FOSSEE/eSim/code/projectManagement/openProject.rst

Open Project Button
===========================

.. automodule:: projManagement.openProject
	:members:
