FOSSEE/eSim/images/chatbot.png

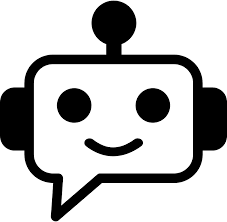
images/chatbot.png
