FOSSEE/eSim/images/esim_text.png

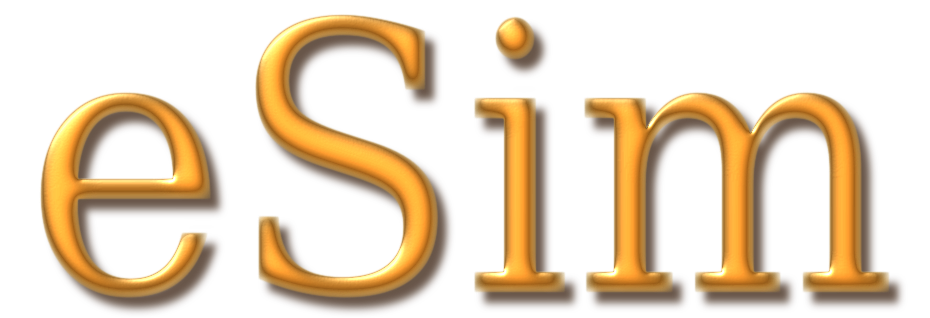
images/esim_text.png
