FOSSEE/eSim/images/footprint.png

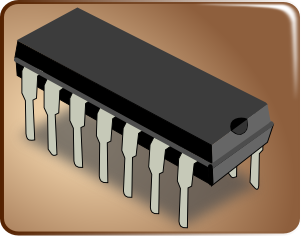
images/footprint.png
