FOSSEE/eSim/images/offline.png

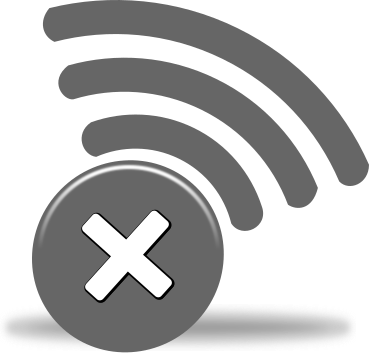
images/offline.png
