FOSSEE/eSim/images/openProject.png

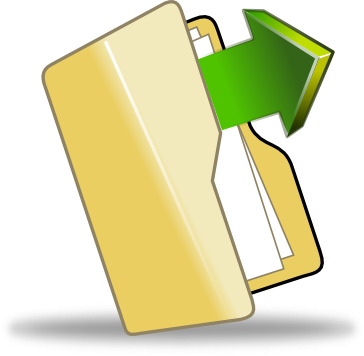
images/openProject.png
