FOSSEE/eSim/images/pcb.png

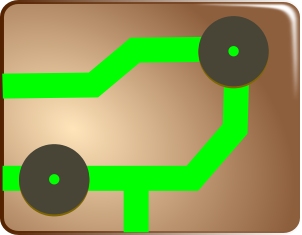
images/pcb.png
