FOSSEE/eSim/images/tracker.png

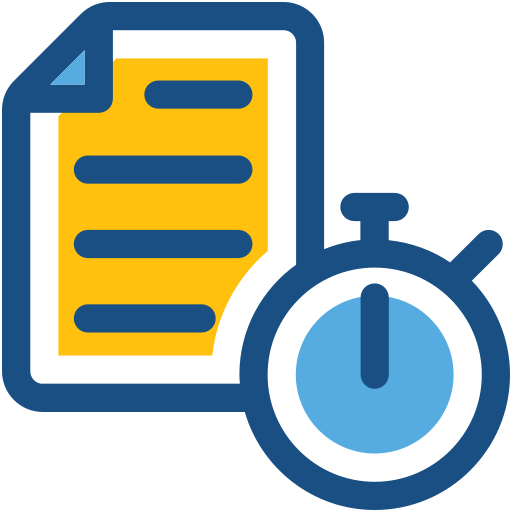
images/tracker.png
