FOSSEE/eSim/images/warning.png

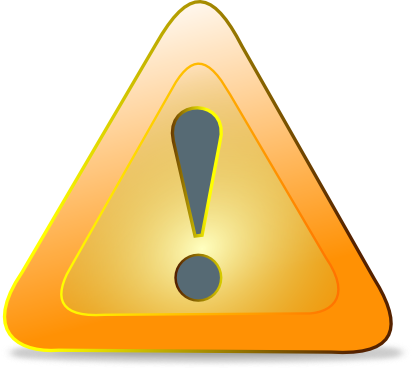
images/warning.png
