FOSSEE/eSim/SUBCKT/IC_GD74HCT58/IC_GD74HCT58.cir

.title KiCad schematic
U8 Net-_U2-Pad3_ Net-_U3-Pad3_ Net-_U11-Pad1_ d_nand
U11 Net-_U11-Pad1_ Net-_U11-Pad2_ d_inverter
U12 Net-_U11-Pad2_ Net-_U1-Pad12_ d_inverter
U1 Net-_U1-Pad1_ Net-_U1-Pad2_ Net-_U1-Pad3_ Net-_U1-Pad4_ Net-_U1-Pad5_ Net-_U1-Pad6_ Net-_U1-Pad7_ Net-_U1-Pad8_ Net-_U1-Pad9_ Net-_U1-Pad10_ Net-_U1-Pad11_ Net-_U1-Pad12_ PORT
U10 Net-_U10-Pad1_ Net-_U1-Pad10_ Net-_U10-Pad3_ d_nand
U9 Net-_U6-Pad3_ Net-_U1-Pad7_ Net-_U13-Pad1_ d_nand
U13 Net-_U13-Pad1_ Net-_U10-Pad3_ Net-_U13-Pad3_ d_nand
U15 Net-_U14-Pad2_ Net-_U1-Pad11_ d_inverter
U14 Net-_U13-Pad3_ Net-_U14-Pad2_ d_inverter
U4 Net-_U1-Pad5_ Net-_U1-Pad6_ Net-_U4-Pad3_ d_nand
U2 Net-_U1-Pad1_ Net-_U1-Pad2_ Net-_U2-Pad3_ d_nand
U3 Net-_U1-Pad3_ Net-_U1-Pad4_ Net-_U3-Pad3_ d_nand
U5 Net-_U1-Pad8_ Net-_U1-Pad9_ Net-_U5-Pad3_ d_nand
U7 Net-_U5-Pad3_ Net-_U5-Pad3_ Net-_U10-Pad1_ d_nand
U6 Net-_U4-Pad3_ Net-_U4-Pad3_ Net-_U6-Pad3_ d_nand
.end
