FOSSEE/eSim/Examples/4_bit_JK_ff/4_bit_JK_ff.sch

## KiCad design Examples/4_bit_JK_ff/4_bit_JK_ff.sch (2020-03-04)

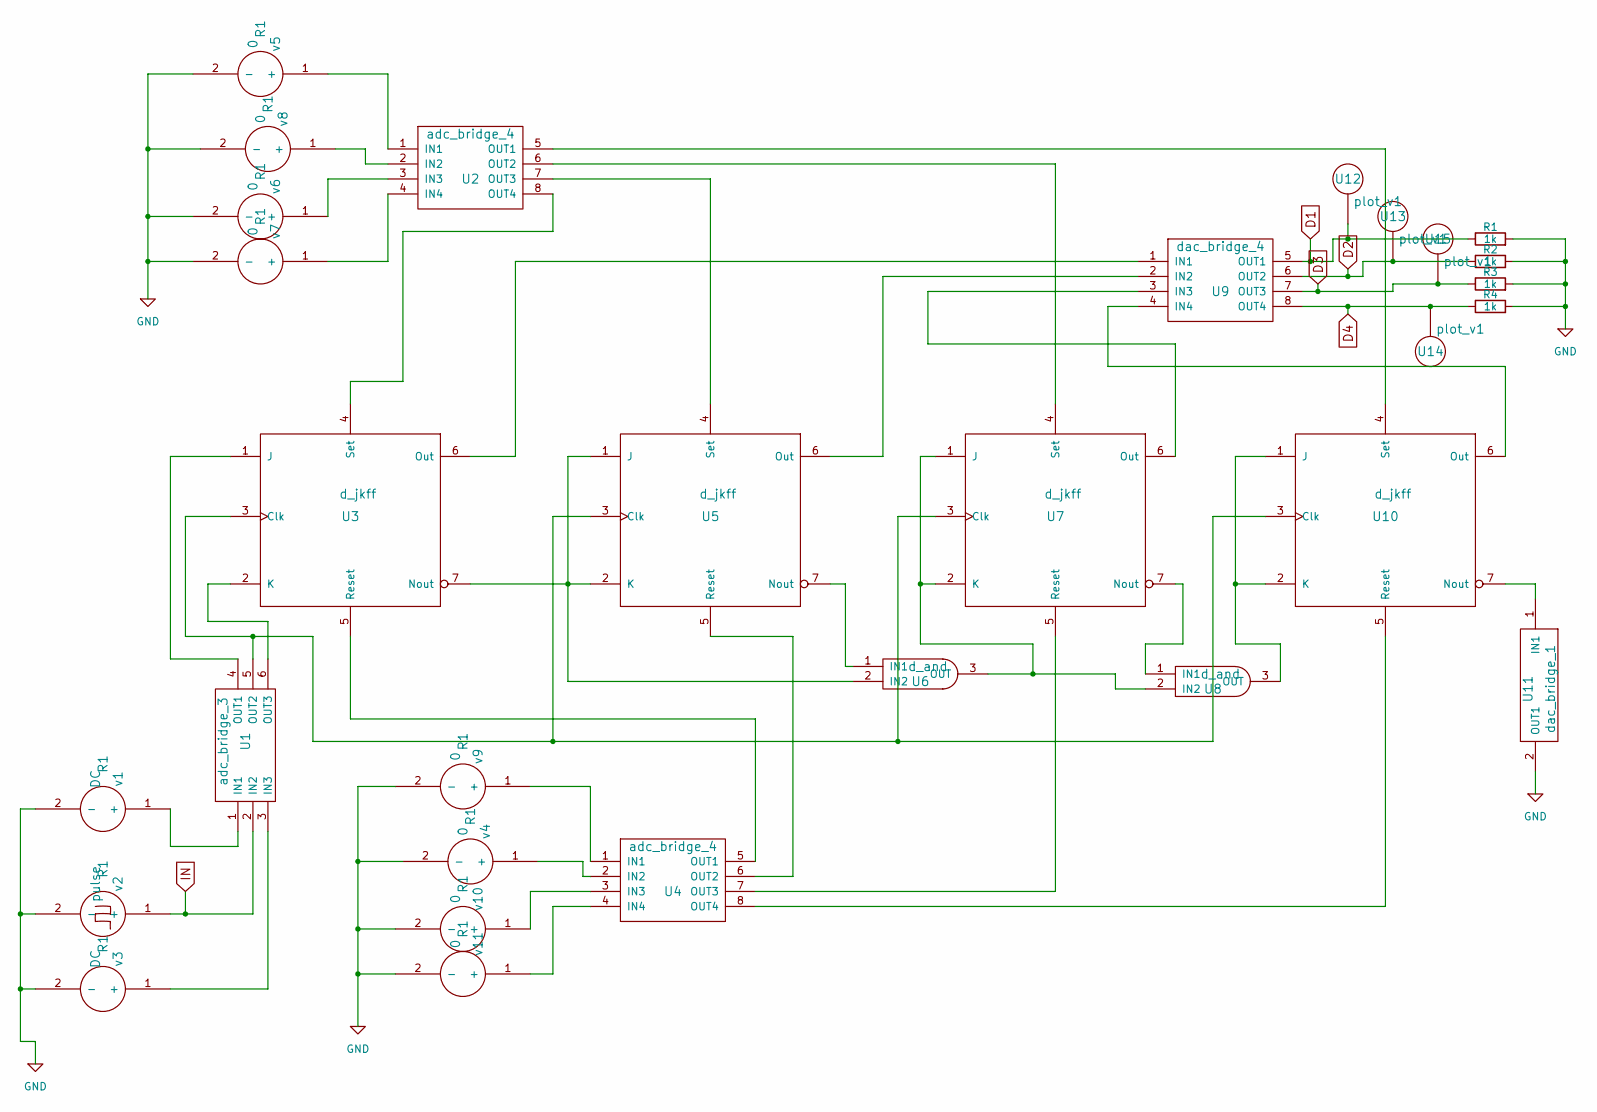
[picture p23: schematic 4_bit_JK_ff.sch]

Parts:
R1, R2, R3, R4: 1k
U1: adc_bridge_3
U2, U4: adc_bridge_4
U3, U5, U7, U10: d_jkff
U6, U8: d_and
U9: dac_bridge_4
U11: dac_bridge_1
U12, U13, U14, U15: plot_v1
v1, v3: DC; R1
v2: pulse; R1
v4, v5, v6, v7, v8, v9, v10, v11: 0; R1

Connections:
D1: R1.1, U9.5 (OUT1), U12.~
D2: R2.1, U9.6 (OUT2), U13.~
D3: R3.1, U9.7 (OUT3), U15.~
D4: R4.1, U9.8 (OUT4), U14.~
GND: R1.2, R2.2, R3.2, R4.2, U11.2 (OUT1), v1.2 (-), v2.2 (-), v3.2 (-), v4.2 (-), v5.2 (-), v6.2 (-), v7.2 (-), v8.2 (-), v9.2 (-), v10.2 (-), v11.2 (-)
IN: U1.2 (IN2), v2.1 (+)
unnamed: U1.1 (IN1), v1.1 (+)
unnamed: U1.3 (IN3), v3.1 (+)
unnamed: U1.4 (OUT1), U3.1 (J)
unnamed: U1.5 (OUT2), U3.3 (Clk), U5.3 (Clk), U7.3 (Clk), U10.3 (Clk)
unnamed: U1.6 (OUT3), U3.2 (K)
unnamed: U2.1 (IN1), v5.1 (+)
unnamed: U2.2 (IN2), v8.1 (+)
unnamed: U2.3 (IN3), v6.1 (+)
unnamed: U2.4 (IN4), v7.1 (+)
unnamed: U2.6 (OUT2), U7.4 (Set)
unnamed: U2.7 (OUT3), U5.4 (Set)
unnamed: U2.8 (OUT4), U3.4 (Set)
unnamed: U3.5 (Reset), U4.5 (OUT1)
unnamed: U3.6 (Out), U9.1 (IN1)
unnamed: U3.7 (Nout), U5.1 (J), U5.2 (K), U6.2 (IN2)
unnamed: U4.1 (IN1), v9.1 (+)
unnamed: U4.2 (IN2), v4.1 (+)
unnamed: U4.3 (IN3), v10.1 (+)
unnamed: U4.4 (IN4), v11.1 (+)
unnamed: U4.6 (OUT2), U5.5 (Reset)
unnamed: U4.7 (OUT3), U7.5 (Reset)
unnamed: U5.6 (Out), U9.2 (IN2)
unnamed: U5.7 (Nout), U6.1 (IN1)
unnamed: U6.3 (OUT), U7.1 (J), U7.2 (K), U8.2 (IN2)
unnamed: U7.6 (Out), U9.3 (IN3)
unnamed: U7.7 (Nout), U8.1 (IN1)
unnamed: U8.3 (OUT), U10.1 (J), U10.2 (K)
unnamed: U2.5 (OUT1), U10.4 (Set)
unnamed: U4.8 (OUT4), U10.5 (Reset)
unnamed: U9.4 (IN4), U10.6 (Out)
unnamed: U10.7 (Nout), U11.1 (IN1)
