FOSSEE/eSim/Examples/7805VoltageRegulator/7805VoltageRegulator.sch

## KiCad design Examples/7805VoltageRegulator/7805VoltageRegulator.sch (2020-03-04)

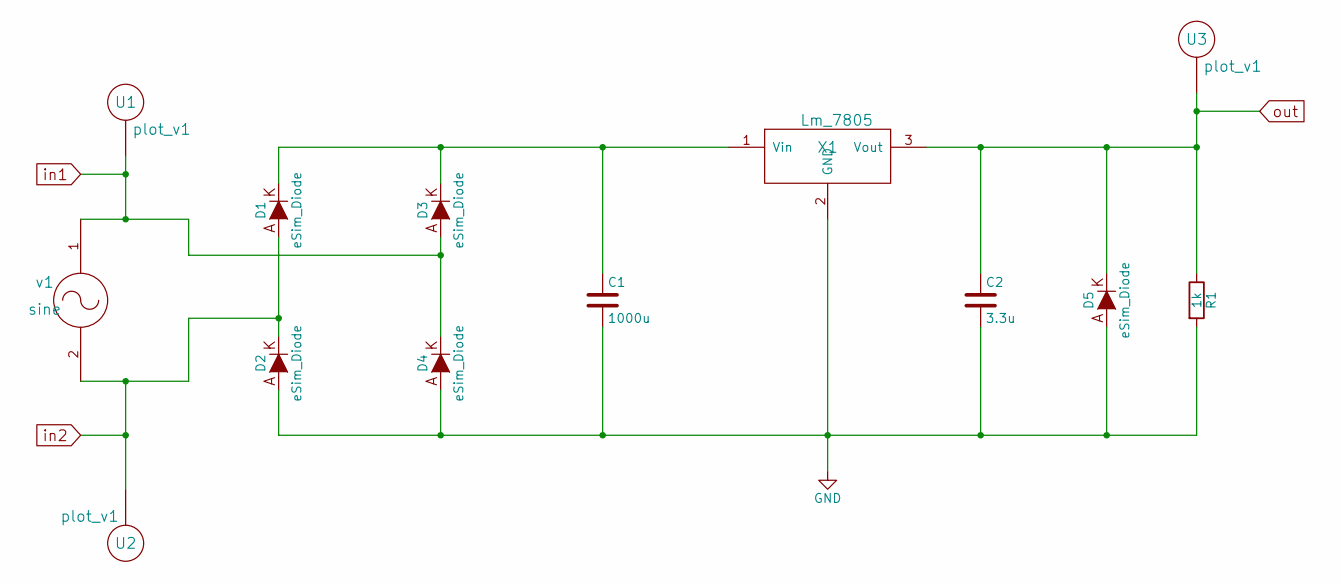
[picture p24: schematic 7805VoltageRegulator.sch]

Parts:
C1: 1000u
C2: 3.3u
D1, D2, D3, D4, D5: eSim_Diode
R1: 1k
U1, U2, U3: plot_v1
X1: Lm_7805
v1: sine

Connections:
GND: C1.2, C2.2, D2.1 (A), D4.1 (A), D5.1 (A), R1.2, X1.2 (GND)
unnamed: C1.1, D1.2 (K), D3.2 (K), X1.1 (Vin)
in1: D3.1 (A), D4.2 (K), U1.~, v1.1 (+)
in2: D1.1 (A), D2.2 (K), U2.~, v1.2 (-)
out: C2.1, D5.2 (K), R1.1, U3.~, X1.3 (Vout)
