FOSSEE/eSim/Examples/7805VoltageRegulator/lm7805.sch

## KiCad design Examples/7805VoltageRegulator/lm7805.sch (2020-03-04)

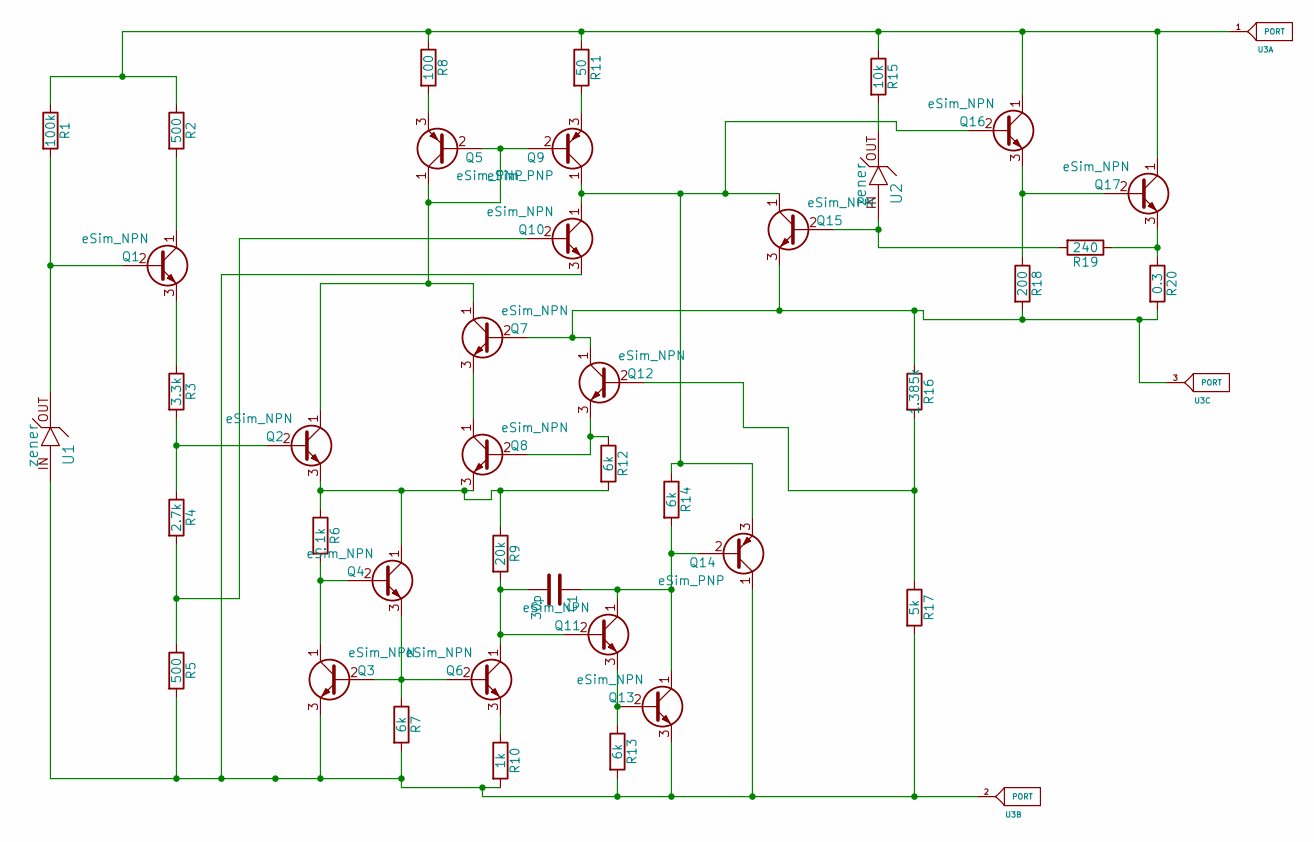
[picture p25: schematic lm7805.sch]

Parts:
C1: 30p
Q1, Q2, Q3, Q4, Q6, Q7, Q8, Q10, Q11, Q12, Q13, Q15, Q16, Q17: eSim_NPN
Q5, Q9, Q14: eSim_PNP
R1: 100k
R2, R5: 500
R3: 3.3k
R4: 2.7k
R6, R10: 1k
R7, R12, R13, R14: 6k
R8: 100
R9: 20k
R11: 50
R15: 10k
R16: 1.385k
R17: 5k
R18: 200
R19: 240
R20: 0.3
U1, U2: zener
U3: PORT

Connections:
unnamed: C1.1, Q11.1 (C), Q13.1 (C), Q14.2 (B), R14.2
unnamed: C1.2, Q6.1 (C), Q11.2 (B), R9.2
unnamed: Q1.1 (C), R2.2
unnamed: Q1.2 (B), R1.2, U1.OUT
unnamed: Q1.3 (E), R3.1
unnamed: Q2.1 (C), Q5.1 (C), Q5.2 (B), Q7.1 (C), Q9.2 (B)
unnamed: Q2.2 (B), R3.2, R4.1
unnamed: Q2.3 (E), Q4.1 (C), Q8.3 (E), R6.1, R9.1, R12.2
unnamed: Q3.1 (C), Q4.2 (B), R6.2
unnamed: Q3.2 (B), Q4.3 (E), Q6.2 (B), R7.1
unnamed: Q5.3 (E), R8.2
unnamed: Q6.3 (E), R10.1
unnamed: Q7.3 (E), Q8.1 (C)
unnamed: Q9.3 (E), R11.2
unnamed: Q9.1 (C), Q10.1 (C), Q14.3 (E), Q15.1 (C), Q16.2 (B), R14.1
unnamed: Q10.2 (B), R4.2, R5.1
unnamed: Q3.3 (E), Q10.3 (E), Q13.3 (E), Q14.1 (C), R5.2, R7.2, R10.2, R13.2, R17.2, U1.IN, U3.2
unnamed: Q11.3 (E), Q13.2 (B), R13.1
unnamed: Q7.2 (B), Q12.1 (C), Q15.3 (E), R16.1, R18.2, R20.2, U3.3
unnamed: Q12.2 (B), R16.2, R17.1
unnamed: Q8.2 (B), Q12.3 (E), R12.1
unnamed: Q15.2 (B), R19.2, U2.IN
unnamed: Q16.1 (C), Q17.1 (C), R1.1, R2.1, R8.1, R11.1, R15.1, U3.1
unnamed: Q16.3 (E), Q17.2 (B), R18.1
unnamed: Q17.3 (E), R19.1, R20.1
unnamed: R15.2, U2.OUT
