FOSSEE/eSim/Examples/Astable555/Astable555.sch

## KiCad design Examples/Astable555/Astable555.sch (2020-03-04)

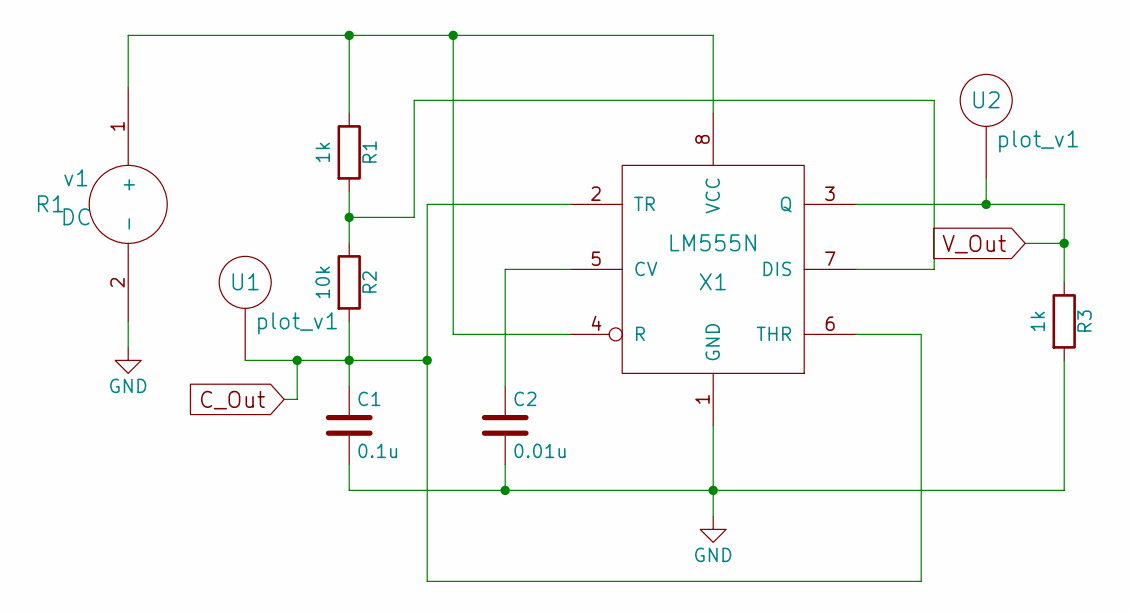
[picture p26: schematic Astable555.sch]

Parts:
C1: 0.1u
C2: 0.01u
R1, R3: 1k
R2: 10k
U1, U2: plot_v1
X1: LM555N
v1: DC; R1

Connections:
C_Out: C1.1, R2.2, U1.~, X1.2 (TR), X1.6 (THR)
GND: C1.2, C2.2, R3.2, X1.1 (GND), v1.2 (-)
unnamed: C2.1, X1.5 (CV)
unnamed: R1.1, X1.4 (R), X1.8 (VCC), v1.1 (+)
unnamed: R1.2, R2.1, X1.7 (DIS)
V_Out: R3.1, U2.~, X1.3 (Q)
