FOSSEE/eSim/Examples/BJT_Biascircuit/BJT_Biascircuit.sch

## KiCad design Examples/BJT_Biascircuit/BJT_Biascircuit.sch (2020-03-04)

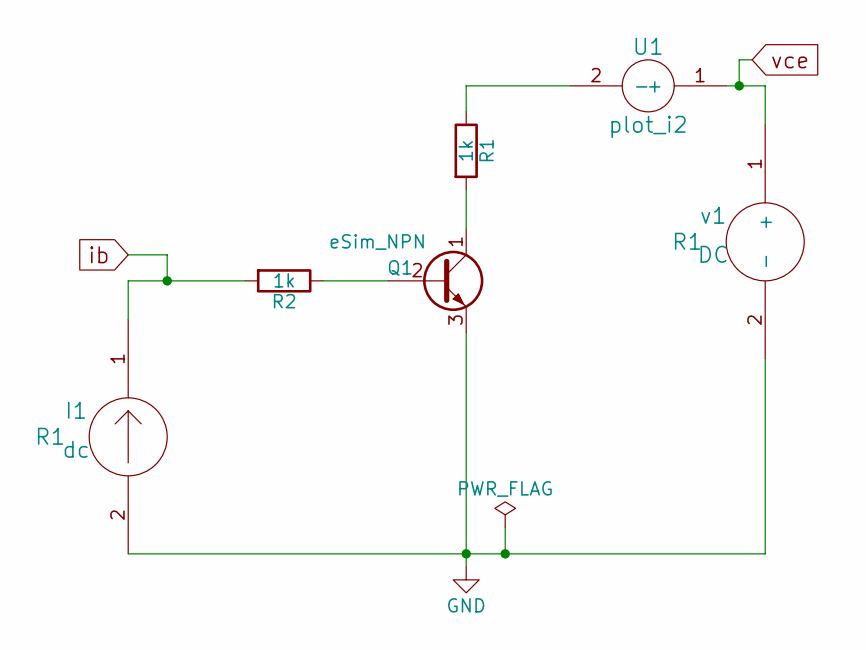
[picture p27: schematic BJT_Biascircuit.sch]

Parts:
I1: dc; R1
Q1: eSim_NPN
R1, R2: 1k
U1: plot_i2
v1: DC; R1

Connections:
GND: I1.2, Q1.3 (E), v1.2 (-)
unnamed: Q1.1 (C), R1.2
unnamed: Q1.2 (B), R2.1
unnamed: R1.1, U1.2 (-)
ib: I1.1, R2.2
vce: U1.1 (+), v1.1 (+)
