FOSSEE/eSim/Examples/BJT_CB_config/BJT_CB_config.sch

## KiCad design Examples/BJT_CB_config/BJT_CB_config.sch (2020-03-04)

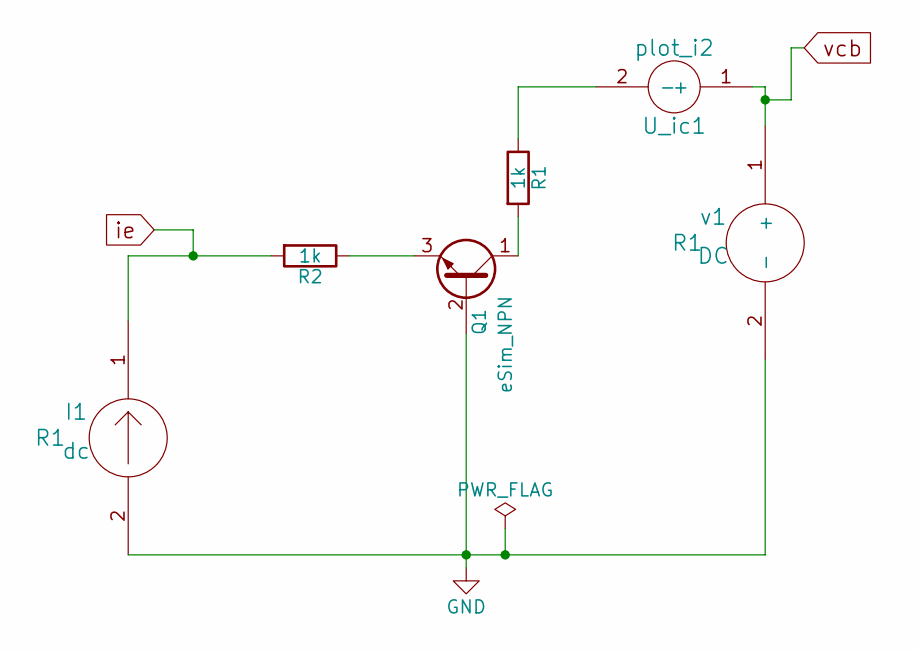
[picture p28: schematic BJT_CB_config.sch]

Parts:
I1: dc; R1
Q1: eSim_NPN
R1, R2: 1k
U_ic1: plot_i2
v1: DC; R1

Connections:
GND: I1.2, Q1.2 (B), v1.2 (-)
unnamed: Q1.1 (C), R1.2
unnamed: Q1.3 (E), R2.1
unnamed: R1.1, U_ic1.2 (-)
ie: I1.1, R2.2
vcb: U_ic1.1 (+), v1.1 (+)
