FOSSEE/eSim/Examples/BJT_Frequency_Response/BJT_Frequency_Response.sch

## KiCad design Examples/BJT_Frequency_Response/BJT_Frequency_Response.sch (2020-03-04)

Schematic: BJT_Frequency_Response.sch

Parts:
C1, C3: 40u
C2: 100u
Q1: eSim_NPN
R1: 50
R2: 200k
R3: 50k
R4: 1.5k
R5: 2k
R6: 1k
U1: plot_v1
U2: plot_phase
U3: plot_log
v1: DC; R1
v2: AC; R1
