FOSSEE/eSim/Examples/BJT_amplifier/BJT_amplifier.sch

## KiCad design Examples/BJT_amplifier/BJT_amplifier.sch (2020-03-04)

Schematic: BJT_amplifier.sch

Parts:
C1, C3: 40u
C2: 100u
Q1: eSim_NPN
R1: 50
R2: 200k
R3: 50k
R4: 1.5k
R5: 2k
R6: 1k
U1, U2: plot_v1
v1: DC; R1
v2: sine; R1
