FOSSEE/eSim/Examples/BasicGates/BasicGates.sch

## KiCad design Examples/BasicGates/BasicGates.sch (2016-03-03)

Schematic: BasicGates.sch

Parts:
R1, R2, R3: 1000
U1: adc_bridge_2
U2: d_and
U3: d_or
U4: d_nor
U5: d_nand
U6: d_inverter
U7: d_xor
U8: dac_bridge_1
U9, U10, U11: plot_v1
v1, v2: pulse; R1

Notes on the sheet:
~A.B
A.B
=~A
=A+B
A.B+A+B
~((A.B)+(A+B))
~((A.B).(A+B))
A+B
