FOSSEE/eSim/Examples/CMOS_NAND_Gate/CMOS_NAND.sch

## KiCad design Examples/CMOS_NAND_Gate/CMOS_NAND.sch (2020-04-24)

Schematic: CMOS_NAND.sch

Parts:
M1, M4: eSim_MOS_P
M2, M3: eSim_MOS_N
U1: PORT
v1: DC; R1

Notes on the sheet:
vcc
gnd
in1
in2
out
