FOSSEE/eSim/Examples/CMOS_NAND_Gate/CMOS_NAND_Gate.sch

## KiCad design Examples/CMOS_NAND_Gate/CMOS_NAND_Gate.sch (2020-04-24)

Schematic: CMOS_NAND_Gate.sch

Parts:
U1, U2, U3: plot_v1
X1: CMOS_NAND
v1, v2: pulse; R1
