FOSSEE/eSim/Examples/Clampercircuit/Clampercircuit.sch

## KiCad design Examples/Clampercircuit/Clampercircuit.sch (2020-03-04)

Schematic: Clampercircuit.sch

Parts:
C1, C2: 1n
D1, D2: D
U1, U2, U3, U4: plot_v1
v1, v2: sine; R1

Notes on the sheet:
Negative Clamper
Positive Clamper
