FOSSEE/eSim/Examples/Clippercircuit/Clippercircuit.sch

## KiCad design Examples/Clippercircuit/Clippercircuit.sch (2020-03-04)

Schematic: Clippercircuit.sch

Parts:
D1, D2: D
R1: 1k
U1, U2: plot_v1
v1: sine; R1
