FOSSEE/eSim/Examples/Differentiator/Differentiator.sch

## KiCad design Examples/Differentiator/Differentiator.sch (2020-03-30)

Schematic: Differentiator.sch

Parts:
C1: 10n
R1: 100k
R2, R3, R4: 1k
U1, U2: plot_v1
X1: lm_741
v1: pwl; R1
v2, v3: DC; R1
