FOSSEE/eSim/Examples/Differentiator/lm_741.sch

## KiCad design Examples/Differentiator/lm_741.sch (2020-03-30)

Schematic: lm_741.sch

Parts:
C1: 30p
Q1, Q2, Q3, Q7, Q8, Q12, Q13, Q14, Q15, Q16, Q17, Q18, Q20: eSim_NPN
Q4, Q5, Q6, Q9, Q10, Q11, Q19: eSim_PNP
R1, R3: 1k
R2, R5: 50k
R4: 5k
R6, R10: 50
R7: 7.5k
R8: 4.5k
R9: 25
R11: 39k
U1: PORT
