FOSSEE/eSim/Examples/Diode_characteristics/Diode_characteristics.sch

## KiCad design Examples/Diode_characteristics/Diode_characteristics.sch (2020-03-04)

Schematic: Diode_characteristics.sch

Parts:
D1: D
R1: 1k
U1: plot_i2
v1: DC; R1
