FOSSEE/eSim/Examples/FET_Amplifier/FET_Amplifier.sch

## KiCad design Examples/FET_Amplifier/FET_Amplifier.sch (2020-03-04)

Schematic: FET_Amplifier.sch

Parts:
C1: 1u
C6: 0.1u
J1: eSim_NJF
R2: 1Meg
R3: 3k
R4: 470
U1, U2: plot_v1
v1: sine; R1
v2: DC; R1
