FOSSEE/eSim/Examples/FET_Characteristic/FET_Characteristic.sch

## KiCad design Examples/FET_Characteristic/FET_Characteristic.sch (2020-03-04)

Schematic: FET_Characteristic.sch

Parts:
J1: eSim_NJF
U_id1: plot_i2
vds1: DC; R1
vgs1: DC; R1
