FOSSEE/eSim/Examples/FrequencyResponse_JFET/FrequencyResponse_JFET.sch

## KiCad design Examples/FrequencyResponse_JFET/FrequencyResponse_JFET.sch (2020-03-04)

Schematic: FrequencyResponse_JFET.sch

Parts:
C1: 1u
C6: 0.1u
J1: eSim_NJF
R2: 1Meg
R3: 3k
R4: 470
U1: plot_v1
U2: plot_phase
U3: plot_log
U4: plot_db
v1: AC; R1
v2: DC; R1
