FOSSEE/eSim/Examples/FullAdder/FullAdder.sch

## KiCad design Examples/FullAdder/FullAdder.sch (2020-03-11)

Schematic: FullAdder.sch

Parts:
R1, R2: 1k
U1, U2, U3, U4, U5: plot_v1
U6: adc_bridge_3
U7: dac_bridge_2
X1: full_adder
v1, v2, v3: DC; R1
