FOSSEE/eSim/Examples/FullwaveRectifier_SCR/FullwaveRectifier_SCR.sch

## KiCad design Examples/FullwaveRectifier_SCR/FullwaveRectifier_SCR.sch (2016-03-03)

Schematic: FullwaveRectifier_SCR.sch

Parts:
D1, D2, D3, D4: D
R1: 100
U1, U2: plot_v2
U3: plot_v1
v1: sine; R1
v2: pulse; R1
x1: SCR
