FOSSEE/eSim/Examples/FullwaveRectifier_SCR/scr.sch

## KiCad design Examples/FullwaveRectifier_SCR/scr.sch (2020-03-18)

Schematic: scr.sch

Parts:
C1: 10u
D1: D
F1: 10
F2: 100
R1: 50
R2: 1
U1: aswitch
U2: PORT
v1, v2: dc; R1
