FOSSEE/eSim/Examples/Fullwavebridgerectifier/Fullwavebridgerectifier.sch

## KiCad design Examples/Fullwavebridgerectifier/Fullwavebridgerectifier.sch (2020-03-04)

Schematic: Fullwavebridgerectifier.sch

Parts:
D1, D2, D3, D4: D
R1: 1k
U1: plot_v2
U2: plot_v1
v1: sine; R1
