FOSSEE/eSim/Examples/Half_Adder/Half_Adder.sch

## KiCad design Examples/Half_Adder/Half_Adder.sch (2020-03-11)

Schematic: Half_Adder.sch

Parts:
R1, R2: 1k
U1: adc_bridge_2
U2: dac_bridge_2
U3, U4, U5, U6: plot_v1
X1: half_adder
v1, v2: DC; R1
