FOSSEE/eSim/Examples/HalfwaveRectifier_SCR/HalfwaveRectifier_SCR.sch

## KiCad design Examples/HalfwaveRectifier_SCR/HalfwaveRectifier_SCR.sch (2016-03-03)

Schematic: HalfwaveRectifier_SCR.sch

Parts:
R1: 100
U1, U3: plot_v1
U2: plot_v2
X1: SCR
v1: sine; R1
v2: pulse; R1
