FOSSEE/eSim/Examples/Halfwave_Rectifier/Halfwave_Rectifier.sch

## KiCad design Examples/Halfwave_Rectifier/Halfwave_Rectifier.sch (2020-03-04)

Schematic: Halfwave_Rectifier.sch

Parts:
D1: D
R1: 1k
U2, U3: plot_v1
v1: sine; R1
