FOSSEE/eSim/Examples/High_Pass_Filter/High_Pass_Filter.sch

## KiCad design Examples/High_Pass_Filter/High_Pass_Filter.sch (2016-03-03)

Schematic: High_Pass_Filter.sch

Parts:
C1: 10u
R1: 1k
U1, U3: plot_v1
U2: plot_log
v1: AC; R1
