FOSSEE/eSim/Examples/Integrator_LM_741/Integrator_LM_741.sch

## KiCad design Examples/Integrator_LM_741/Integrator_LM_741.sch (2020-03-11)

Schematic: Integrator_LM_741.sch

Parts:
C1: 0.47u
R1: 10k
R2: 100
R3: 1k
R4: 1.8533k
U1, U2: plot_v1
X1: lm_741
v1: sine; R1
v2: +15; R1
v3: -15; R1
