FOSSEE/eSim/Examples/InvertingAmplifier/InvertingAmplifier.sch

## KiCad design Examples/InvertingAmplifier/InvertingAmplifier.sch (2020-03-30)

Schematic: InvertingAmplifier.sch

Parts:
R1, R2, R4: 1k
R3: 5k
U1, U2: plot_v1
X1: lm_741
v1: sine; R1
v2, v3: 12; R1
