FOSSEE/eSim/Examples/JK_Flipflop/JK_Flipflop.sch

## KiCad design Examples/JK_Flipflop/JK_Flipflop.sch (2020-03-11)

Schematic: JK_Flipflop.sch

Parts:
R1, R2: 1k
U1, U2, U3, U4, U5: plot_v1
U6: adc_bridge_3
U7: dac_bridge_2
U8, U10: adc_bridge_1
U9: d_jkff
v1, v3: DC; R1
v2: pulse; R1
v4, v5: 0; R1
