FOSSEE/eSim/Examples/Low_Pass_Filter/Low_Pass_Filter.sch

## KiCad design Examples/Low_Pass_Filter/Low_Pass_Filter.sch (2016-03-03)

Schematic: Low_Pass_Filter.sch

Parts:
C1: 10u
R1: 1k
U1, U2: plot_v1
U3: plot_log
v1: AC; R1
