FOSSEE/eSim/Examples/Monostable555/Monostable555.sch

## KiCad design Examples/Monostable555/Monostable555.sch (2020-03-04)

Schematic: Monostable555.sch

Parts:
C1: 1u
C2: 0.01u
R1, R2: 1k
U2, U4, U5: plot_v1
U3: IC
X1: LM555N
v1: DC; R1
v2: pulse; R1

Notes on the sheet:
monostable
multivibrator
using LM555N
