FOSSEE/eSim/Examples/Monostable555/lm555n.sch

## KiCad design Examples/Monostable555/lm555n.sch (2020-03-18)

Schematic: lm555n.sch

Parts:
E1, E2: 10000
Q1: eSim_NPN
R1, R2, R3: 5000
R4, R5: 2E6
R6, R7: 25
R8: 1500
U1: PORT
U2, U3: limit
U4, U5, U6: adc_bridge_1
U7: d_inverter
U8: d_srlatch
U9, U10: dac_bridge_1

Notes on the sheet:
IC 555
