FOSSEE/eSim/Examples/Parallel_Resonance/Parallel_Resonance.sch

## KiCad design Examples/Parallel_Resonance/Parallel_Resonance.sch (2020-03-04)

Schematic: Parallel_Resonance.sch

Parts:
C1: 10u
L1: 100m
R1: 100
R2: 1000
U1, U3: plot_v1
v1: AC; R1
