FOSSEE/eSim/Examples/Precision_Rectifiers_using_LM741/Precision_Rectifiers_using_LM741.sch

## KiCad design Examples/Precision_Rectifiers_using_LM741/Precision_Rectifiers_using_LM741.sch (2020-03-30)

Schematic: Precision_Rectifiers_using_LM741.sch

Parts:
D1, D2, D3, D4: eSim_Diode
R1, R2, R4, R5, R7, R8, R9: 1k
R3: 1.135k
R6: 0.5k
U1, U2, U3, U4: plot_v1
X1, X2, X3: lm_741
v1, v2, v3, v6, v7, v8: 12; R1
v4, v5: sine; R1

Notes on the sheet:
Precision HWR using lm_741
Precision FWR using lm_741
