FOSSEE/eSim/Examples/RC/RC.sch

## KiCad design Examples/RC/RC.sch (2020-03-04)

Schematic: RC.sch

Parts:
C1: 10u
R1: 1k
U1, U2: plot_v1
v1: pwl; R1
