FOSSEE/eSim/Examples/RL/RL.sch

## KiCad design Examples/RL/RL.sch (2016-03-03)

Schematic: RL.sch

Parts:
L1: 100m
R1: 10
U1, U2: plot_v1
v1: pwl; R1
