FOSSEE/eSim/Examples/RLC/RLC.sch

## KiCad design Examples/RLC/RLC.sch (2016-03-03)

Schematic: RLC.sch

Parts:
C1: 0.5u
L1: 2
R1: 1k
U1, U2: plot_v1
v1: pwl; R1
