FOSSEE/eSim/Examples/Series_Resonance/Series_Resonance.sch

## KiCad design Examples/Series_Resonance/Series_Resonance.sch (2016-03-03)

Schematic: Series_Resonance.sch

Parts:
C1: 10u
L1: 100m
R1: 1
U1, U2: plot_v1
v1: AC; R1
