FOSSEE/eSim/Examples/Transformer/Transformer.sch

## KiCad design Examples/Transformer/Transformer.sch (2020-03-04)

Schematic: Transformer.sch

Parts:
R1, R2: 1k
U1: TRANSFO
U2, U3: plot_v1
v1: sine; R1
