FOSSEE/eSim/Examples/UJT_Relaxation_Oscillator/UJT_Relaxation_Oscillator.sch

## KiCad design Examples/UJT_Relaxation_Oscillator/UJT_Relaxation_Oscillator.sch (2020-03-04)

Schematic: UJT_Relaxation_Oscillator.sch

Parts:
C1: 100n
R1: 95.3k
R2: 4.7K
R3: 4.7k
U1, U2: plot_v1
X1: UJT
v1: DC; R1
