FOSSEE/eSim/Examples/Zener_Characteristic/Zener_Characteristic.sch

## KiCad design Examples/Zener_Characteristic/Zener_Characteristic.sch (2020-03-11)

Schematic: Zener_Characteristic.sch

Parts:
R1: 1k
U1: zener
U2: plot_i2
U3: plot_v1
v1: DC; R1
