FOSSEE/eSim/SUBCKT/IC_74LS31/IC_74LS31.kicad_sch

## KiCad design SUBCKT/IC_74LS31/IC_74LS31.kicad_sch (2026-06-08)

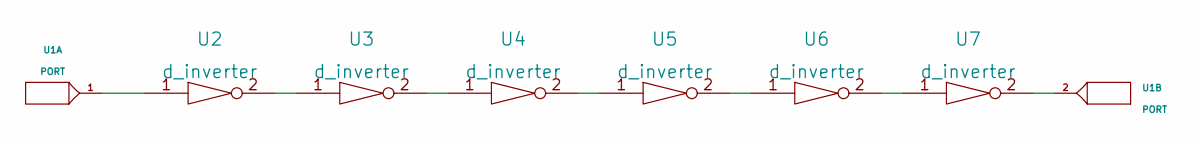
[picture p29: schematic IC_74LS31.kicad_sch]

Parts:
U1: PORT
U2, U3, U4, U5, U6, U7: d_inverter

Connections:
unnamed: U1.1, U2.1
unnamed: U1.2, U7.2
unnamed: U2.2, U3.1
unnamed: U3.2, U4.1
unnamed: U4.2, U5.1
unnamed: U5.2, U6.1
unnamed: U6.2, U7.1
