FOSSEE/eSim/SUBCKT/IC_CD74AC174/IC_CD74AC174.kicad_sch

## KiCad design SUBCKT/IC_CD74AC174/IC_CD74AC174.kicad_sch (2026-06-08)

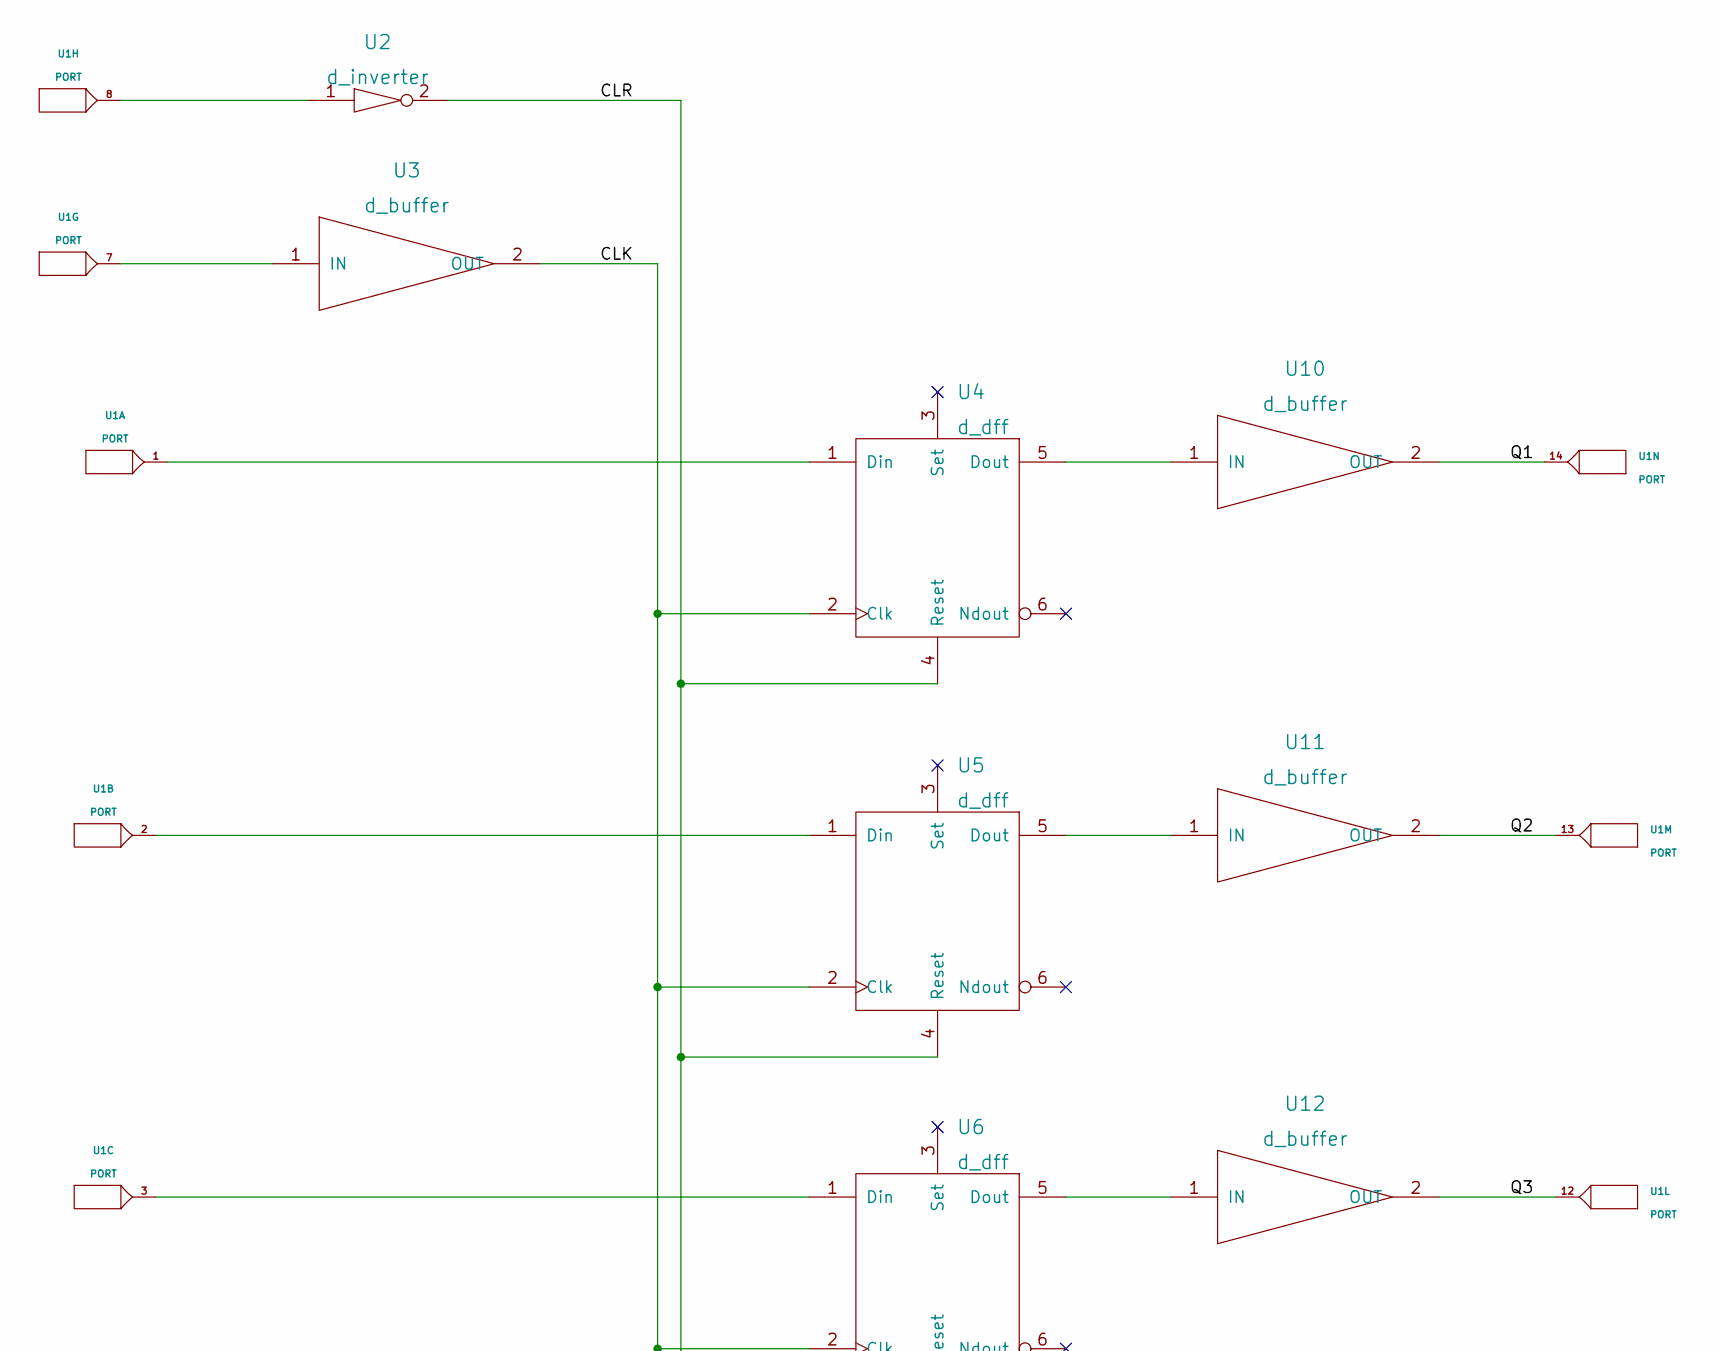
[picture p30: schematic IC_CD74AC174.kicad_sch, part in row 1, column 1]

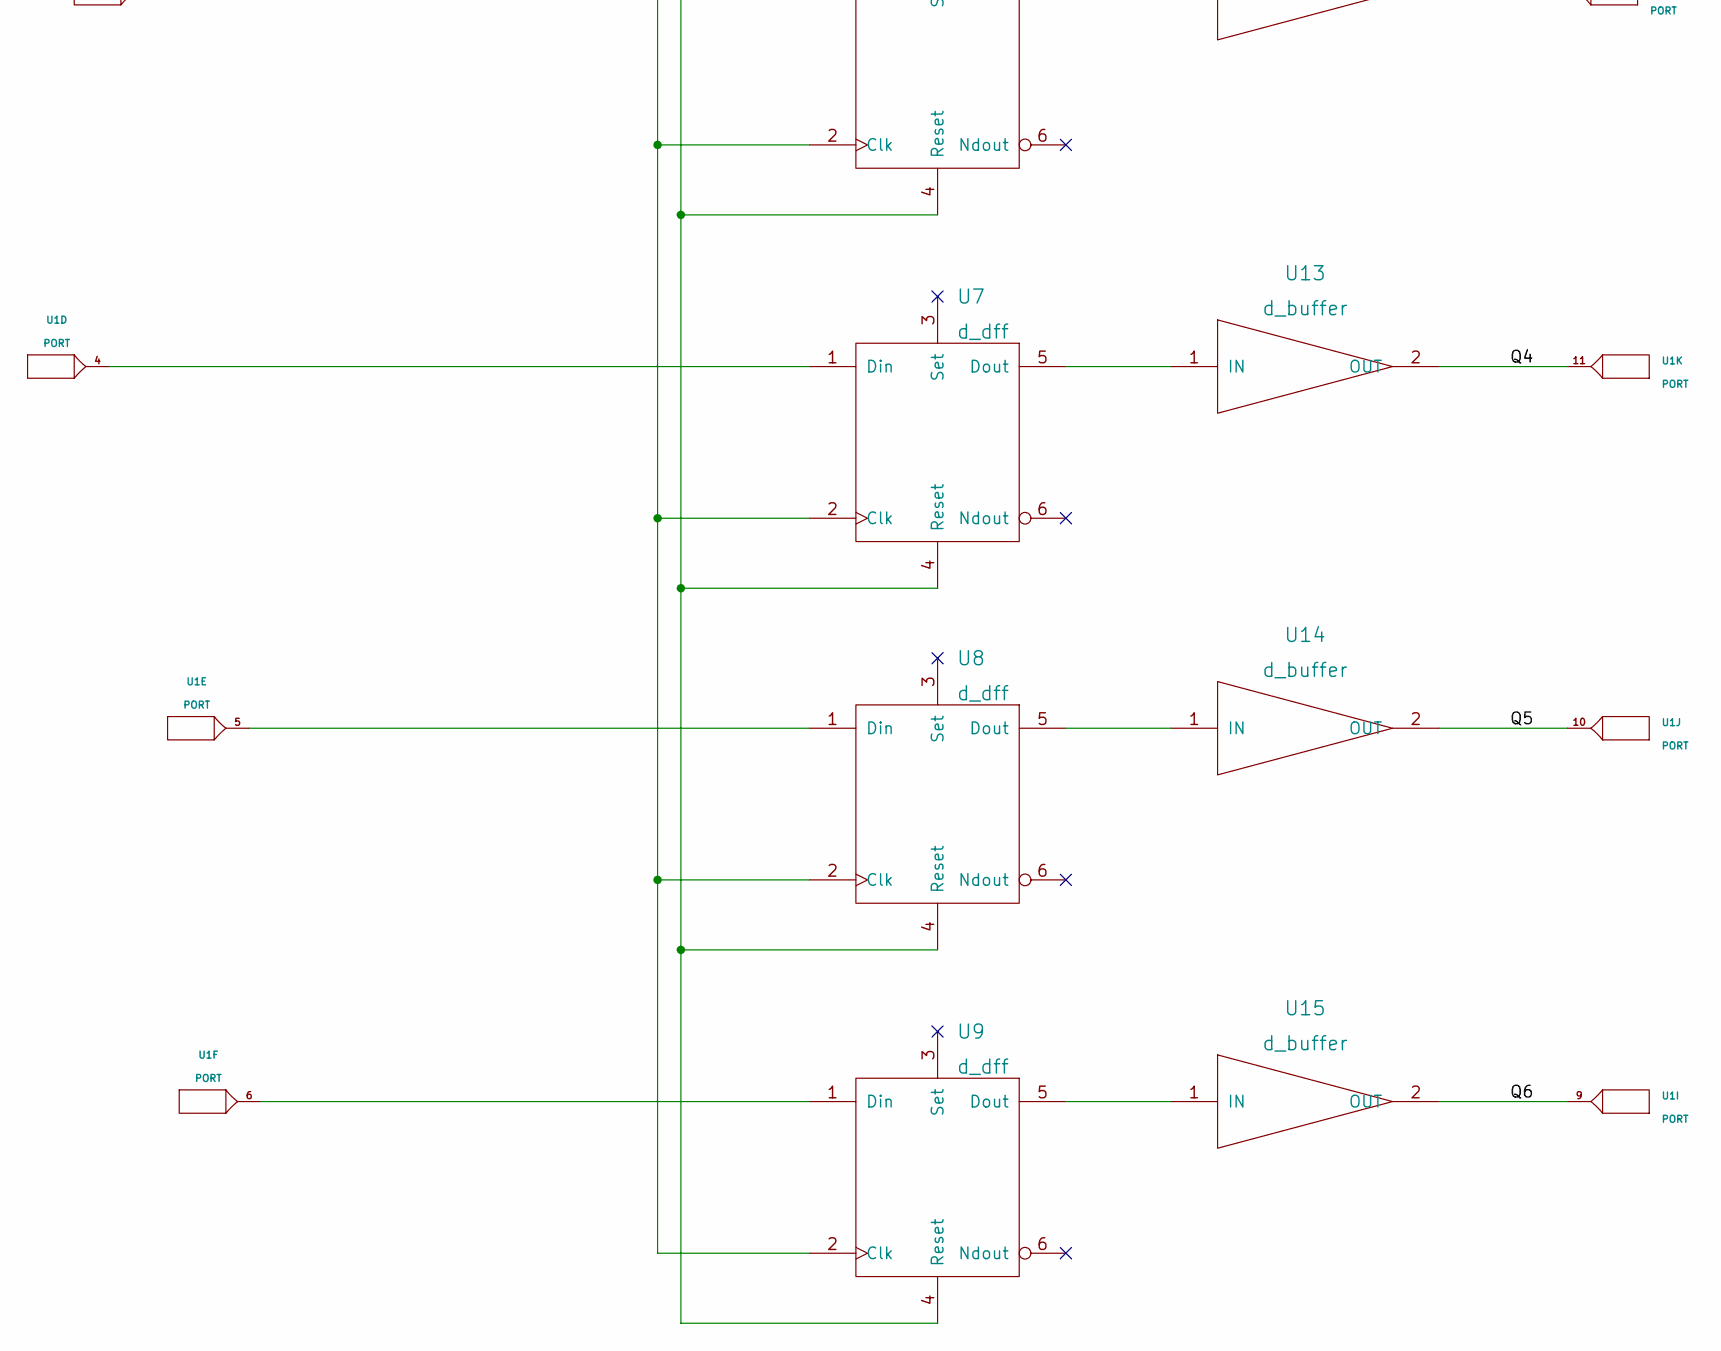
[picture p31: schematic IC_CD74AC174.kicad_sch, part in row 2, column 1]

Parts:
U1: PORT
U2: d_inverter
U3, U10, U11, U12, U13, U14, U15: d_buffer
U4, U5, U6, U7, U8, U9: d_dff

Connections:
CLK: U3.2 (OUT), U4.2 (Clk), U5.2 (Clk), U6.2 (Clk), U7.2 (Clk), U8.2 (Clk), U9.2 (Clk)
CLR: U2.2, U4.4 (Reset), U5.4 (Reset), U6.4 (Reset), U7.4 (Reset), U8.4 (Reset), U9.4 (Reset)
unnamed: U1.1, U4.1 (Din)
unnamed: U1.2, U5.1 (Din)
unnamed: U1.3, U6.1 (Din)
unnamed: U1.4, U7.1 (Din)
unnamed: U1.5, U8.1 (Din)
unnamed: U1.6, U9.1 (Din)
unnamed: U1.7, U3.1 (IN)
unnamed: U1.8, U2.1
unnamed: U4.5 (Dout), U10.1 (IN)
unnamed: U5.5 (Dout), U11.1 (IN)
unnamed: U6.5 (Dout), U12.1 (IN)
unnamed: U7.5 (Dout), U13.1 (IN)
unnamed: U8.5 (Dout), U14.1 (IN)
unnamed: U9.5 (Dout), U15.1 (IN)
Q1: U1.14, U10.2 (OUT)
Q2: U1.13, U11.2 (OUT)
Q3: U1.12, U12.2 (OUT)
Q4: U1.11, U13.2 (OUT)
Q5: U1.10, U14.2 (OUT)
Q6: U1.9, U15.2 (OUT)
