FOSSEE/eSim/SUBCKT/IC_CD74HC533/IC_CD74HC533.kicad_sch

## KiCad design SUBCKT/IC_CD74HC533/IC_CD74HC533.kicad_sch (2026-06-08)

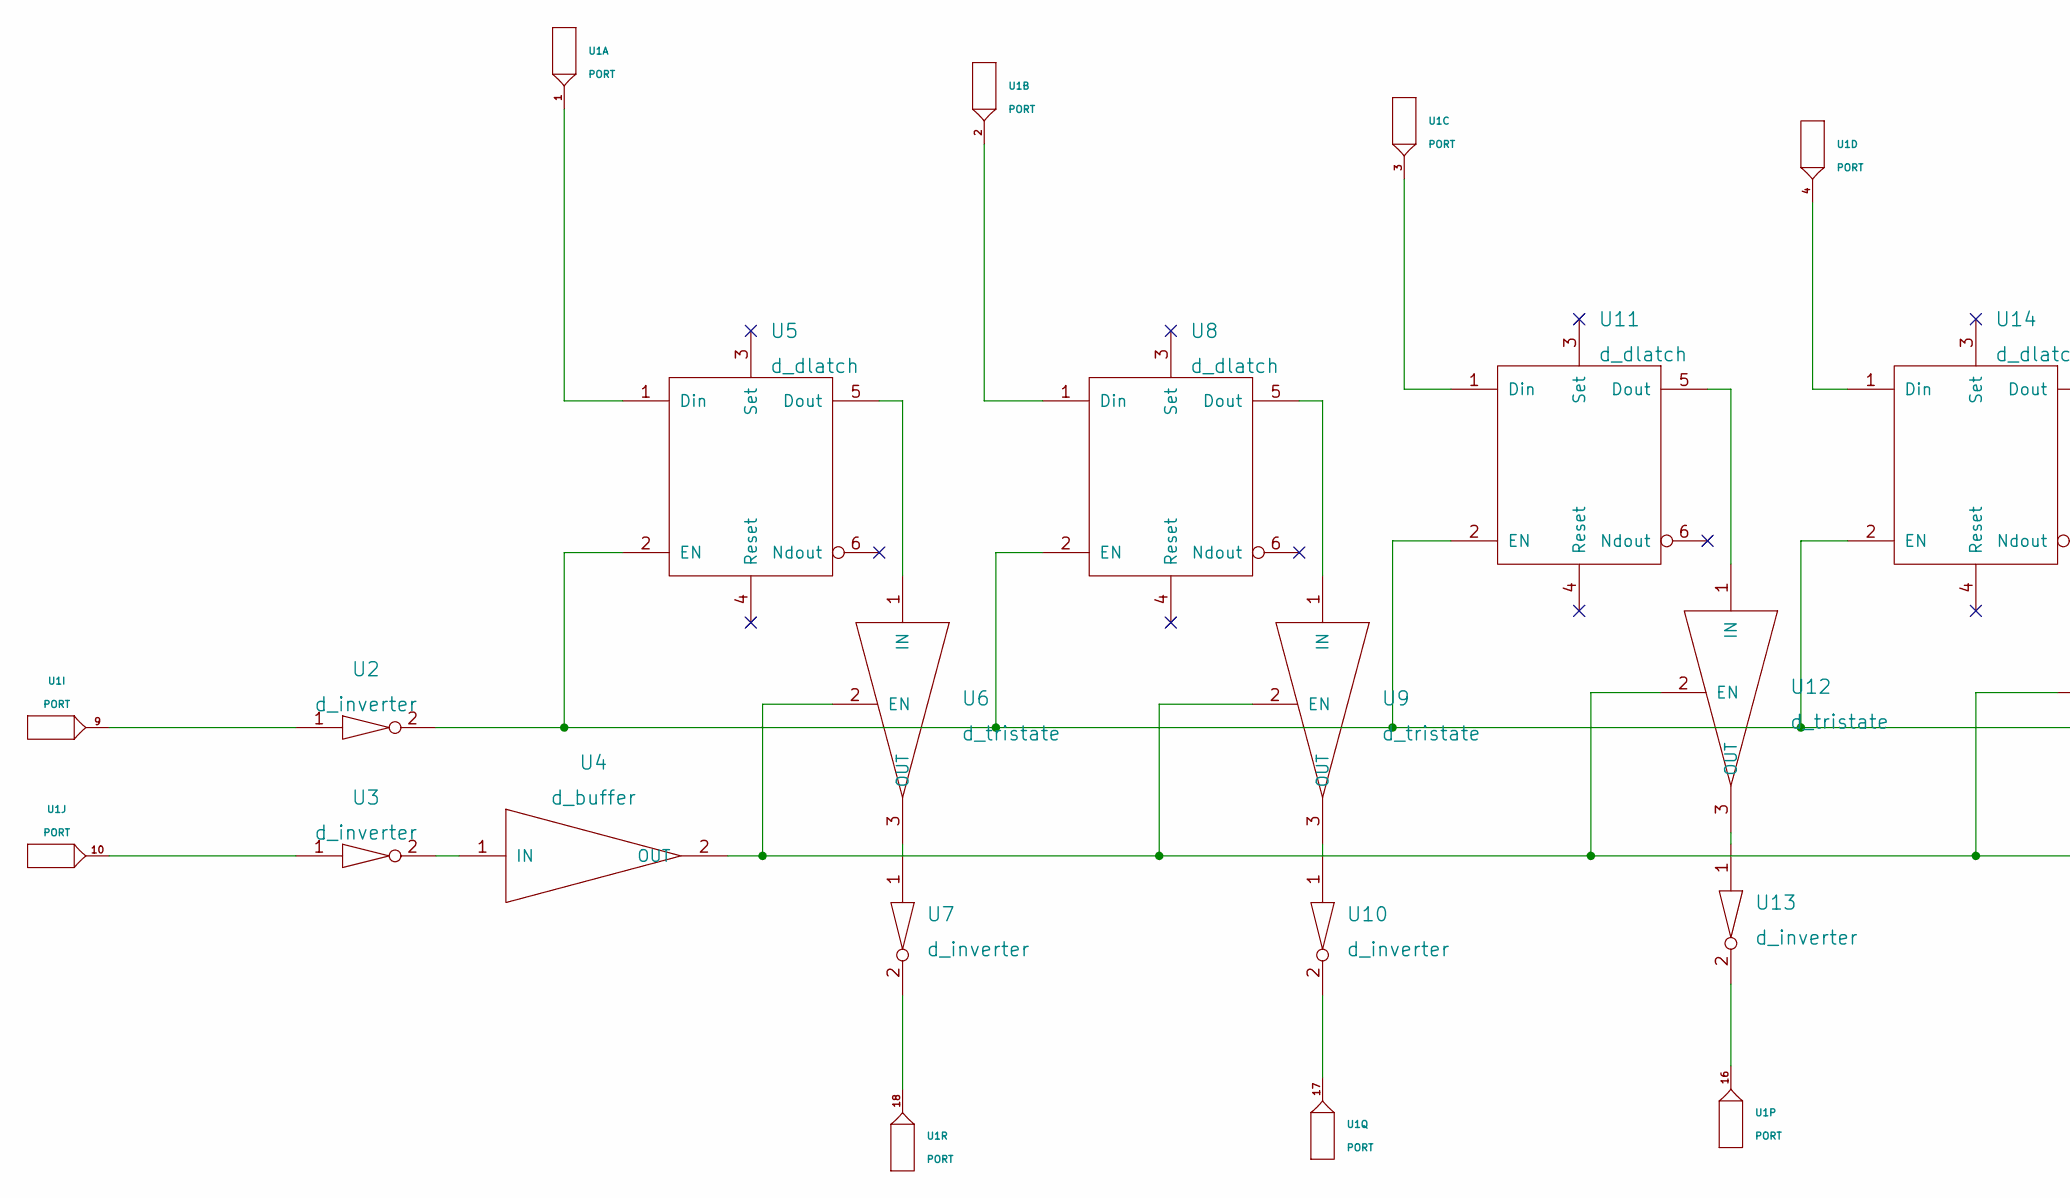
[picture p32: schematic IC_CD74HC533.kicad_sch, part in row 1, column 1]

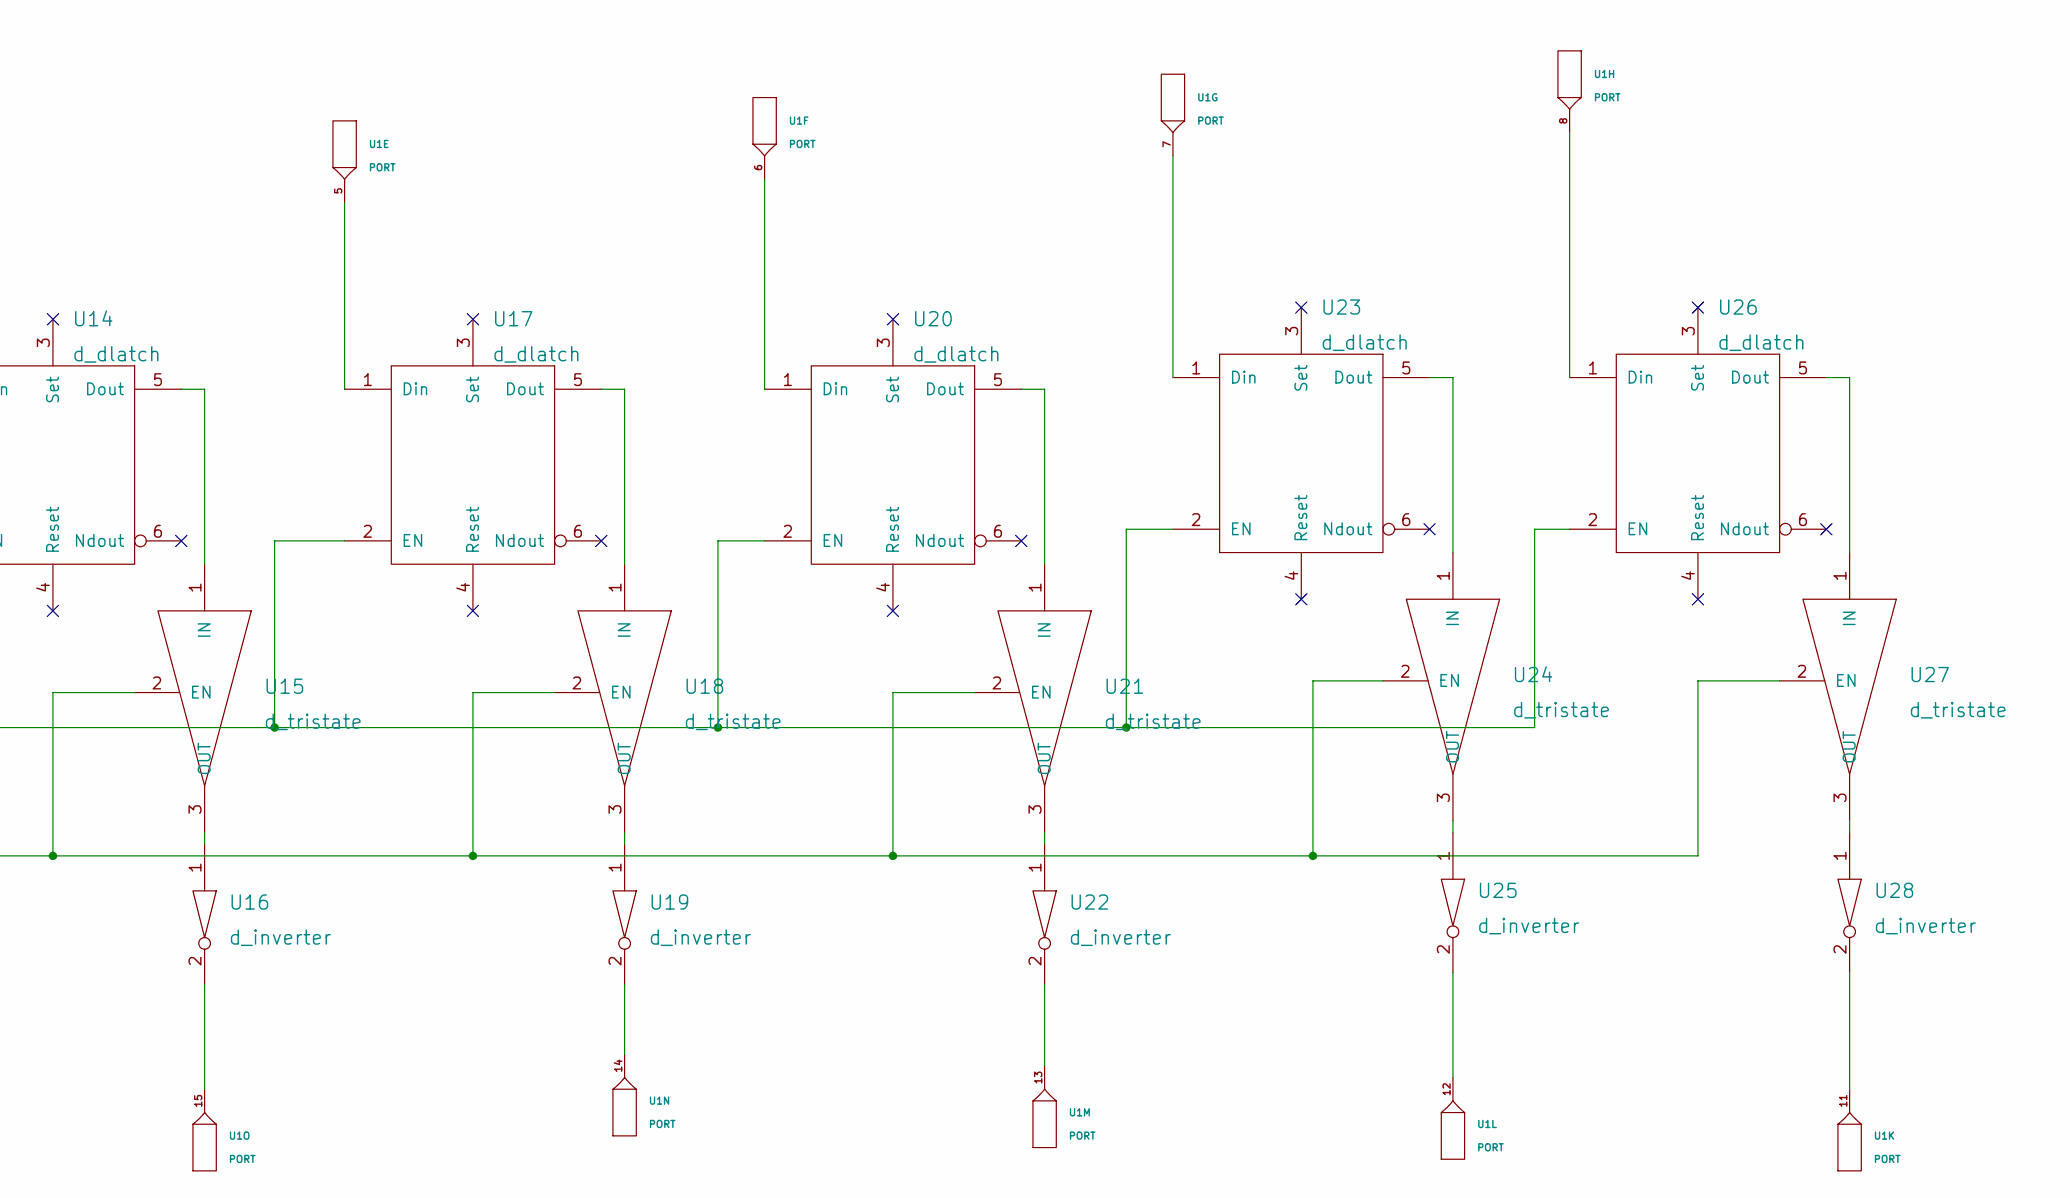
[picture p33: schematic IC_CD74HC533.kicad_sch, part in row 1, column 2]

Parts:
U1: PORT
U2, U3, U7, U10, U13, U16, U19, U22, U25, U28: d_inverter
U4: d_buffer
U5, U8, U11, U14, U17, U20, U23, U26: d_dlatch
U6, U9, U12, U15, U18, U21, U24, U27: d_tristate

Connections:
unnamed: U1.1, U5.1 (Din)
unnamed: U1.2, U8.1 (Din)
unnamed: U1.3, U11.1 (Din)
unnamed: U1.4, U14.1 (Din)
unnamed: U1.5, U17.1 (Din)
unnamed: U1.6, U20.1 (Din)
unnamed: U1.7, U23.1 (Din)
unnamed: U1.8, U26.1 (Din)
unnamed: U1.9, U2.1
unnamed: U1.10, U3.1
unnamed: U1.11, U28.2
unnamed: U1.12, U25.2
unnamed: U1.13, U22.2
unnamed: U1.14, U19.2
unnamed: U1.15, U16.2
unnamed: U1.16, U13.2
unnamed: U1.17, U10.2
unnamed: U1.18, U7.2
unnamed: U3.2, U4.1 (IN)
unnamed: U5.5 (Dout), U6.1 (IN)
unnamed: U6.3 (OUT), U7.1
unnamed: U8.5 (Dout), U9.1 (IN)
unnamed: U9.3 (OUT), U10.1
unnamed: U2.2, U5.2 (EN), U8.2 (EN), U11.2 (EN), U14.2 (EN), U17.2 (EN), U20.2 (EN), U23.2 (EN), U26.2 (EN)
unnamed: U11.5 (Dout), U12.1 (IN)
unnamed: U4.2 (OUT), U6.2 (EN), U9.2 (EN), U12.2 (EN), U15.2 (EN), U18.2 (EN), U21.2 (EN), U24.2 (EN), U27.2 (EN)
unnamed: U12.3 (OUT), U13.1
unnamed: U14.5 (Dout), U15.1 (IN)
unnamed: U15.3 (OUT), U16.1
unnamed: U17.5 (Dout), U18.1 (IN)
unnamed: U18.3 (OUT), U19.1
unnamed: U20.5 (Dout), U21.1 (IN)
unnamed: U21.3 (OUT), U22.1
unnamed: U23.5 (Dout), U24.1 (IN)
unnamed: U24.3 (OUT), U25.1
unnamed: U26.5 (Dout), U27.1 (IN)
unnamed: U27.3 (OUT), U28.1
