FOSSEE/eSim/SUBCKT/IC_DM8098/IC_DM8098.kicad_sch

## KiCad design SUBCKT/IC_DM8098/IC_DM8098.kicad_sch (2026-06-08)

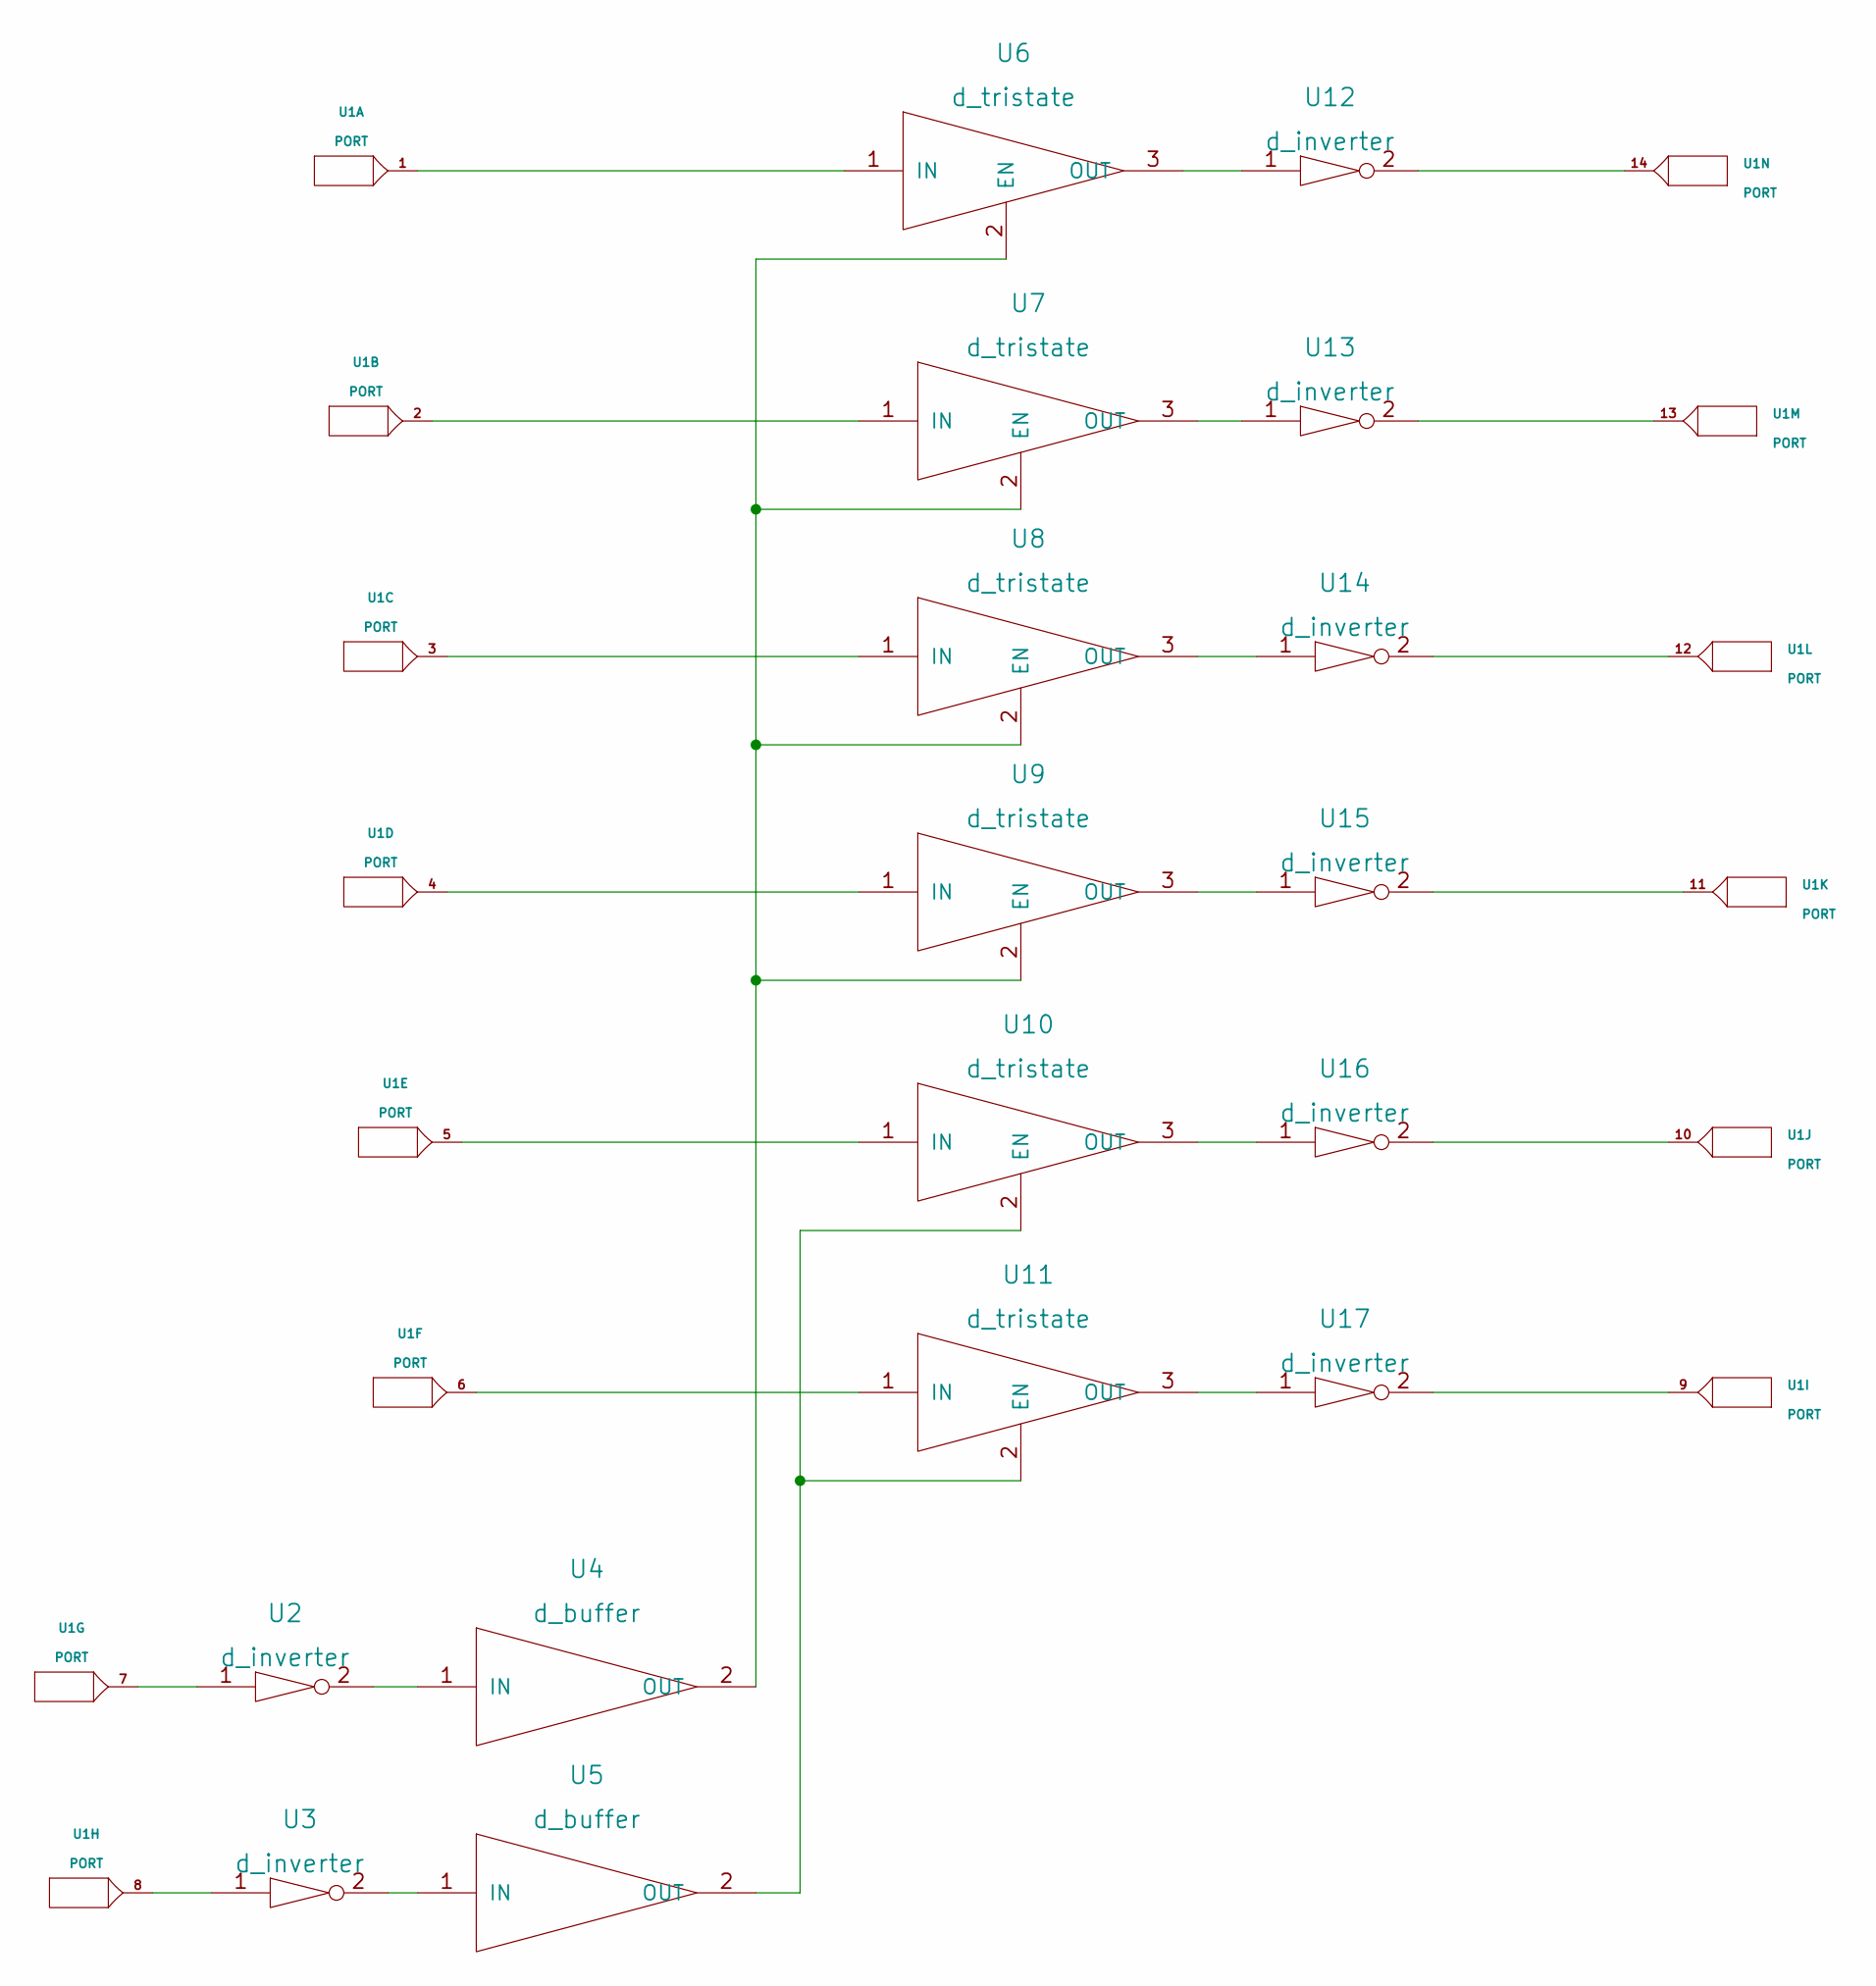
[picture p34: schematic IC_DM8098.kicad_sch]

Parts:
U1: PORT
U2, U3, U12, U13, U14, U15, U16, U17: d_inverter
U4, U5: d_buffer
U6, U7, U8, U9, U10, U11: d_tristate

Connections:
unnamed: U1.1, U6.1 (IN)
unnamed: U1.2, U7.1 (IN)
unnamed: U1.3, U8.1 (IN)
unnamed: U1.4, U9.1 (IN)
unnamed: U1.5, U10.1 (IN)
unnamed: U1.6, U11.1 (IN)
unnamed: U1.7, U2.1
unnamed: U1.8, U3.1
unnamed: U1.9, U17.2
unnamed: U1.10, U16.2
unnamed: U1.11, U15.2
unnamed: U1.12, U14.2
unnamed: U1.13, U13.2
unnamed: U1.14, U12.2
unnamed: U2.2, U4.1 (IN)
unnamed: U3.2, U5.1 (IN)
unnamed: U4.2 (OUT), U6.2 (EN), U7.2 (EN), U8.2 (EN), U9.2 (EN)
unnamed: U5.2 (OUT), U10.2 (EN), U11.2 (EN)
unnamed: U10.3 (OUT), U16.1
unnamed: U11.3 (OUT), U17.1
unnamed: U6.3 (OUT), U12.1
unnamed: U7.3 (OUT), U13.1
unnamed: U8.3 (OUT), U14.1
unnamed: U9.3 (OUT), U15.1
