FOSSEE/eSim/SUBCKT/IC_GD74HCT58/IC_GD74HCT58.kicad_sch

## KiCad design SUBCKT/IC_GD74HCT58/IC_GD74HCT58.kicad_sch (2026-06-08)

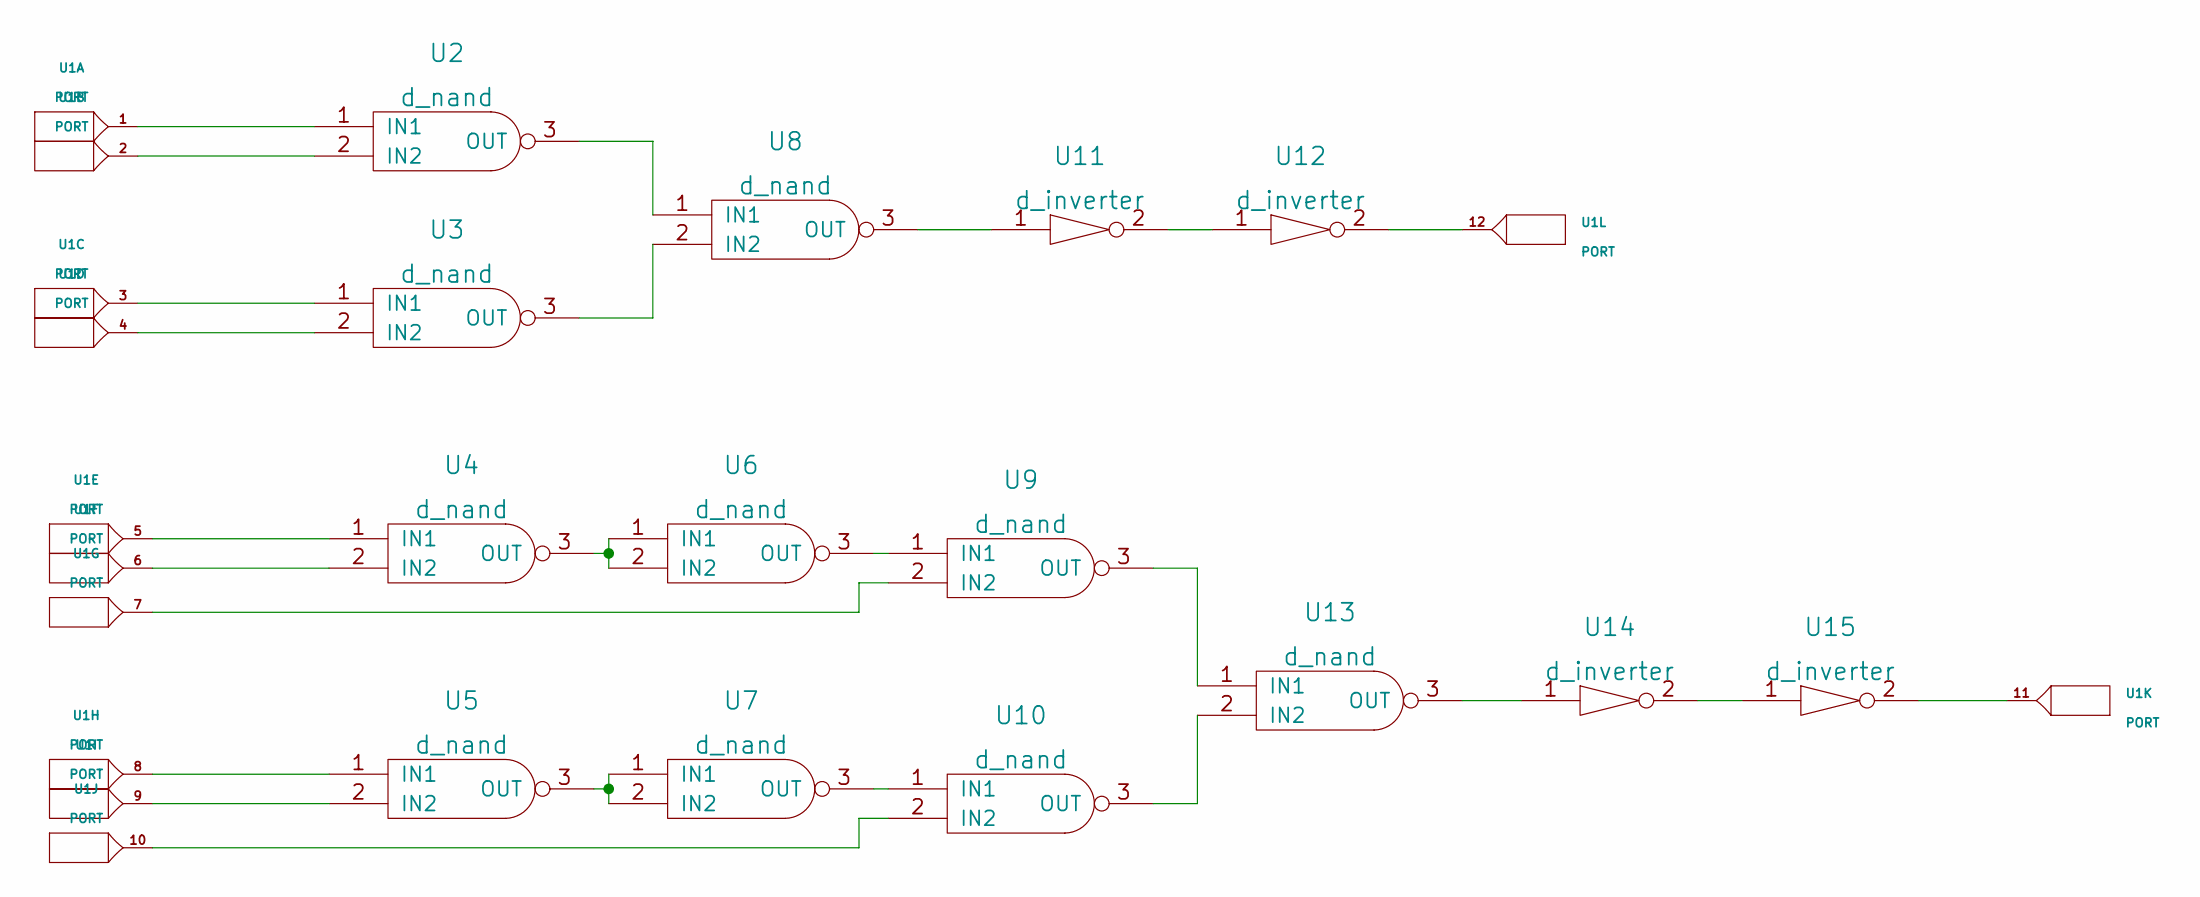
[picture p35: schematic IC_GD74HCT58.kicad_sch]

Parts:
U1: PORT
U2, U3, U4, U5, U6, U7, U8, U9, U10, U13: d_nand
U11, U12, U14, U15: d_inverter

Connections:
unnamed: U1.1, U2.1 (IN1)
unnamed: U1.2, U2.2 (IN2)
unnamed: U1.3, U3.1 (IN1)
unnamed: U1.4, U3.2 (IN2)
unnamed: U1.5, U4.1 (IN1)
unnamed: U1.6, U4.2 (IN2)
unnamed: U1.7, U9.2 (IN2)
unnamed: U1.8, U5.1 (IN1)
unnamed: U1.9, U5.2 (IN2)
unnamed: U1.10, U10.2 (IN2)
unnamed: U1.11, U15.2
unnamed: U1.12, U12.2
unnamed: U2.3 (OUT), U8.1 (IN1)
unnamed: U3.3 (OUT), U8.2 (IN2)
unnamed: U4.3 (OUT), U6.1 (IN1), U6.2 (IN2)
unnamed: U5.3 (OUT), U7.1 (IN1), U7.2 (IN2)
unnamed: U6.3 (OUT), U9.1 (IN1)
unnamed: U7.3 (OUT), U10.1 (IN1)
unnamed: U10.3 (OUT), U13.2 (IN2)
unnamed: U8.3 (OUT), U11.1
unnamed: U11.2, U12.1
unnamed: U9.3 (OUT), U13.1 (IN1)
unnamed: U13.3 (OUT), U14.1
unnamed: U14.2, U15.1
