FOSSEE/eSim/SUBCKT/IC_M74HC4024/IC_M74HC4024.kicad_sch

## KiCad design SUBCKT/IC_M74HC4024/IC_M74HC4024.kicad_sch (2026-06-08)

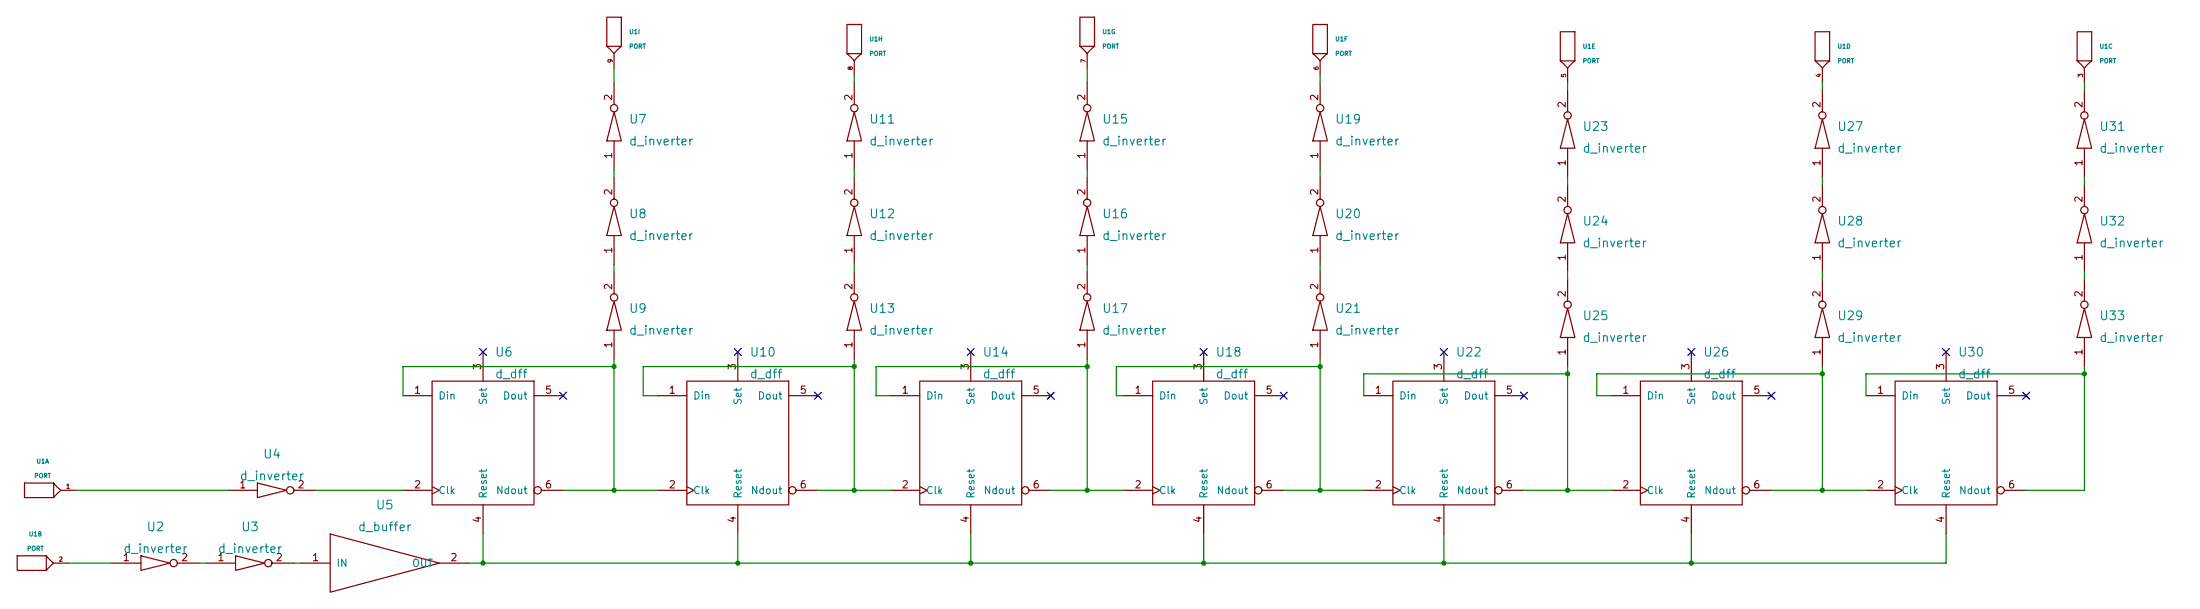
[picture p36: schematic IC_M74HC4024.kicad_sch]

Parts:
U1: PORT
U2, U3, U4, U7, U8, U9, U11, U12, U13, U15, U16, U17, U19, U20, U21, U23, U24, U25, U27, U28, U29, U31, U32, U33: d_inverter
U5: d_buffer
U6, U10, U14, U18, U22, U26, U30: d_dff

Connections:
unnamed: U1.1, U4.1
unnamed: U1.2, U2.1
unnamed: U1.3, U31.2
unnamed: U1.4, U27.2
unnamed: U1.5, U23.2
unnamed: U1.6, U19.2
unnamed: U1.7, U15.2
unnamed: U1.8, U11.2
unnamed: U1.9, U7.2
unnamed: U2.2, U3.1
unnamed: U3.2, U5.1 (IN)
unnamed: U4.2, U6.2 (Clk)
unnamed: U7.1, U8.2
unnamed: U8.1, U9.2
unnamed: U10.1 (Din), U10.6 (Ndout), U13.1, U14.2 (Clk)
unnamed: U6.1 (Din), U6.6 (Ndout), U9.1, U10.2 (Clk)
unnamed: U5.2 (OUT), U6.4 (Reset), U10.4 (Reset), U14.4 (Reset), U18.4 (Reset), U22.4 (Reset), U26.4 (Reset), U30.4 (Reset)
unnamed: U11.1, U12.2
unnamed: U12.1, U13.2
unnamed: U14.1 (Din), U14.6 (Ndout), U17.1, U18.2 (Clk)
unnamed: U15.1, U16.2
unnamed: U16.1, U17.2
unnamed: U18.1 (Din), U18.6 (Ndout), U21.1, U22.2 (Clk)
unnamed: U19.1, U20.2
unnamed: U20.1, U21.2
unnamed: U22.1 (Din), U22.6 (Ndout), U25.1, U26.2 (Clk)
unnamed: U23.1, U24.2
unnamed: U24.1, U25.2
unnamed: U26.1 (Din), U26.6 (Ndout), U29.1, U30.2 (Clk)
unnamed: U27.1, U28.2
unnamed: U28.1, U29.2
unnamed: U30.1 (Din), U30.6 (Ndout), U33.1
unnamed: U31.1, U32.2
unnamed: U32.1, U33.2
