FOSSEE/eSim/SUBCKT/IC_MC10E155/IC_MC10E155.kicad_sch

## KiCad design SUBCKT/IC_MC10E155/IC_MC10E155.kicad_sch (2026-06-08)

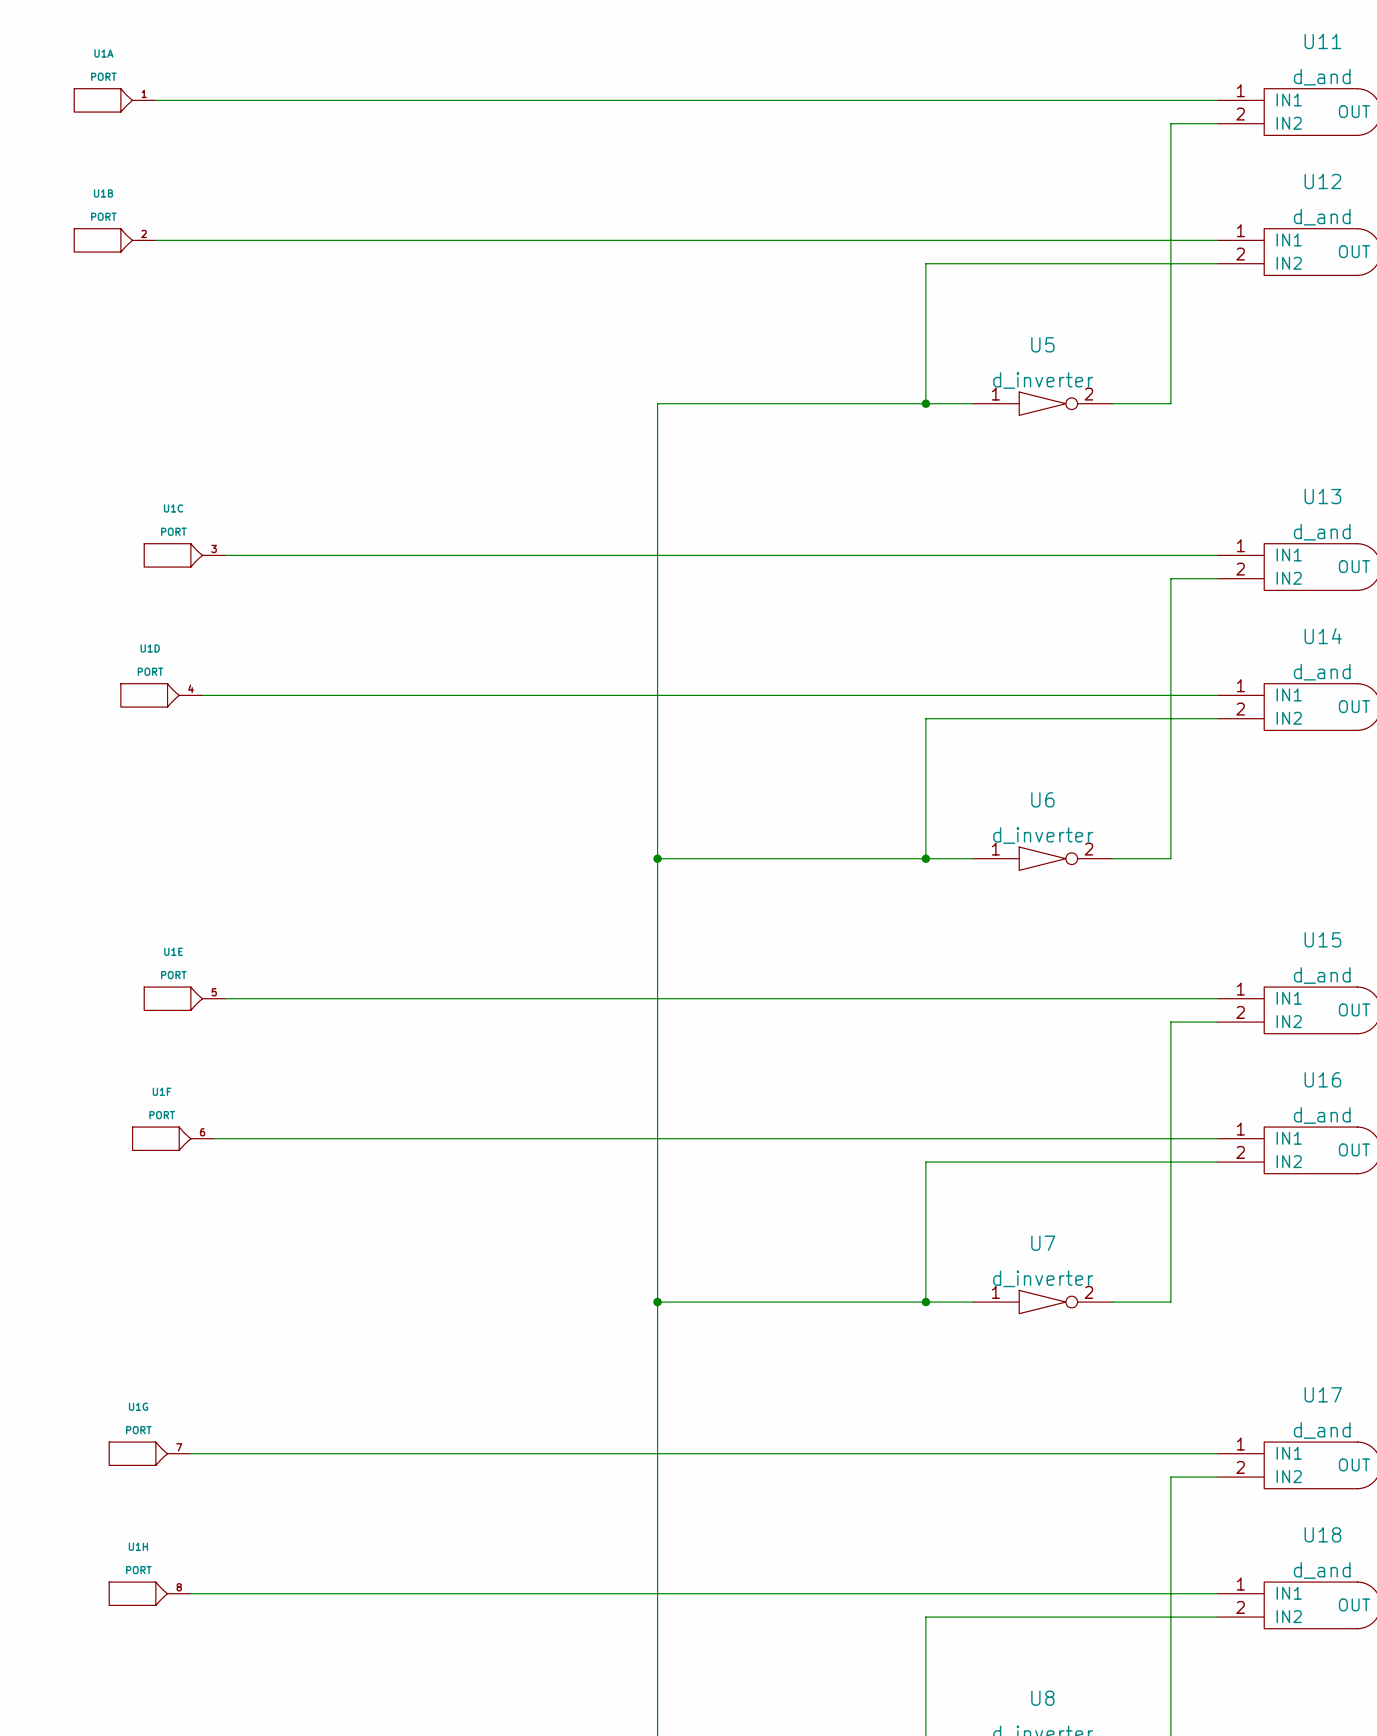
[picture p37: schematic IC_MC10E155.kicad_sch, part in row 1, column 1]

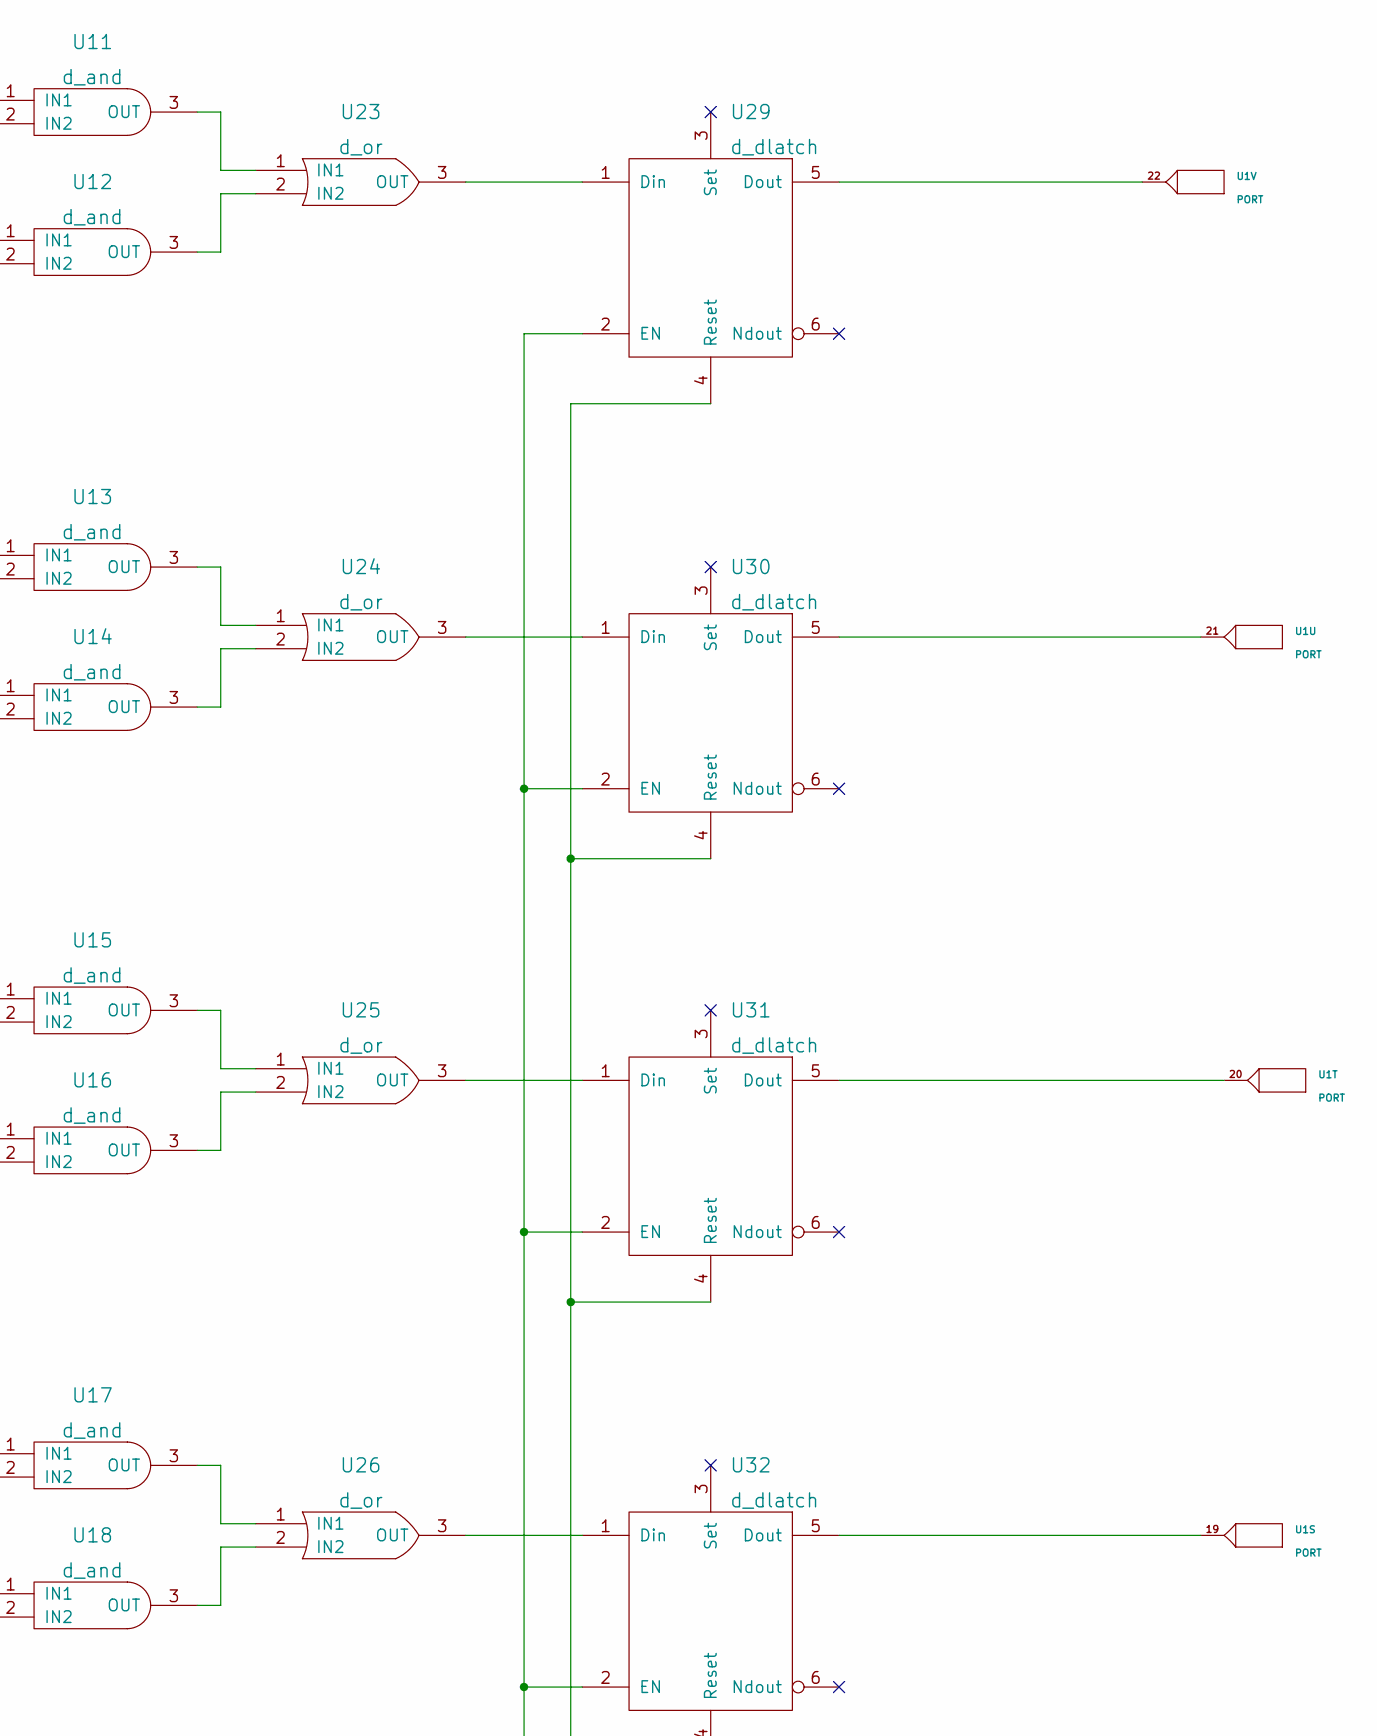
[picture p38: schematic IC_MC10E155.kicad_sch, part in row 1, column 2]

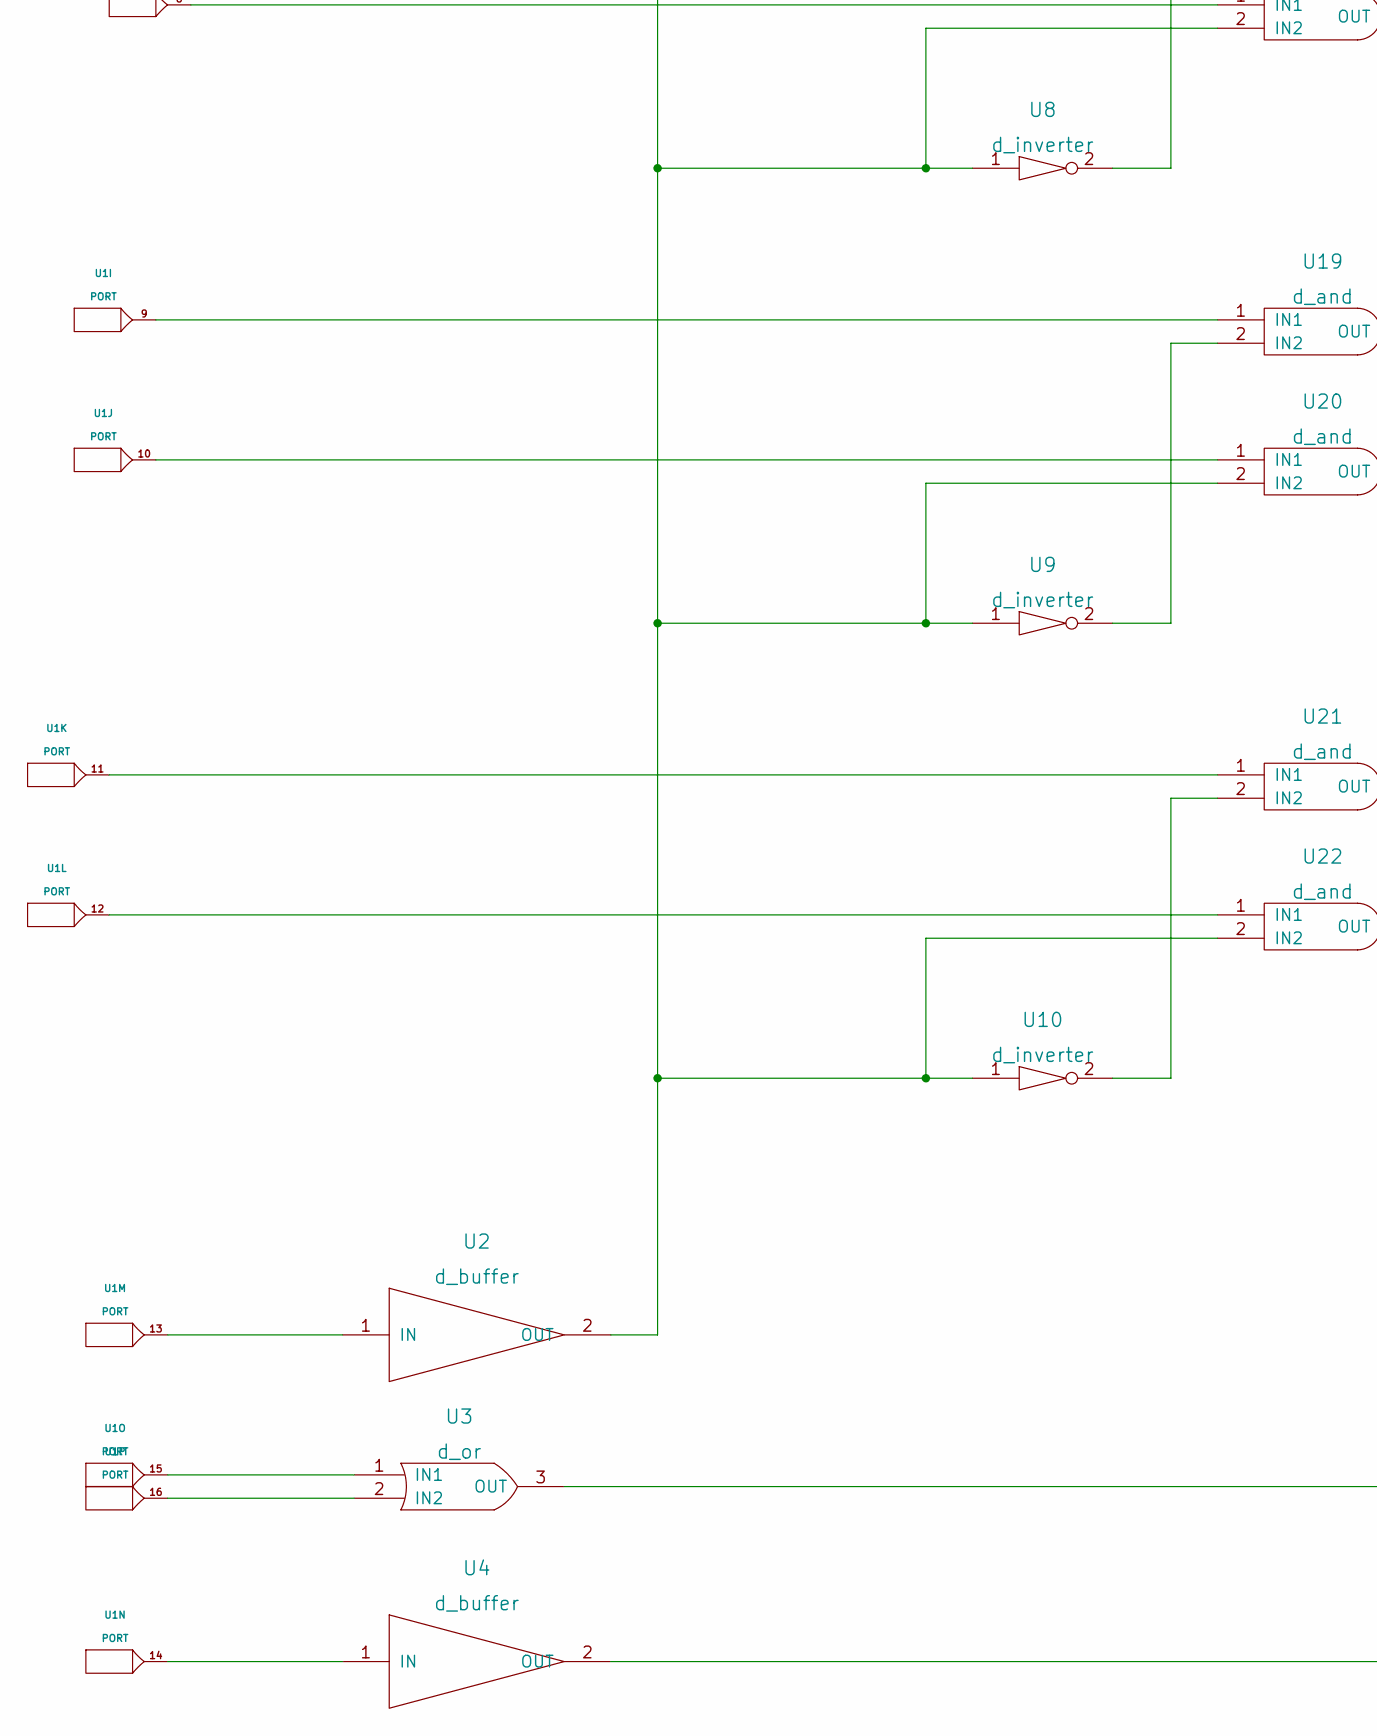
[picture p39: schematic IC_MC10E155.kicad_sch, part in row 2, column 1]

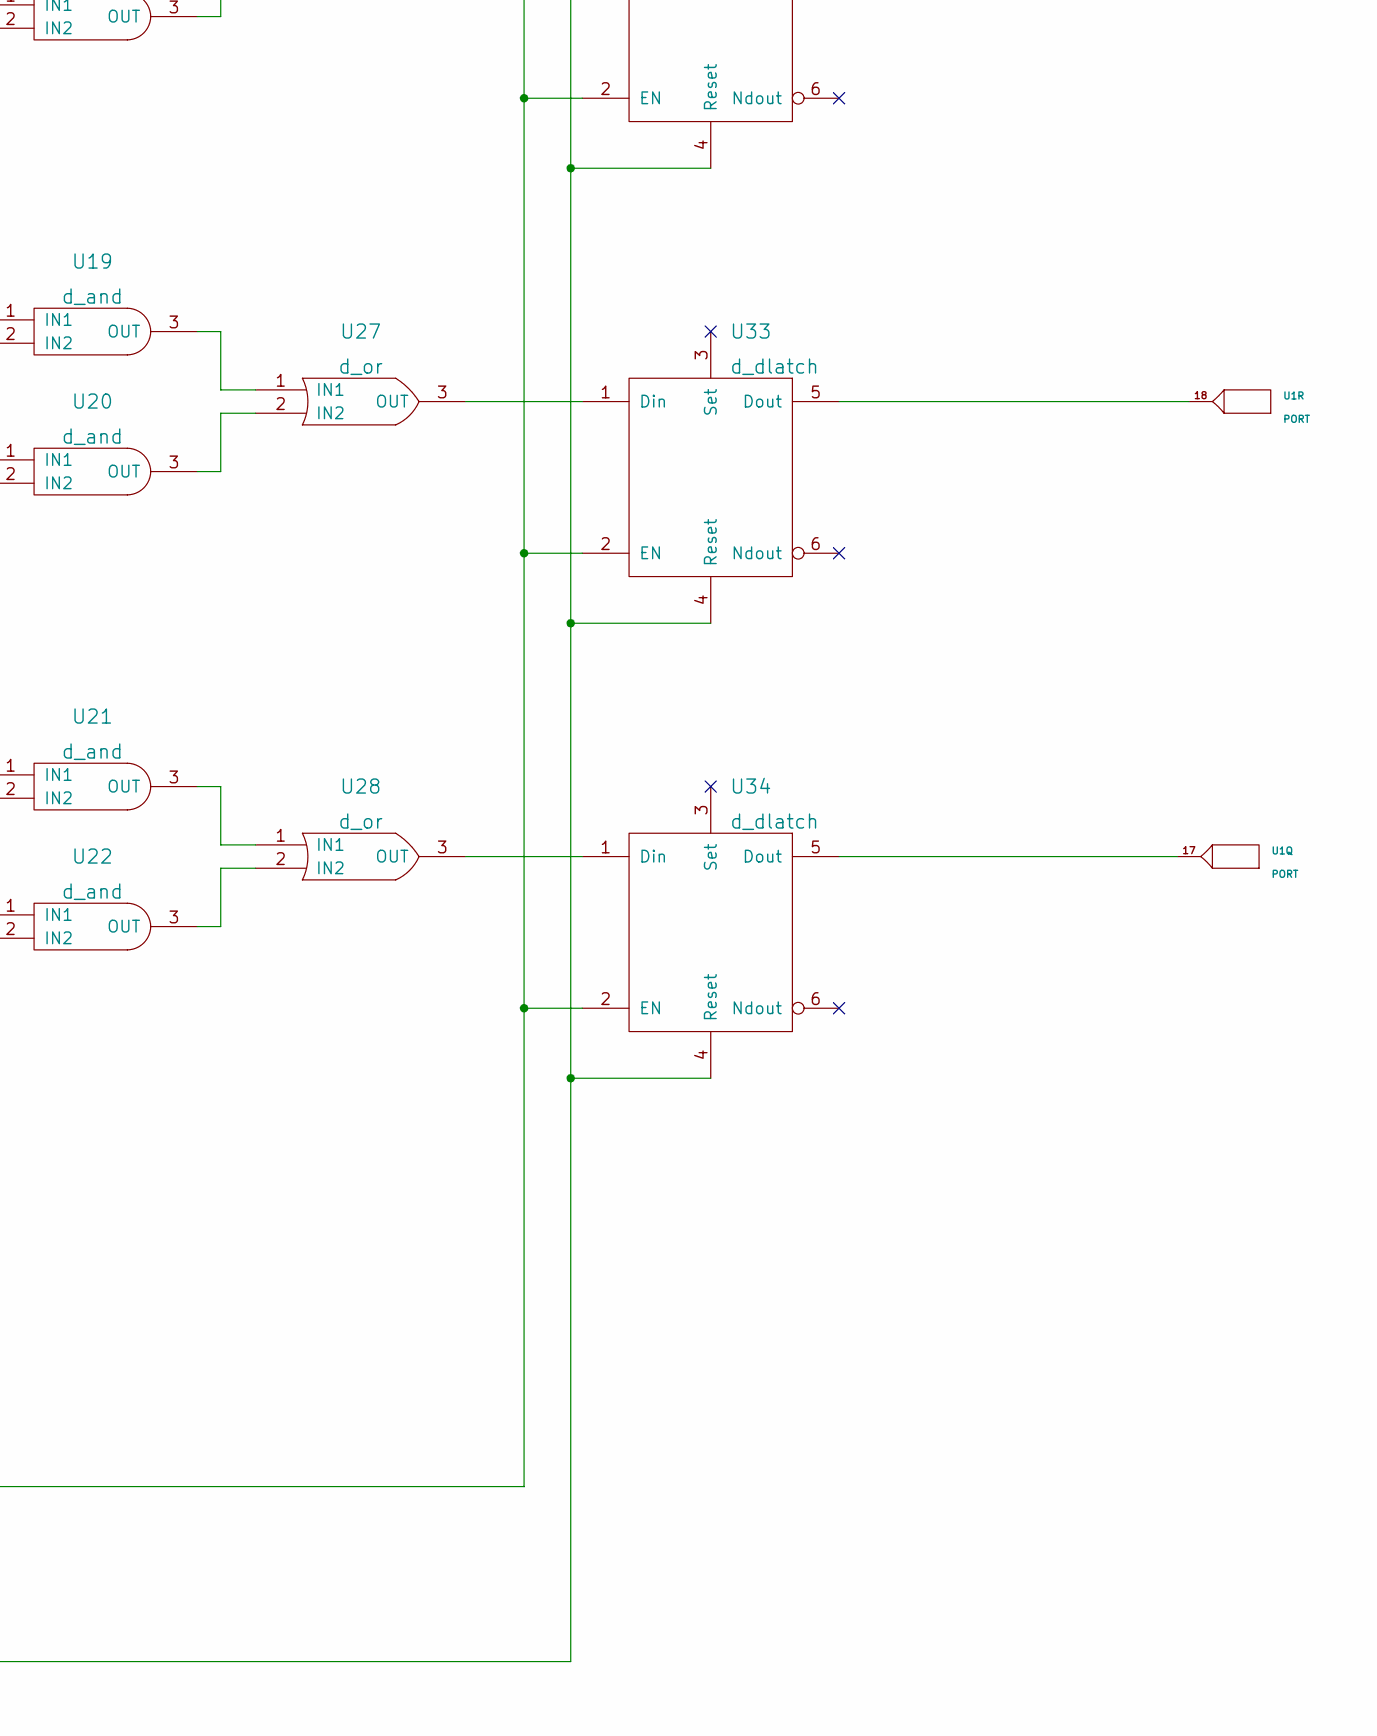
[picture p40: schematic IC_MC10E155.kicad_sch, part in row 2, column 2]

Parts:
U1: PORT
U2, U4: d_buffer
U3, U23, U24, U25, U26, U27, U28: d_or
U5, U6, U7, U8, U9, U10: d_inverter
U11, U12, U13, U14, U15, U16, U17, U18, U19, U20, U21, U22: d_and
U29, U30, U31, U32, U33, U34: d_dlatch

Connections:
unnamed: U1.1, U11.1 (IN1)
unnamed: U1.2, U12.1 (IN1)
unnamed: U1.3, U13.1 (IN1)
unnamed: U1.4, U14.1 (IN1)
unnamed: U1.5, U15.1 (IN1)
unnamed: U1.6, U16.1 (IN1)
unnamed: U1.7, U17.1 (IN1)
unnamed: U1.8, U18.1 (IN1)
unnamed: U1.9, U19.1 (IN1)
unnamed: U1.10, U20.1 (IN1)
unnamed: U1.11, U21.1 (IN1)
unnamed: U1.12, U22.1 (IN1)
unnamed: U1.13, U2.1 (IN)
unnamed: U1.14, U4.1 (IN)
unnamed: U1.15, U3.1 (IN1)
unnamed: U1.16, U3.2 (IN2)
unnamed: U1.17, U34.5 (Dout)
unnamed: U1.18, U33.5 (Dout)
unnamed: U1.19, U32.5 (Dout)
unnamed: U1.20, U31.5 (Dout)
unnamed: U1.21, U30.5 (Dout)
unnamed: U1.22, U29.5 (Dout)
unnamed: U2.2 (OUT), U5.1, U6.1, U7.1, U8.1, U9.1, U10.1, U12.2 (IN2), U14.2 (IN2), U16.2 (IN2), U18.2 (IN2), U20.2 (IN2), U22.2 (IN2)
unnamed: U10.2, U21.2 (IN2)
unnamed: U5.2, U11.2 (IN2)
unnamed: U11.3 (OUT), U23.1 (IN1)
unnamed: U12.3 (OUT), U23.2 (IN2)
unnamed: U6.2, U13.2 (IN2)
unnamed: U13.3 (OUT), U24.1 (IN1)
unnamed: U14.3 (OUT), U24.2 (IN2)
unnamed: U7.2, U15.2 (IN2)
unnamed: U15.3 (OUT), U25.1 (IN1)
unnamed: U16.3 (OUT), U25.2 (IN2)
unnamed: U8.2, U17.2 (IN2)
unnamed: U17.3 (OUT), U26.1 (IN1)
unnamed: U18.3 (OUT), U26.2 (IN2)
unnamed: U9.2, U19.2 (IN2)
unnamed: U19.3 (OUT), U27.1 (IN1)
unnamed: U20.3 (OUT), U27.2 (IN2)
unnamed: U21.3 (OUT), U28.1 (IN1)
unnamed: U22.3 (OUT), U28.2 (IN2)
unnamed: U23.3 (OUT), U29.1 (Din)
unnamed: U24.3 (OUT), U30.1 (Din)
unnamed: U25.3 (OUT), U31.1 (Din)
unnamed: U26.3 (OUT), U32.1 (Din)
unnamed: U27.3 (OUT), U33.1 (Din)
unnamed: U28.3 (OUT), U34.1 (Din)
unnamed: U3.3 (OUT), U29.2 (EN), U30.2 (EN), U31.2 (EN), U32.2 (EN), U33.2 (EN), U34.2 (EN)
unnamed: U4.2 (OUT), U29.4 (Reset), U30.4 (Reset), U31.4 (Reset), U32.4 (Reset), U33.4 (Reset), U34.4 (Reset)
