FOSSEE/eSim/SUBCKT/IC_MC10E156/3_and.sch

## KiCad design SUBCKT/IC_MC10E156/3_and.sch (2020-03-04)

Schematic: 3_and.sch

Parts:
U1: PORT
U2, U3: d_and

Notes on the sheet:
in1
in2
in3
out
