FOSSEE/eSim/SUBCKT/IC_MC10E156/4_OR.sch

## KiCad design SUBCKT/IC_MC10E156/4_OR.sch (2020-03-04)

Schematic: 4_OR.sch

Parts:
U1: PORT
U2, U3, U4: d_or

Notes on the sheet:
in1
in2
in3
in4
out
