FOSSEE/eSim/SUBCKT/IC_MC10E156/IC_MC10E156.kicad_sch

## KiCad design SUBCKT/IC_MC10E156/IC_MC10E156.kicad_sch (2026-06-08)

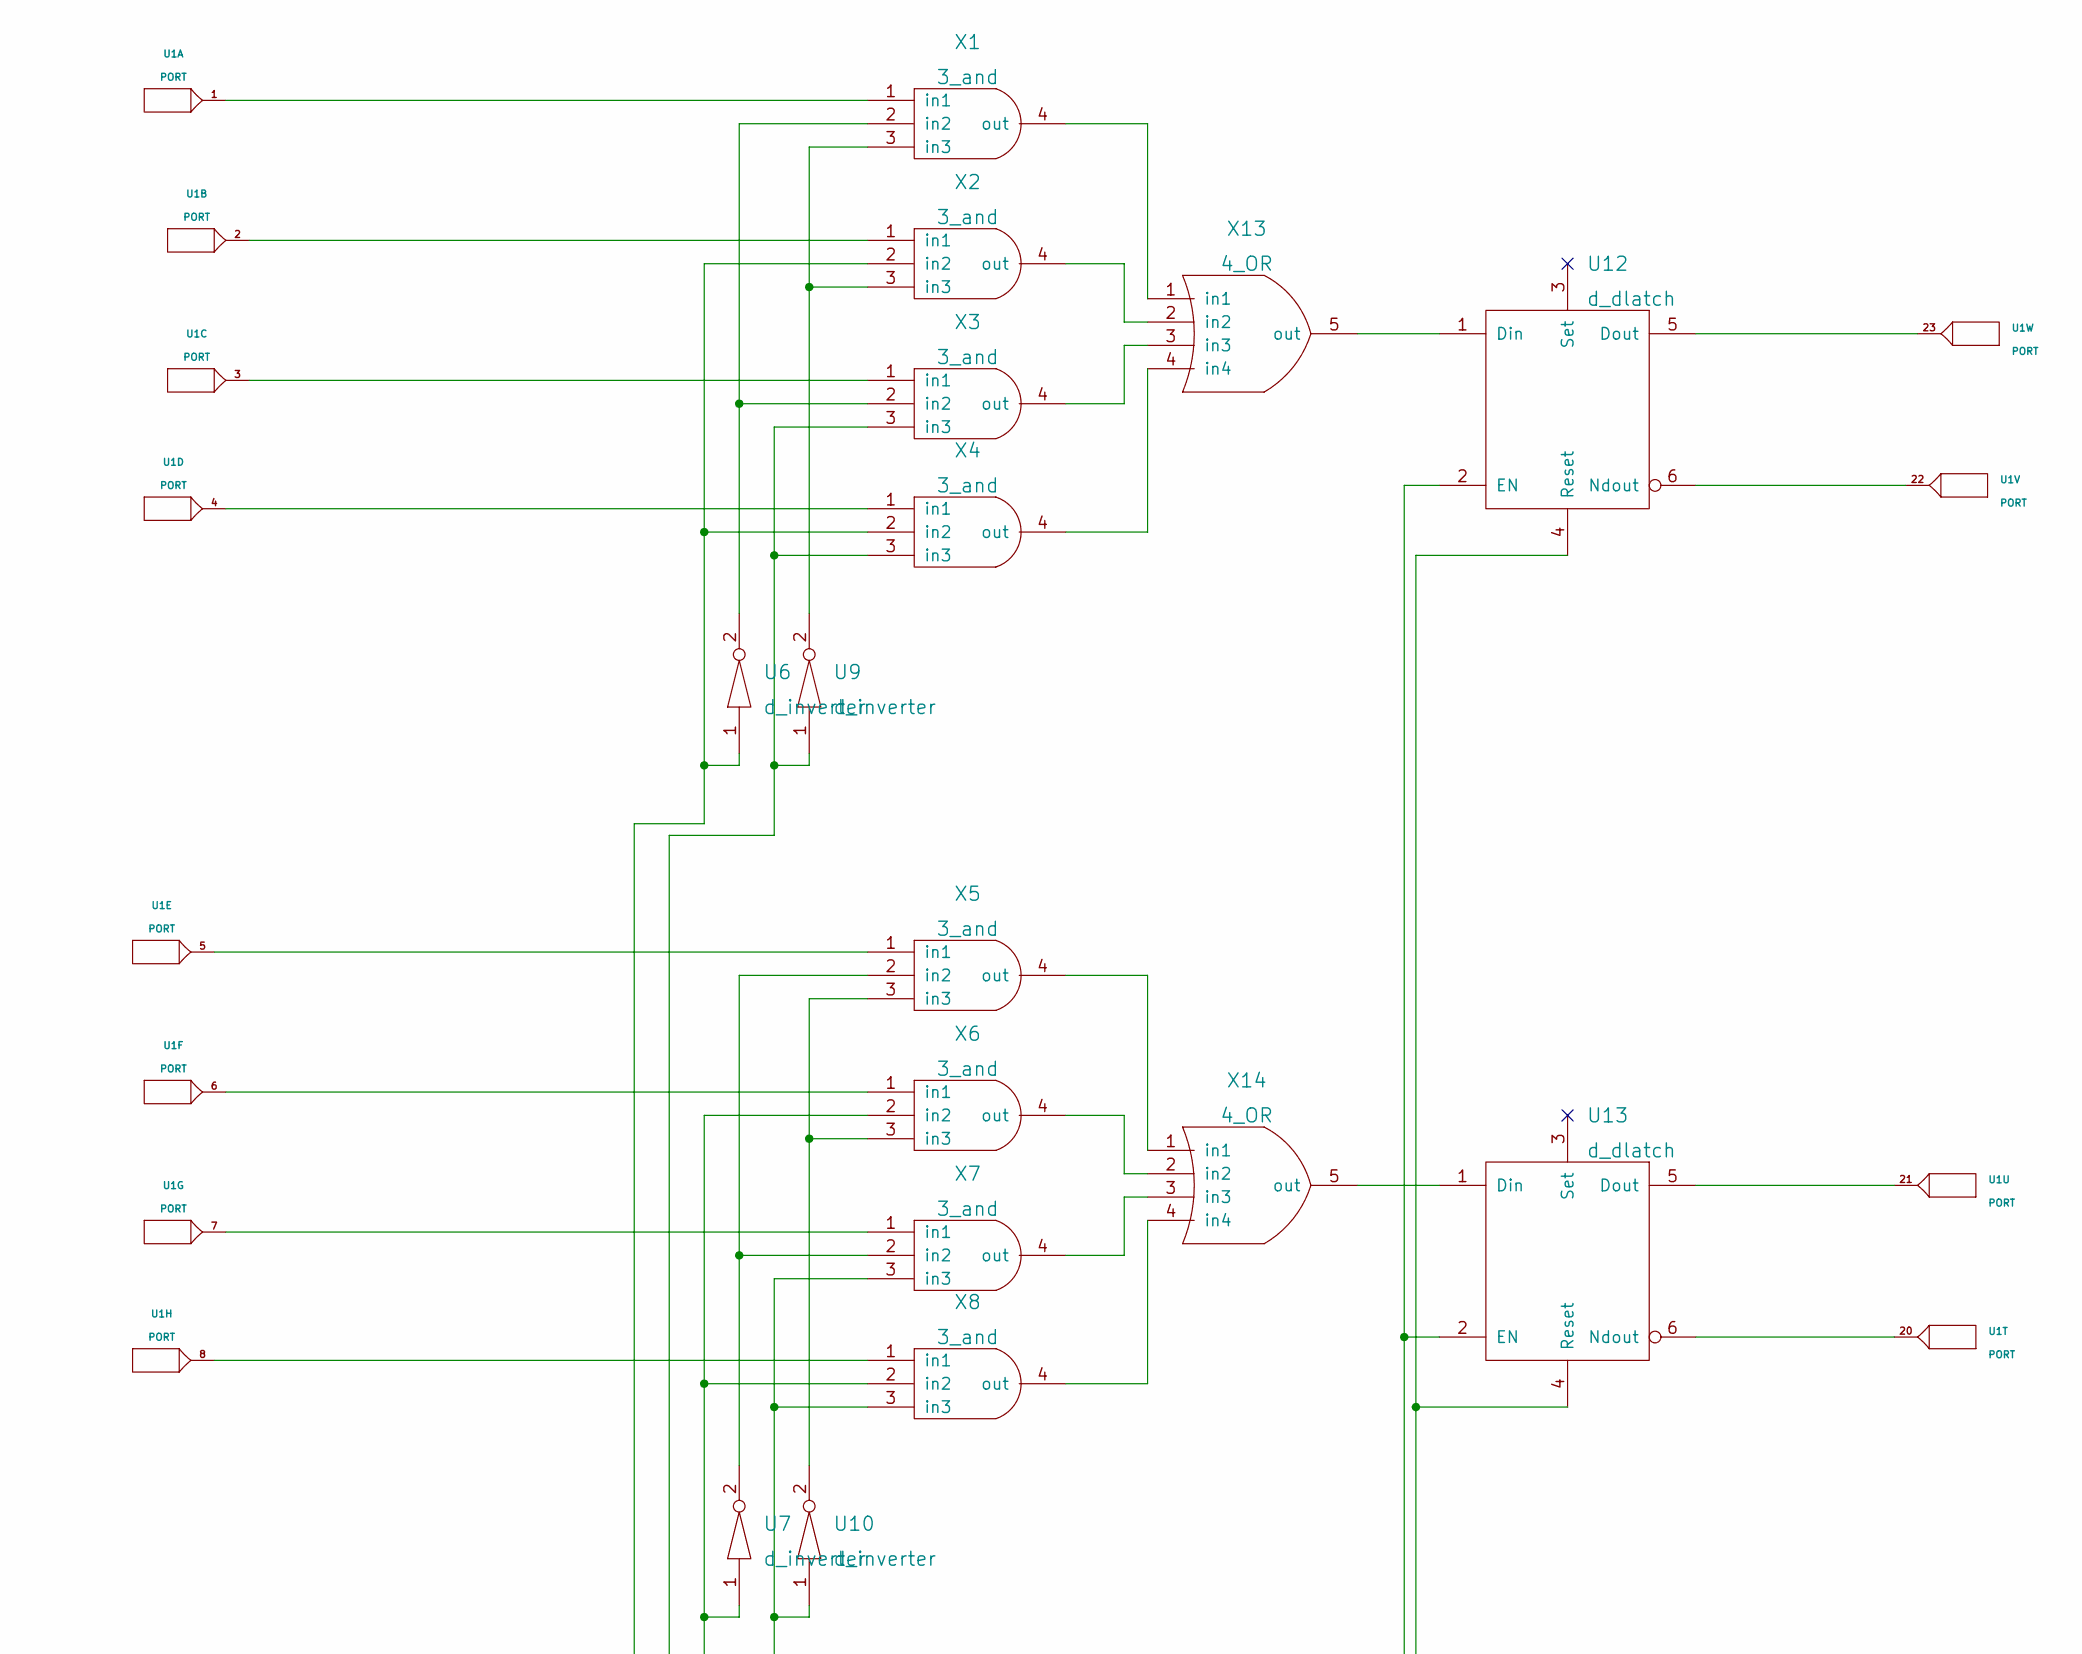
[picture p41: schematic IC_MC10E156.kicad_sch, part in row 1, column 1]

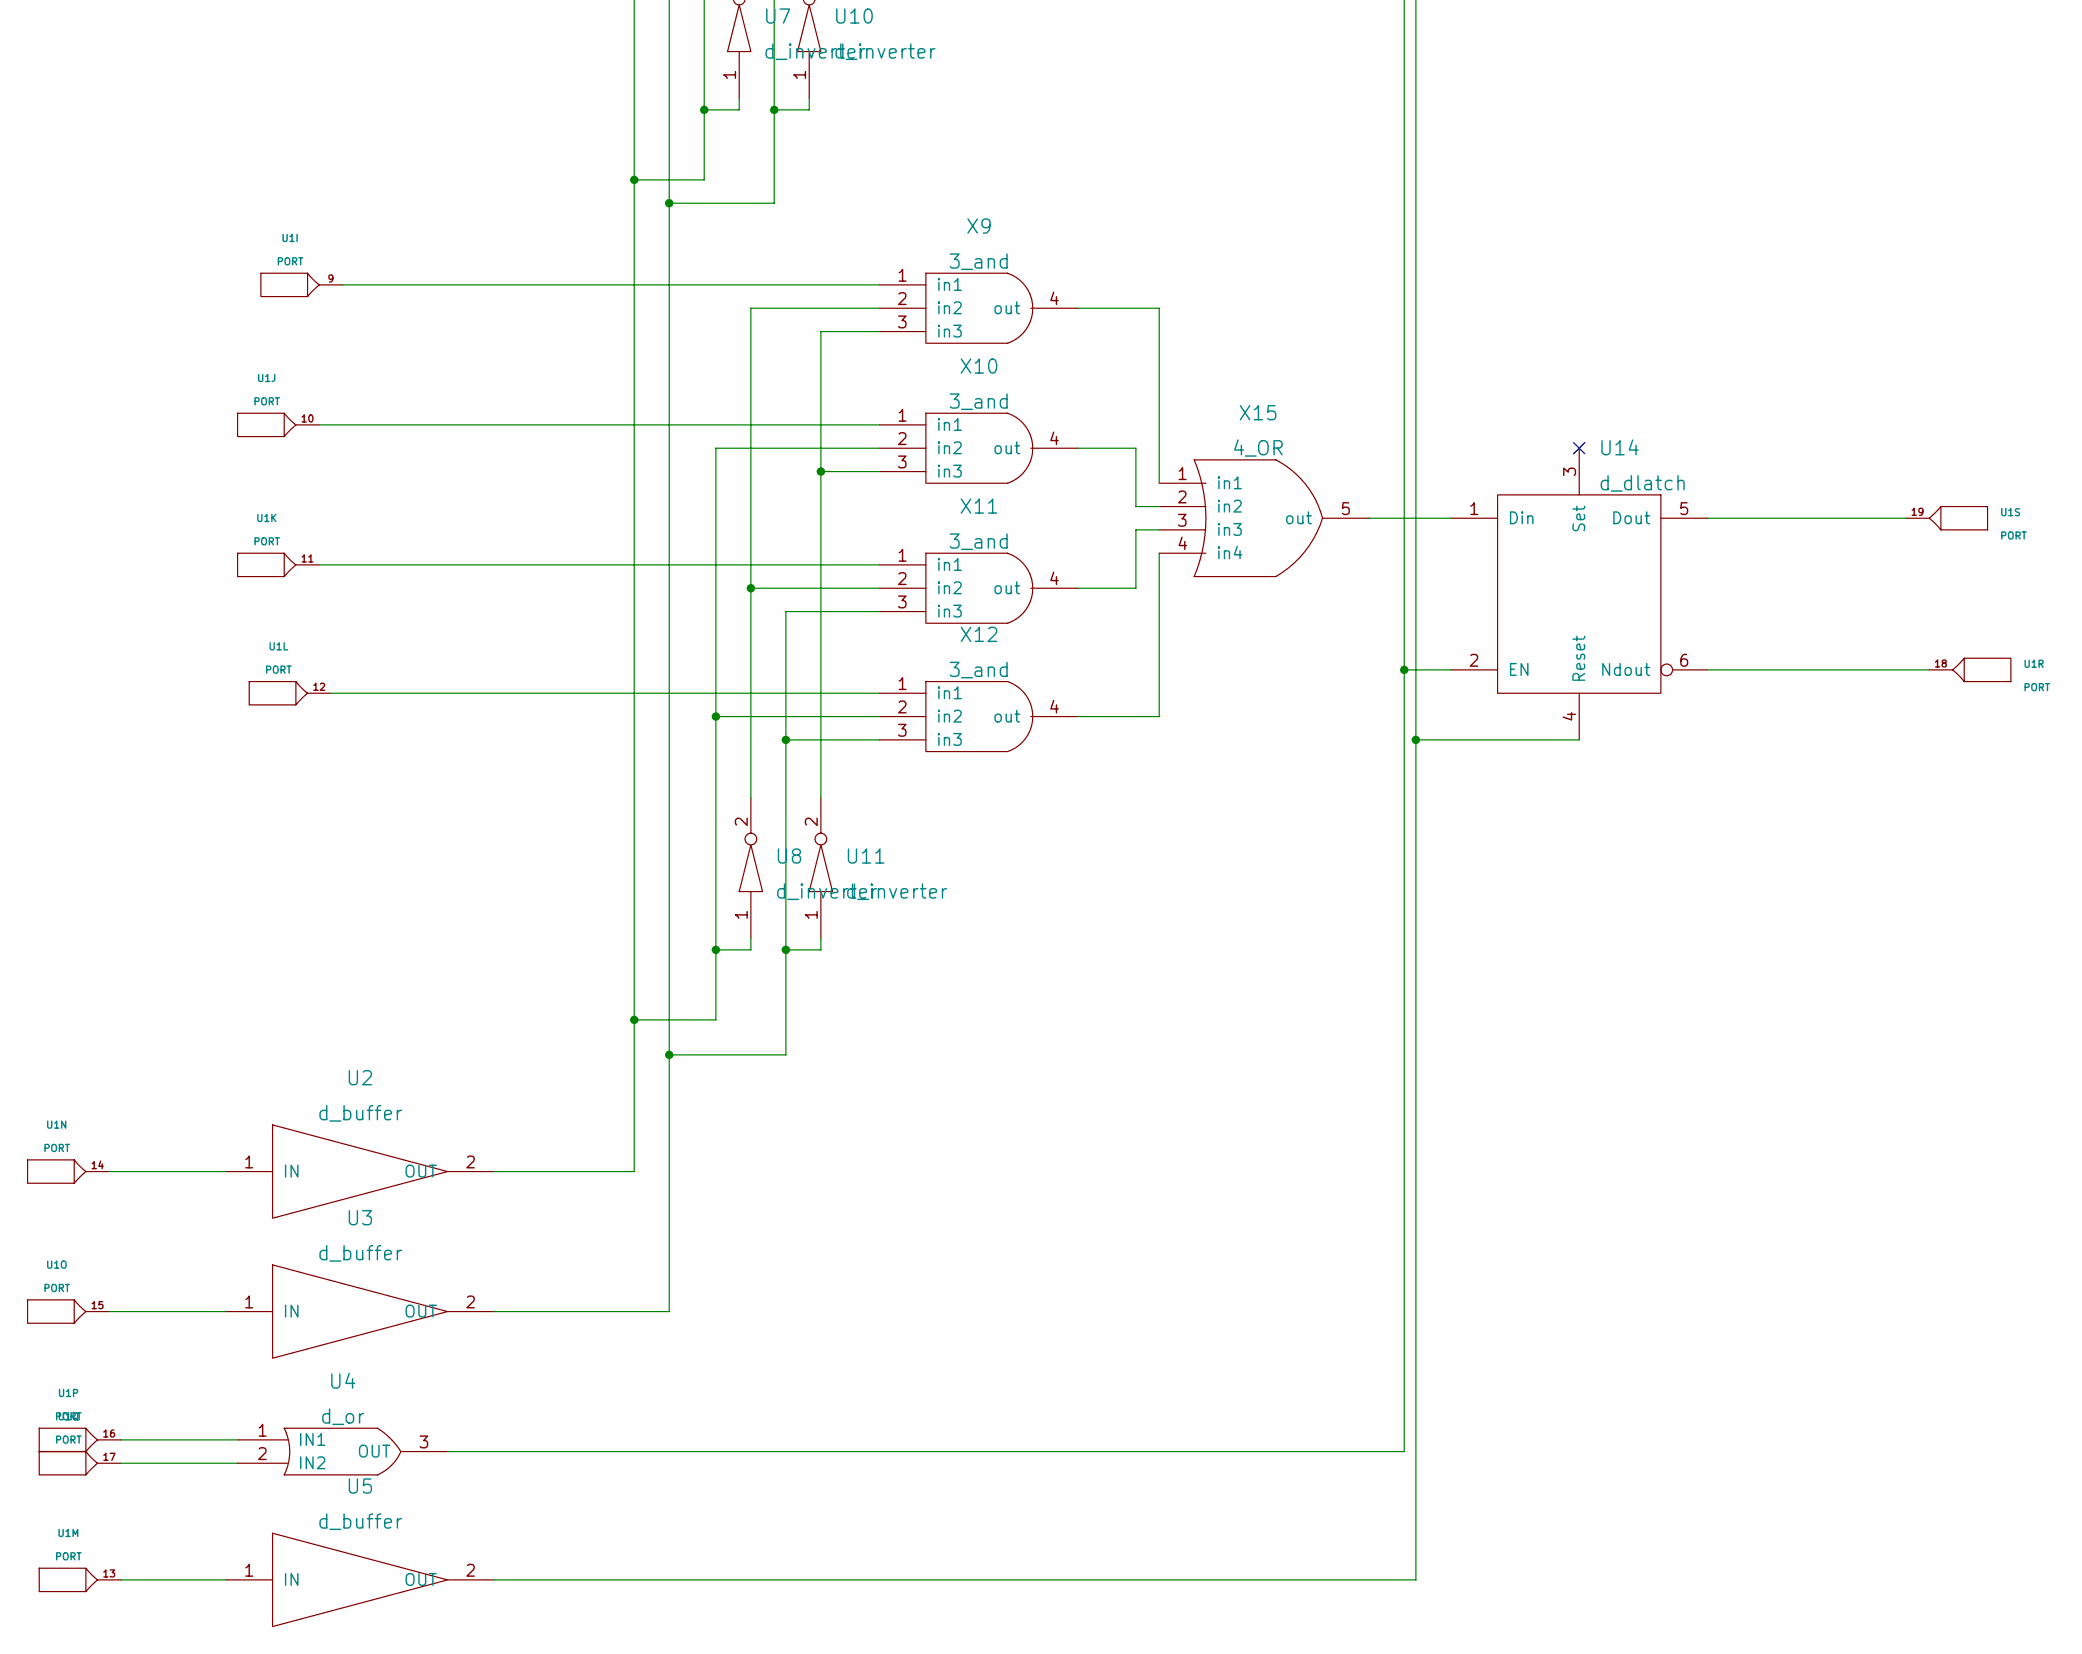
[picture p42: schematic IC_MC10E156.kicad_sch, part in row 2, column 1]

Parts:
U1: PORT
U2, U3, U5: d_buffer
U4: d_or
U6, U7, U8, U9, U10, U11: d_inverter
U12, U13, U14: d_dlatch
X1, X2, X3, X4, X5, X6, X7, X8, X9, X10, X11, X12: 3_and
X13, X14, X15: 4_OR

Connections:
unnamed: U1.1, X1.1 (in1)
unnamed: U1.2, X2.1 (in1)
unnamed: U1.3, X3.1 (in1)
unnamed: U1.4, X4.1 (in1)
unnamed: U1.5, X5.1 (in1)
unnamed: U1.6, X6.1 (in1)
unnamed: U1.7, X7.1 (in1)
unnamed: U1.8, X8.1 (in1)
unnamed: U1.9, X9.1 (in1)
unnamed: U1.10, X10.1 (in1)
unnamed: U1.11, X11.1 (in1)
unnamed: U1.12, X12.1 (in1)
unnamed: U1.13, U5.1 (IN)
unnamed: U1.14, U2.1 (IN)
unnamed: U1.15, U3.1 (IN)
unnamed: U1.16, U4.1 (IN1)
unnamed: U1.17, U4.2 (IN2)
unnamed: U1.18, U14.6 (Ndout)
unnamed: U1.19, U14.5 (Dout)
unnamed: U1.20, U13.6 (Ndout)
unnamed: U1.21, U13.5 (Dout)
unnamed: U1.22, U12.6 (Ndout)
unnamed: U1.23, U12.5 (Dout)
unnamed: U2.2 (OUT), U6.1, U7.1, U8.1, X2.2 (in2), X4.2 (in2), X6.2 (in2), X8.2 (in2), X10.2 (in2), X12.2 (in2)
unnamed: U6.2, X1.2 (in2), X3.2 (in2)
unnamed: U7.2, X5.2 (in2), X7.2 (in2)
unnamed: U8.2, X9.2 (in2), X11.2 (in2)
unnamed: U9.2, X1.3 (in3), X2.3 (in3)
unnamed: U3.2 (OUT), U9.1, U10.1, U11.1, X3.3 (in3), X4.3 (in3), X7.3 (in3), X8.3 (in3), X11.3 (in3), X12.3 (in3)
unnamed: U10.2, X5.3 (in3), X6.3 (in3)
unnamed: U11.2, X9.3 (in3), X10.3 (in3)
unnamed: U12.1 (Din), X13.5 (out)
unnamed: U4.3 (OUT), U12.2 (EN), U13.2 (EN), U14.2 (EN)
unnamed: U5.2 (OUT), U12.4 (Reset), U13.4 (Reset), U14.4 (Reset)
unnamed: U13.1 (Din), X14.5 (out)
unnamed: U14.1 (Din), X15.5 (out)
unnamed: X1.4 (out), X13.1 (in1)
unnamed: X10.4 (out), X15.2 (in2)
unnamed: X11.4 (out), X15.3 (in3)
unnamed: X12.4 (out), X15.4 (in4)
unnamed: X2.4 (out), X13.2 (in2)
unnamed: X3.4 (out), X13.3 (in3)
unnamed: X4.4 (out), X13.4 (in4)
unnamed: X5.4 (out), X14.1 (in1)
unnamed: X6.4 (out), X14.2 (in2)
unnamed: X7.4 (out), X14.3 (in3)
unnamed: X8.4 (out), X14.4 (in4)
unnamed: X9.4 (out), X15.1 (in1)
