FOSSEE/eSim/SUBCKT/IC_NA53/IC_NA53.kicad_sch

## KiCad design SUBCKT/IC_NA53/IC_NA53.kicad_sch (2026-06-08)

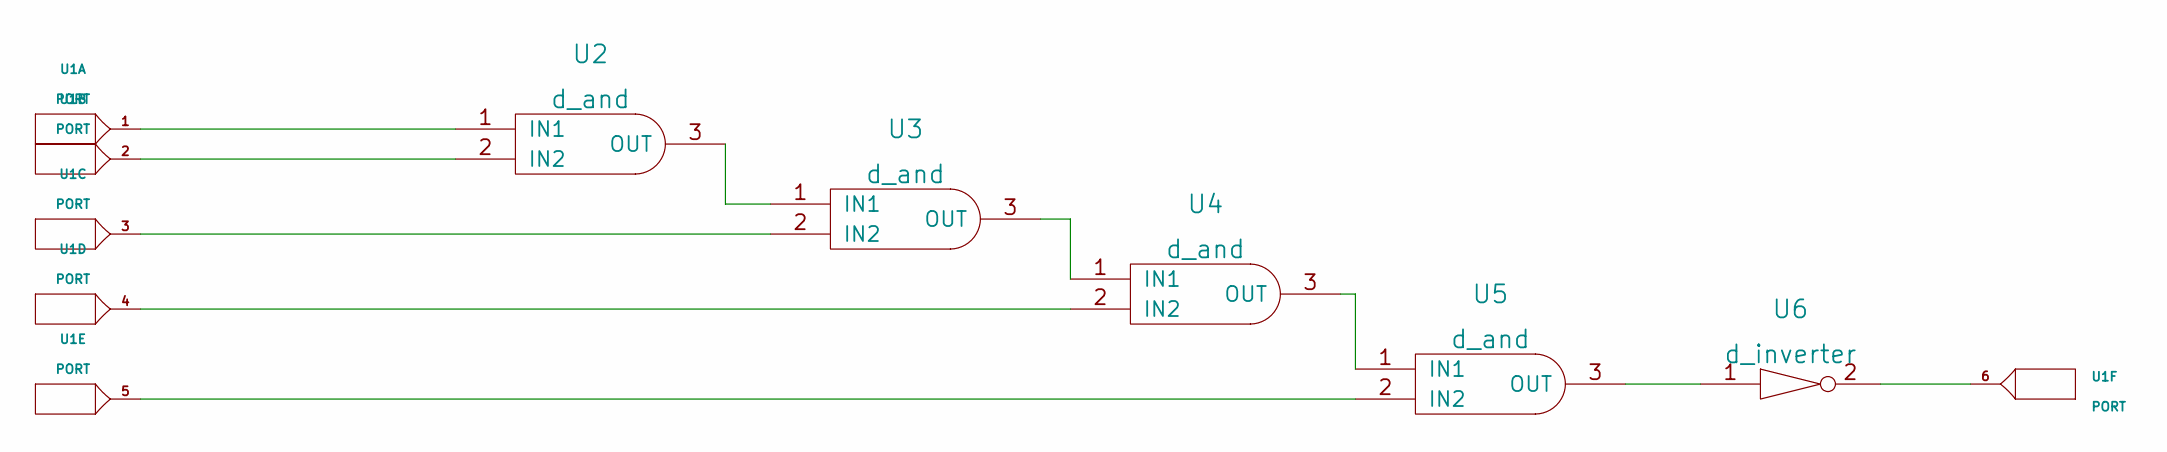
[picture p43: schematic IC_NA53.kicad_sch]

Parts:
U1: PORT
U2, U3, U4, U5: d_and
U6: d_inverter

Connections:
unnamed: U1.1, U2.1 (IN1)
unnamed: U1.2, U2.2 (IN2)
unnamed: U1.3, U3.2 (IN2)
unnamed: U1.4, U4.2 (IN2)
unnamed: U1.5, U5.2 (IN2)
unnamed: U1.6, U6.2
unnamed: U2.3 (OUT), U3.1 (IN1)
unnamed: U3.3 (OUT), U4.1 (IN1)
unnamed: U4.3 (OUT), U5.1 (IN1)
unnamed: U5.3 (OUT), U6.1
