FOSSEE/eSim/SUBCKT/IC_OR73/IC_OR73.kicad_sch

## KiCad design SUBCKT/IC_OR73/IC_OR73.kicad_sch (2026-06-08)

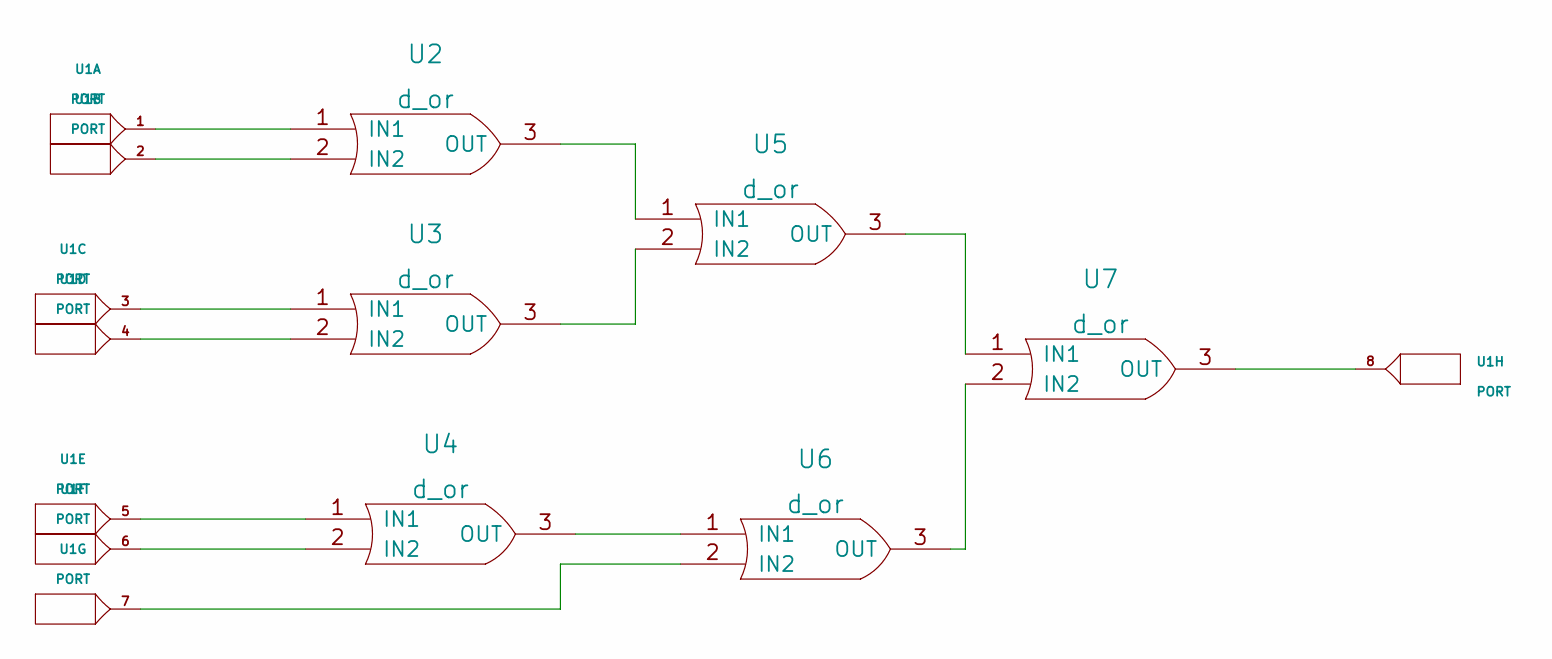
[picture p44: schematic IC_OR73.kicad_sch]

Parts:
U1: PORT
U2, U3, U4, U5, U6, U7: d_or

Connections:
unnamed: U1.1, U2.1 (IN1)
unnamed: U1.2, U2.2 (IN2)
unnamed: U1.3, U3.1 (IN1)
unnamed: U1.4, U3.2 (IN2)
unnamed: U1.5, U4.1 (IN1)
unnamed: U1.6, U4.2 (IN2)
unnamed: U1.7, U6.2 (IN2)
unnamed: U1.8, U7.3 (OUT)
unnamed: U2.3 (OUT), U5.1 (IN1)
unnamed: U3.3 (OUT), U5.2 (IN2)
unnamed: U4.3 (OUT), U6.1 (IN1)
unnamed: U5.3 (OUT), U7.1 (IN1)
unnamed: U6.3 (OUT), U7.2 (IN2)
