FOSSEE/eSim/Examples/Analysis_Of_Digital_IC/3_Input_NAND_Characteristics/3_Input_NAND_Characteristics.sch

## KiCad design Examples/Analysis_Of_Digital_IC/3_Input_NAND_Characteristics/3_Input_NAND_Characteristics.sch (2020-03-18)

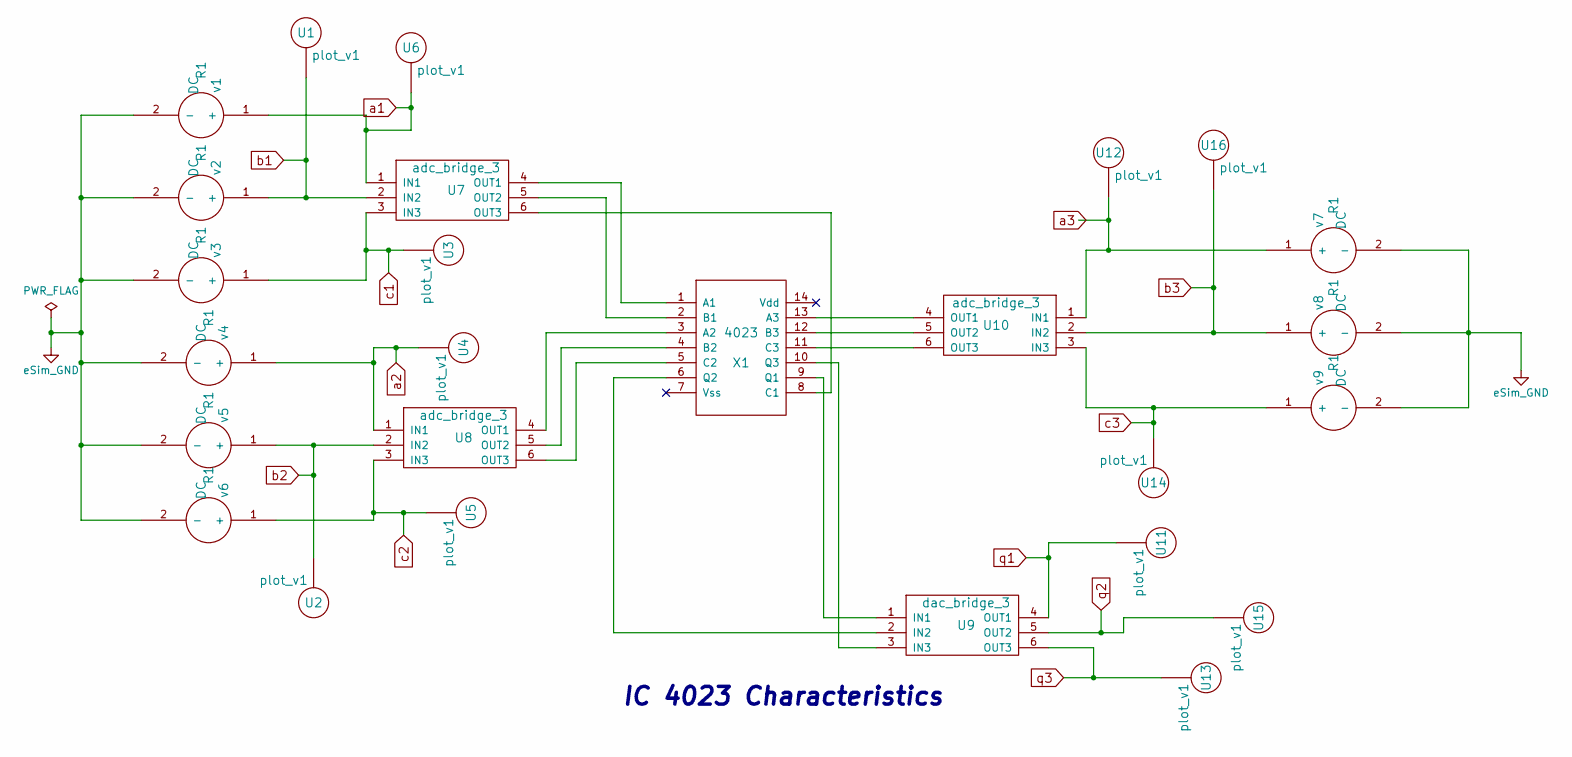
[picture p45: schematic 3_Input_NAND_Characteristics.sch]

Parts:
U1, U2, U3, U4, U5, U6, U11, U12, U13, U14, U15, U16: plot_v1
U7, U8, U10: adc_bridge_3
U9: dac_bridge_3
X1: 4023
v1, v2, v3, v4, v5, v6, v7, v8, v9: DC; R1

Connections:
unnamed: U7.4 (OUT1), X1.1 (A1)
unnamed: U7.5 (OUT2), X1.2 (B1)
unnamed: U7.6 (OUT3), X1.8 (C1)
unnamed: U8.4 (OUT1), X1.3 (A2)
unnamed: U8.5 (OUT2), X1.4 (B2)
unnamed: U8.6 (OUT3), X1.5 (C2)
unnamed: U9.1 (IN1), X1.9 (Q1)
unnamed: U9.2 (IN2), X1.6 (Q2)
unnamed: U9.3 (IN3), X1.10 (Q3)
unnamed: U10.4 (OUT1), X1.13 (A3)
unnamed: U10.5 (OUT2), X1.12 (B3)
unnamed: U10.6 (OUT3), X1.11 (C3)
a1: U6.~, U7.1 (IN1), v1.1 (+)
a2: U4.~, U8.1 (IN1), v4.1 (+)
a3: U10.1 (IN1), U12.~, v7.1 (+)
b1: U1.~, U7.2 (IN2), v2.1 (+)
b2: U2.~, U8.2 (IN2), v5.1 (+)
b3: U10.2 (IN2), U16.~, v8.1 (+)
c1: U3.~, U7.3 (IN3), v3.1 (+)
c2: U5.~, U8.3 (IN3), v6.1 (+)
c3: U10.3 (IN3), U14.~, v9.1 (+)
eSim_GND: v1.2 (-), v2.2 (-), v3.2 (-), v4.2 (-), v5.2 (-), v6.2 (-), v7.2 (-), v8.2 (-), v9.2 (-)
q1: U9.4 (OUT1), U11.~
q2: U9.5 (OUT2), U15.~
q3: U9.6 (OUT3), U13.~

Notes on the sheet:
IC 4023 Characteristics
