FOSSEE/eSim/Examples/Analysis_Of_Digital_IC/3_Input_NAND_Characteristics/4023.sch

## KiCad design Examples/Analysis_Of_Digital_IC/3_Input_NAND_Characteristics/4023.sch (2020-03-04)

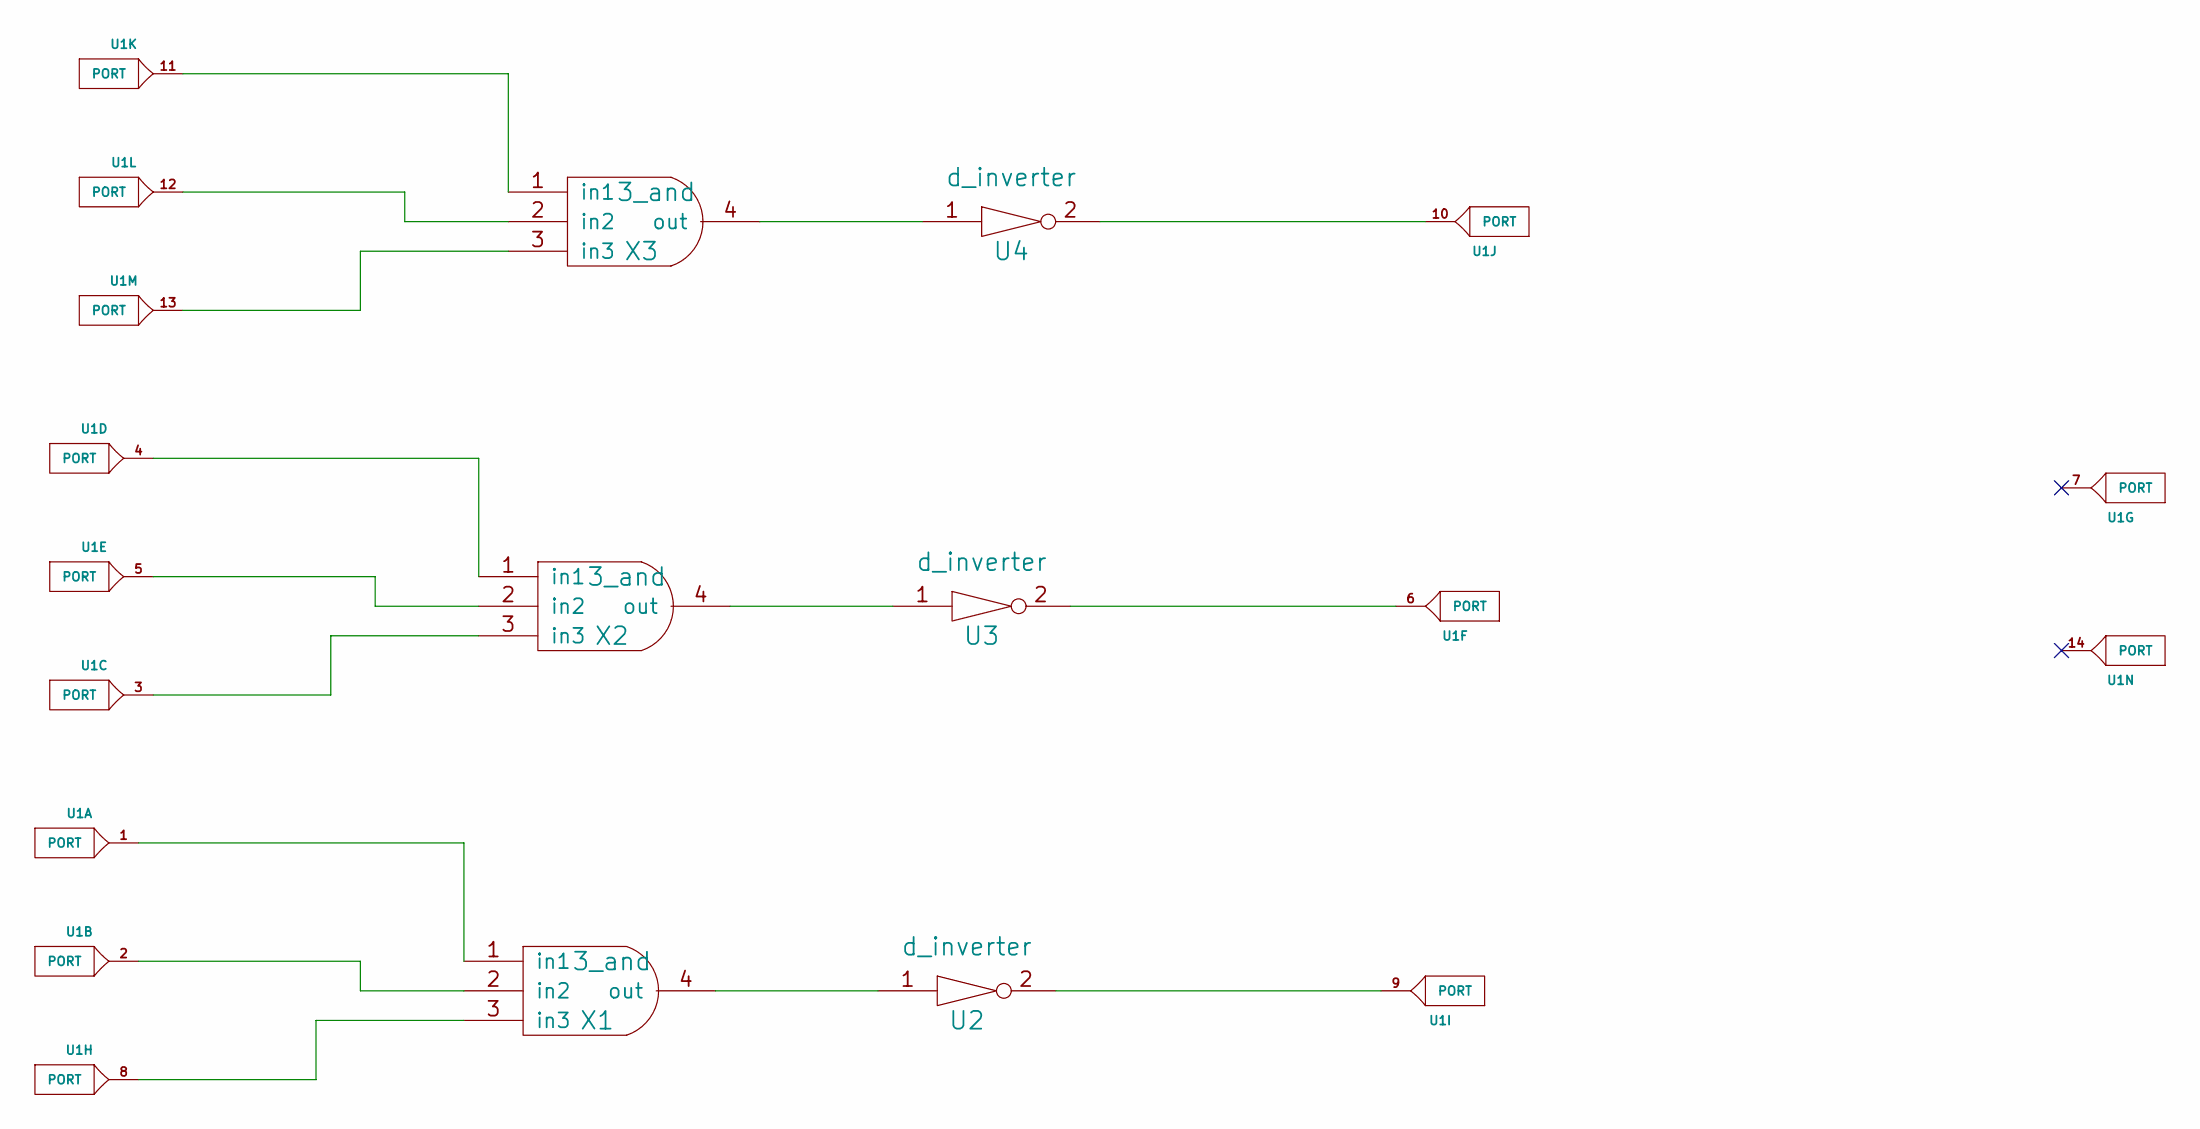
[picture p46: schematic 4023.sch]

Parts:
U1: PORT
U2, U3, U4: d_inverter
X1, X2, X3: 3_and

Connections:
unnamed: U1.1, X1.1 (in1)
unnamed: U1.2, X1.2 (in2)
unnamed: U1.3, X2.3 (in3)
unnamed: U1.4, X2.1 (in1)
unnamed: U1.5, X2.2 (in2)
unnamed: U1.6, U3.2
unnamed: U1.8, X1.3 (in3)
unnamed: U1.9, U2.2
unnamed: U1.10, U4.2
unnamed: U1.11, X3.1 (in1)
unnamed: U1.12, X3.2 (in2)
unnamed: U1.13, X3.3 (in3)
unnamed: U2.1, X1.4 (out)
unnamed: U3.1, X2.4 (out)
unnamed: U4.1, X3.4 (out)
