FOSSEE/eSim/Examples/Analysis_Of_Digital_IC/4_Input_NAND_Charcateristics/4_Input_NAND_Charcateristics.sch

## KiCad design Examples/Analysis_Of_Digital_IC/4_Input_NAND_Charcateristics/4_Input_NAND_Charcateristics.sch (2020-03-18)

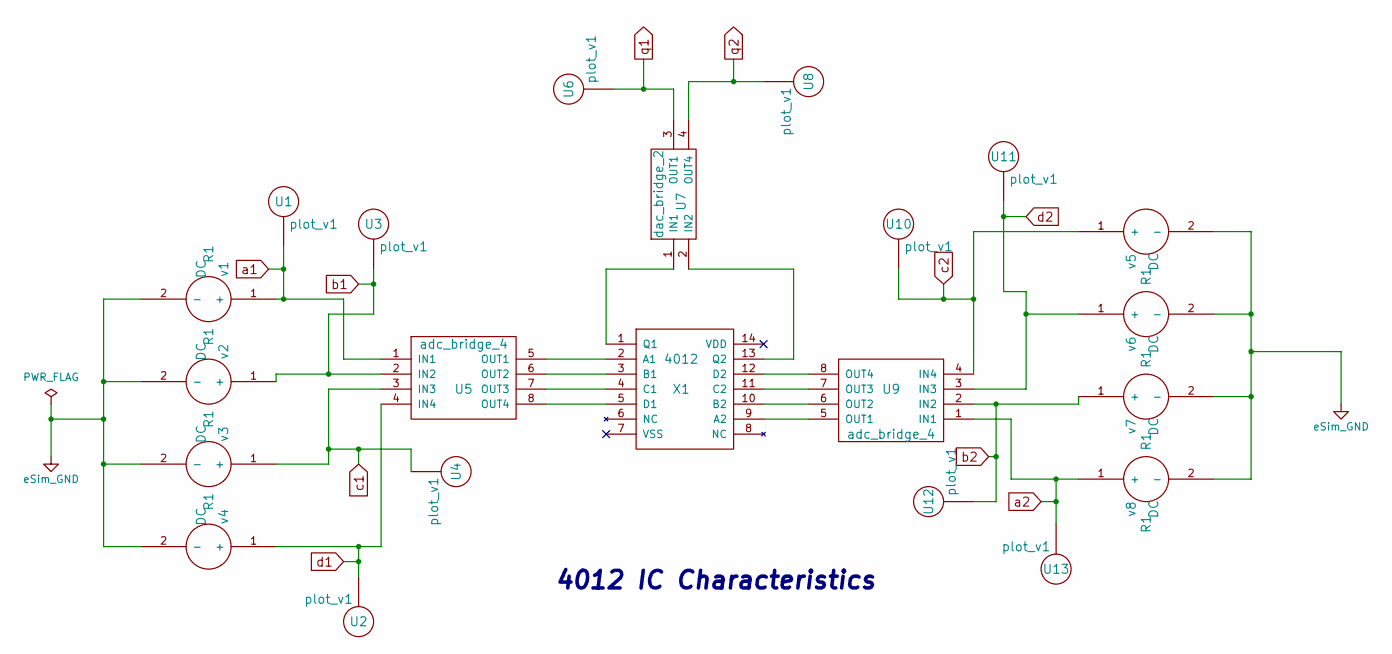
[picture p47: schematic 4_Input_NAND_Charcateristics.sch]

Parts:
U1, U2, U3, U4, U6, U8, U10, U11, U12, U13: plot_v1
U5, U9: adc_bridge_4
U7: dac_bridge_2
X1: 4012
v1, v2, v3, v4, v5, v6, v7, v8: DC; R1

Connections:
unnamed: U5.5 (OUT1), X1.2 (A1)
unnamed: U5.6 (OUT2), X1.3 (B1)
unnamed: U5.7 (OUT3), X1.4 (C1)
unnamed: U5.8 (OUT4), X1.5 (D1)
unnamed: U7.1 (IN1), X1.1 (Q1)
unnamed: U7.2 (IN2), X1.13 (Q2)
unnamed: U9.5 (OUT1), X1.9 (A2)
unnamed: U9.6 (OUT2), X1.10 (B2)
unnamed: U9.7 (OUT3), X1.11 (C2)
unnamed: U9.8 (OUT4), X1.12 (D2)
a1: U1.~, U5.1 (IN1), v1.1 (+)
a2: U9.1 (IN1), U13.~, v8.1 (+)
b1: U3.~, U5.2 (IN2), v2.1 (+)
b2: U9.2 (IN2), U12.~, v7.1 (+)
c1: U4.~, U5.3 (IN3), v3.1 (+)
c2: U9.4 (IN4), U10.~, v5.1 (+)
d1: U2.~, U5.4 (IN4), v4.1 (+)
d2: U9.3 (IN3), U11.~, v6.1 (+)
eSim_GND: v1.2 (-), v2.2 (-), v3.2 (-), v4.2 (-), v5.2 (-), v6.2 (-), v7.2 (-), v8.2 (-)
q1: U6.~, U7.3 (OUT1)
q2: U7.4 (OUT4), U8.~

Notes on the sheet:
4012 IC Characteristics
