FOSSEE/eSim/Examples/Analysis_Of_Digital_IC/4_Input_NAND_Charcateristics/4012.sch

## KiCad design Examples/Analysis_Of_Digital_IC/4_Input_NAND_Charcateristics/4012.sch (2020-03-04)

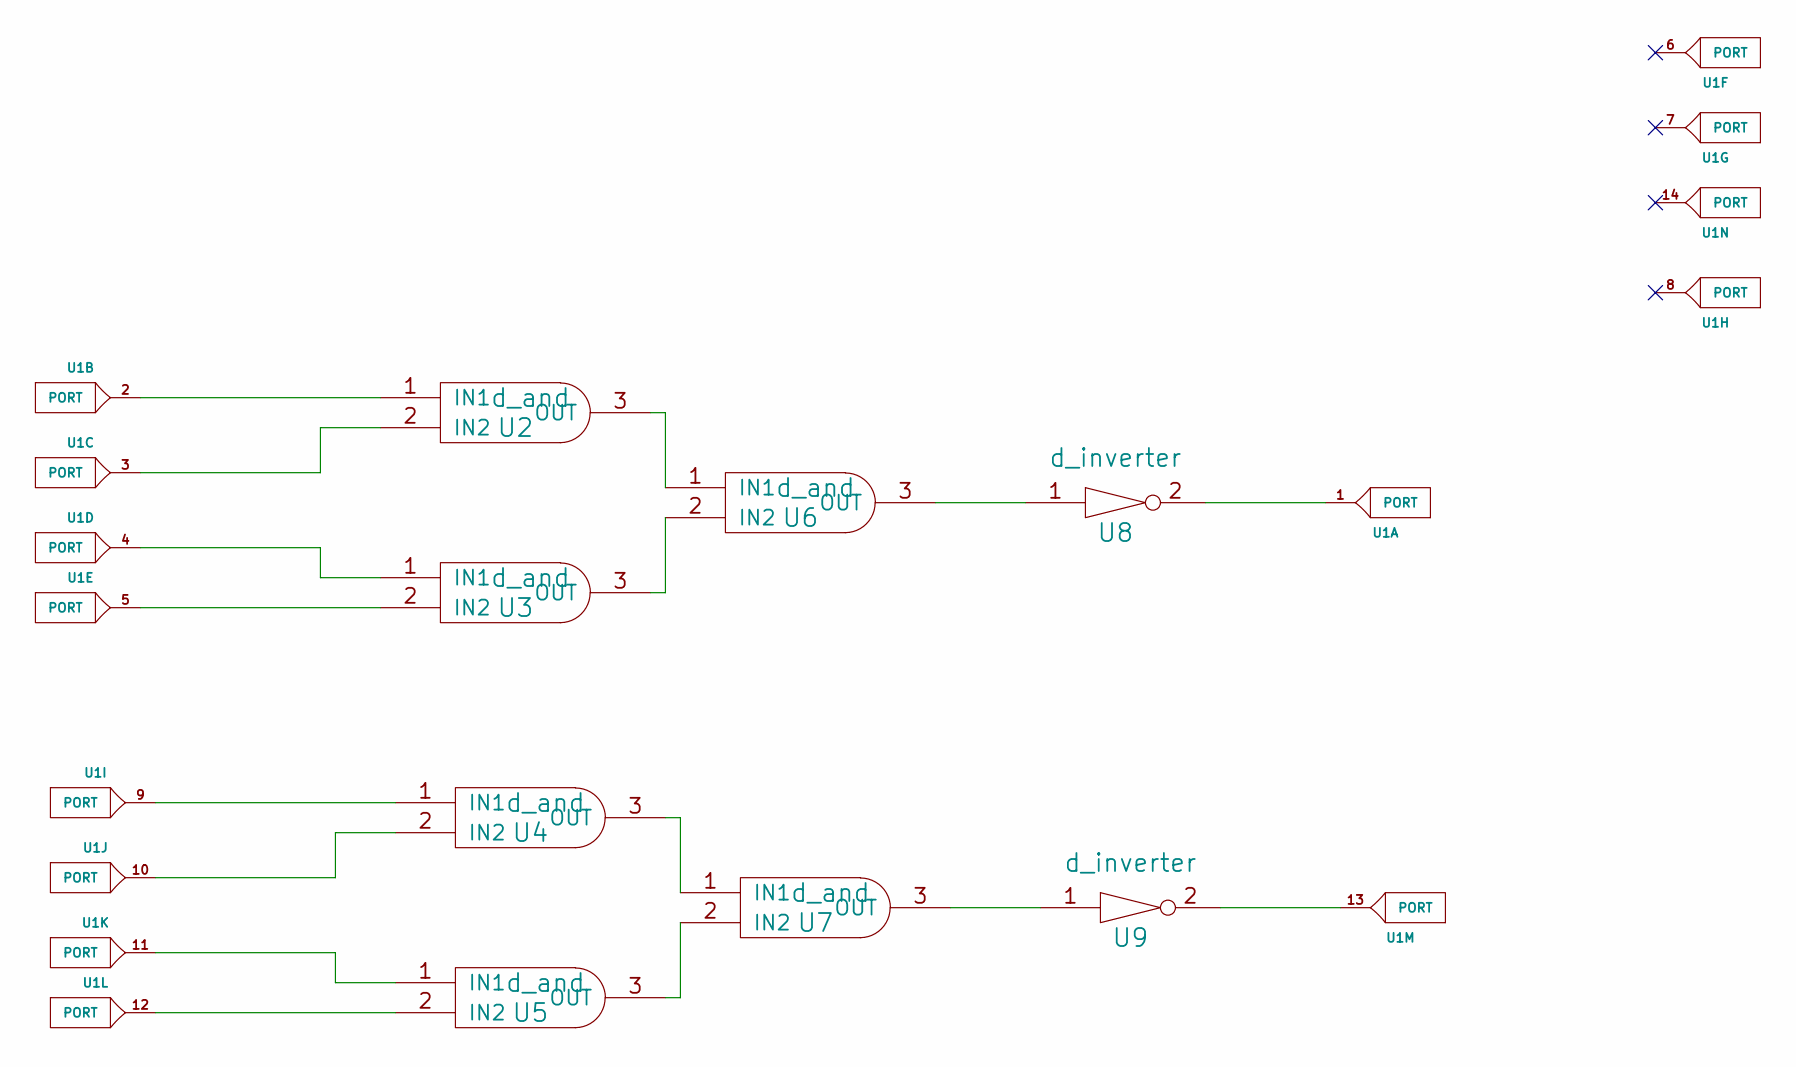
[picture p48: schematic 4012.sch]

Parts:
U1: PORT
U2, U3, U4, U5, U6, U7: d_and
U8, U9: d_inverter

Connections:
unnamed: U1.1, U8.2
unnamed: U1.2, U2.1 (IN1)
unnamed: U1.3, U2.2 (IN2)
unnamed: U1.4, U3.1 (IN1)
unnamed: U1.5, U3.2 (IN2)
unnamed: U1.9, U4.1 (IN1)
unnamed: U1.10, U4.2 (IN2)
unnamed: U1.11, U5.1 (IN1)
unnamed: U1.12, U5.2 (IN2)
unnamed: U1.13, U9.2
unnamed: U2.3 (OUT), U6.1 (IN1)
unnamed: U3.3 (OUT), U6.2 (IN2)
unnamed: U4.3 (OUT), U7.1 (IN1)
unnamed: U5.3 (OUT), U7.2 (IN2)
unnamed: U6.3 (OUT), U8.1
unnamed: U7.3 (OUT), U9.1
