FOSSEE/eSim/Examples/Analysis_Of_Digital_IC/4_Input_NOR_Characteristics/4_Input_NOR_Characteristics.sch

## KiCad design Examples/Analysis_Of_Digital_IC/4_Input_NOR_Characteristics/4_Input_NOR_Characteristics.sch (2020-03-18)

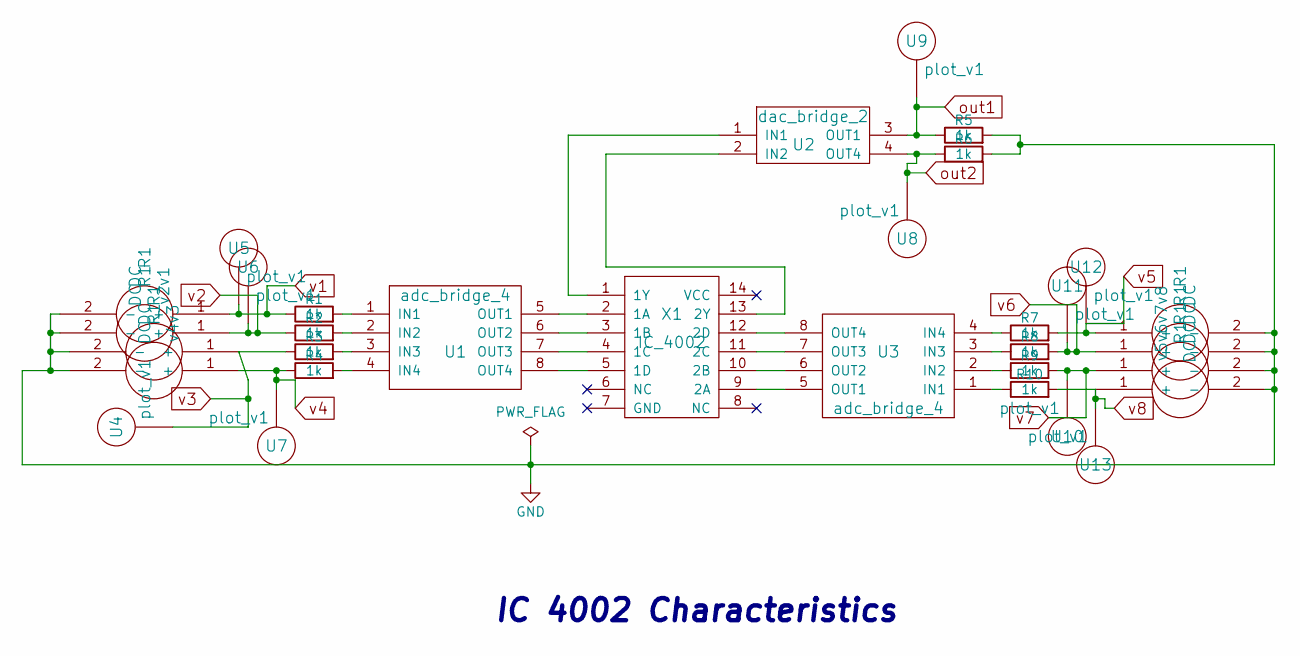
[picture p49: schematic 4_Input_NOR_Characteristics.sch]

Parts:
R1, R2, R3, R4, R5, R6, R7, R8, R9, R10: 1k
U1, U3: adc_bridge_4
U2: dac_bridge_2
U4, U5, U6, U7, U8, U9, U10, U11, U12, U13: plot_v1
X1: IC_4002
v1, v2, v3, v4, v5, v6, v7, v8: DC; R1

Connections:
GND: R5.2, R6.2, v1.2 (-), v2.2 (-), v3.2 (-), v4.2 (-), v5.2 (-), v6.2 (-), v7.2 (-), v8.2 (-)
unnamed: R1.2, U1.1 (IN1)
unnamed: R2.2, U1.2 (IN2)
unnamed: R3.2, U1.3 (IN3)
unnamed: R4.2, U1.4 (IN4)
unnamed: R7.1, U3.4 (IN4)
unnamed: R8.1, U3.3 (IN3)
unnamed: R9.1, U3.2 (IN2)
unnamed: R10.1, U3.1 (IN1)
unnamed: U1.5 (OUT1), X1.2 (1A)
unnamed: U1.6 (OUT2), X1.3 (1B)
unnamed: U1.7 (OUT3), X1.4 (1C)
unnamed: U1.8 (OUT4), X1.5 (1D)
unnamed: U2.1 (IN1), X1.1 (1Y)
unnamed: U2.2 (IN2), X1.13 (2Y)
unnamed: U3.5 (OUT1), X1.9 (2A)
unnamed: U3.6 (OUT2), X1.10 (2B)
unnamed: U3.7 (OUT3), X1.11 (2C)
unnamed: U3.8 (OUT4), X1.12 (2D)
out1: R5.1, U2.3 (OUT1), U9.~
out2: R6.1, U2.4 (OUT4), U8.~
v1: R1.1, U5.~, v1.1 (+)
v2: R2.1, U6.~, v2.1 (+)
v3: R3.1, U4.~, v3.1 (+)
v4: R4.1, U7.~, v4.1 (+)
v5: R7.2, U12.~, v8.1 (+)
v6: R8.2, U11.~, v7.1 (+)
v7: R9.2, U10.~, v6.1 (+)
v8: R10.2, U13.~, v5.1 (+)

Notes on the sheet:
IC 4002 Characteristics
