FOSSEE/eSim/Examples/Analysis_Of_Digital_IC/74LS04-test/74LS04-test.sch

## KiCad design Examples/Analysis_Of_Digital_IC/74LS04-test/74LS04-test.sch (2020-04-05)

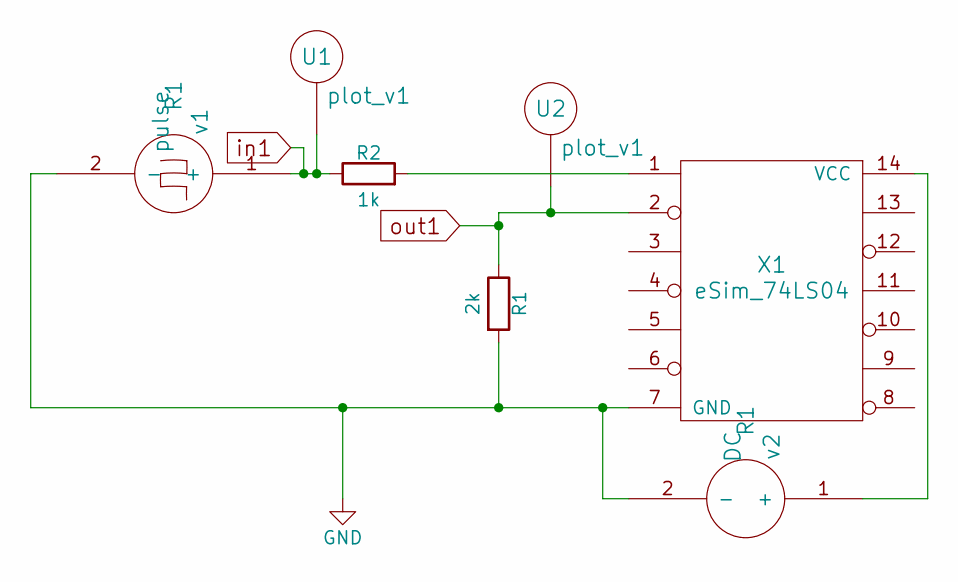
[picture p51: schematic 74LS04-test.sch]

Parts:
R1: 2k
R2: 1k
U1, U2: plot_v1
X1: eSim_74LS04
v1: pulse; R1
v2: DC; R1

Connections:
GND: R1.2, X1.7 (GND), v1.2 (-), v2.2 (-)
unnamed: R2.2, X1.1
unnamed: X1.14 (VCC), v2.1 (+)
in1: R2.1, U1.~, v1.1 (+)
out1: R1.1, U2.~, X1.2
