FOSSEE/eSim/Examples/Analysis_Of_Digital_IC/74LS04-test/74LS04.sch

## KiCad design Examples/Analysis_Of_Digital_IC/74LS04-test/74LS04.sch (2020-04-05)

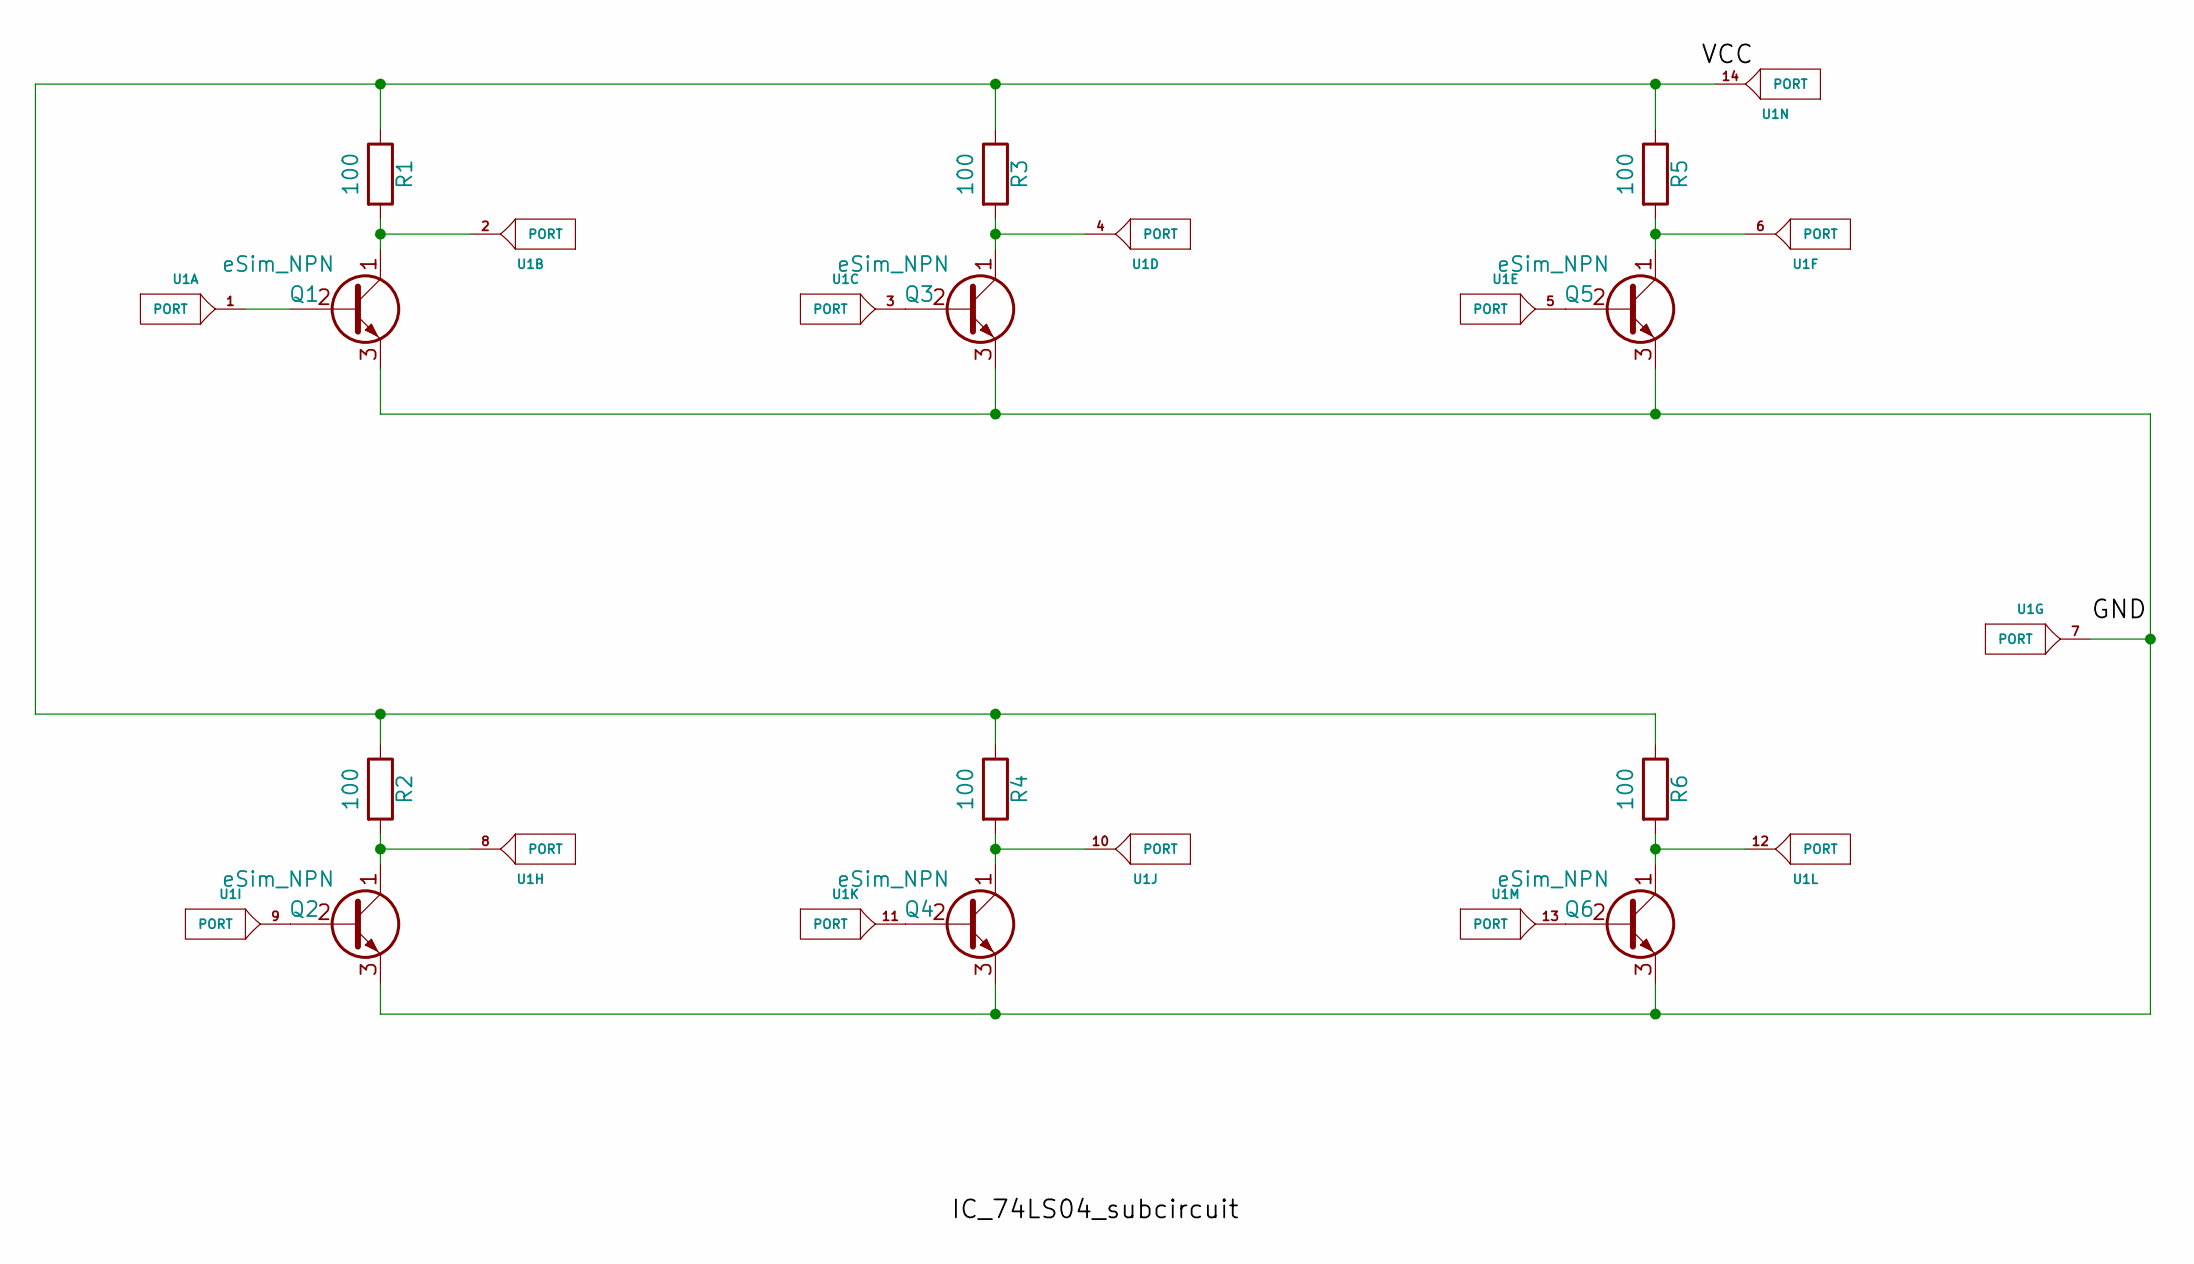
[picture p52: schematic 74LS04.sch]

Parts:
Q1, Q2, Q3, Q4, Q5, Q6: eSim_NPN
R1, R2, R3, R4, R5, R6: 100
U1: PORT

Connections:
unnamed: Q1.1 (C), R1.2, U1.2
unnamed: Q1.2 (B), U1.1
unnamed: Q1.3 (E), Q2.3 (E), Q3.3 (E), Q4.3 (E), Q5.3 (E), Q6.3 (E), U1.7
unnamed: Q2.1 (C), R2.2, U1.8
unnamed: Q2.2 (B), U1.9
unnamed: Q3.1 (C), R3.2, U1.4
unnamed: Q3.2 (B), U1.3
unnamed: Q4.1 (C), R4.2, U1.10
unnamed: Q4.2 (B), U1.11
unnamed: Q5.1 (C), R5.2, U1.6
unnamed: Q5.2 (B), U1.5
unnamed: Q6.1 (C), R6.2, U1.12
unnamed: Q6.2 (B), U1.13
unnamed: R1.1, R2.1, R3.1, R4.1, R5.1, R6.1, U1.14
