FOSSEE/eSim/Examples/Analysis_Of_Digital_IC/4073_test/4073.sch

## KiCad design Examples/Analysis_Of_Digital_IC/4073_test/4073.sch (2019-07-02)

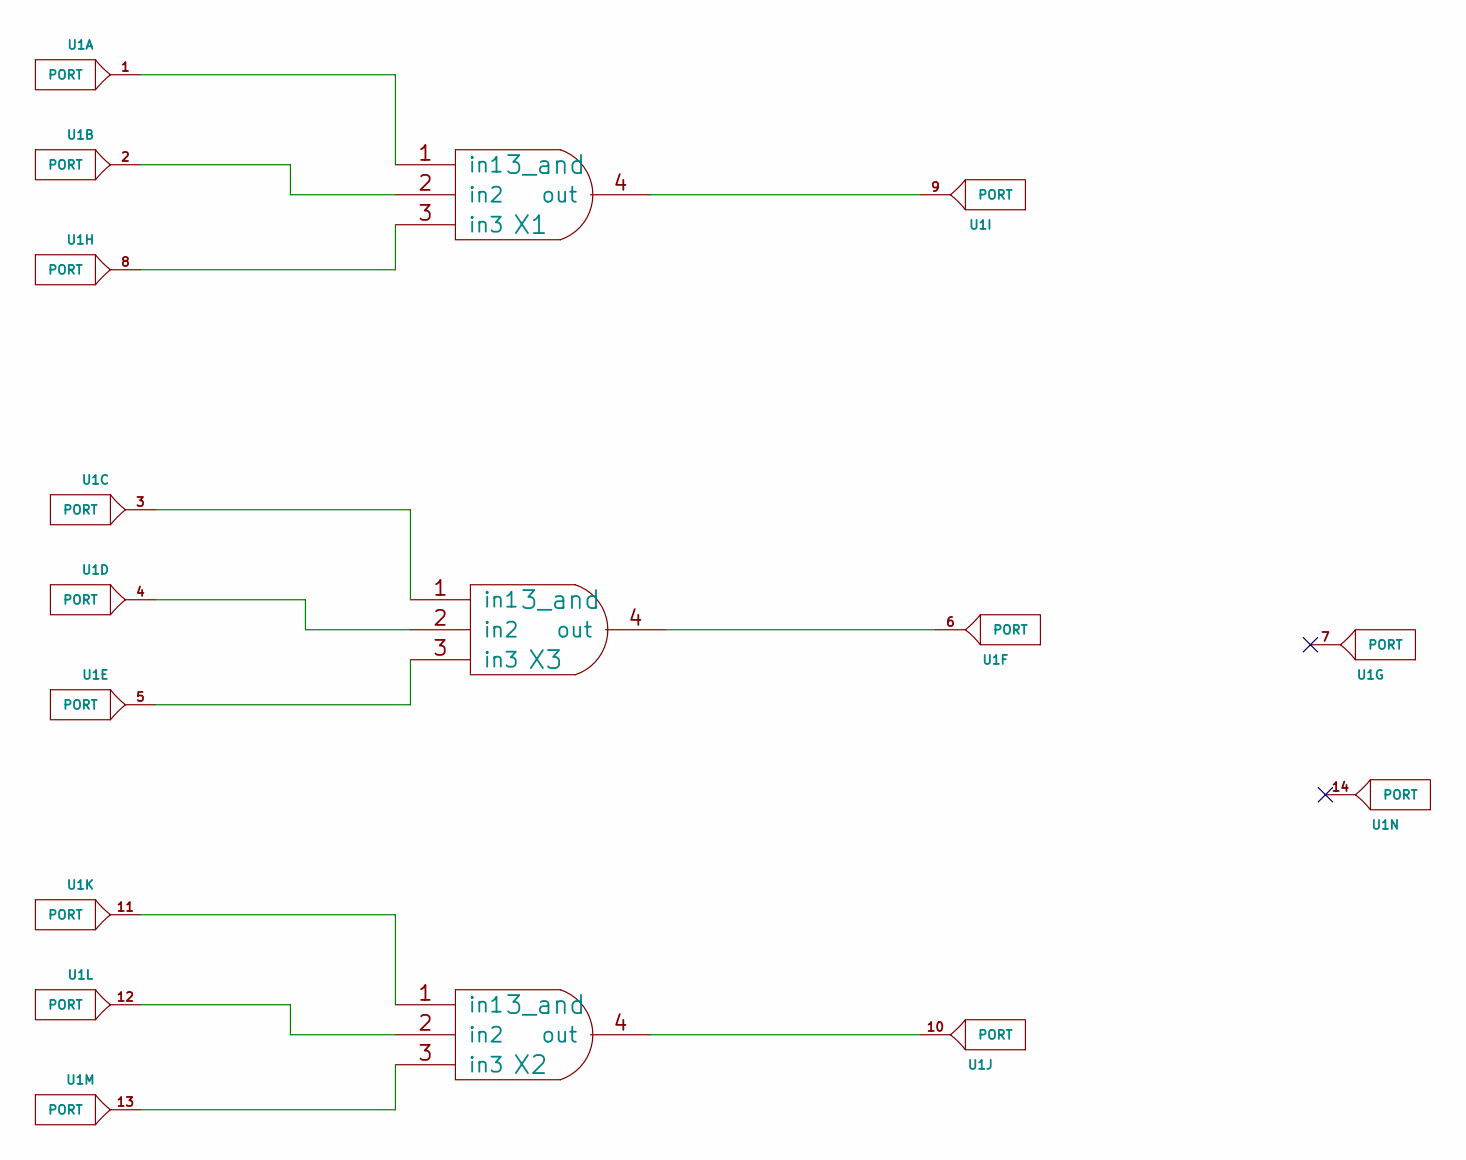
[picture p53: schematic 4073.sch]

Parts:
U1: PORT
X1, X2, X3: 3_and

Connections:
unnamed: U1.1, X1.1 (in1)
unnamed: U1.2, X1.2 (in2)
unnamed: U1.3, X3.1 (in1)
unnamed: U1.4, X3.2 (in2)
unnamed: U1.5, X3.3 (in3)
unnamed: U1.6, X3.4 (out)
unnamed: U1.8, X1.3 (in3)
unnamed: U1.9, X1.4 (out)
unnamed: U1.10, X2.4 (out)
unnamed: U1.11, X2.1 (in1)
unnamed: U1.12, X2.2 (in2)
unnamed: U1.13, X2.3 (in3)
