FOSSEE/eSim/Examples/Analysis_Of_Digital_IC/BCDToDecimalDecoder/4028.sch

## KiCad design Examples/Analysis_Of_Digital_IC/BCDToDecimalDecoder/4028.sch (2020-03-04)

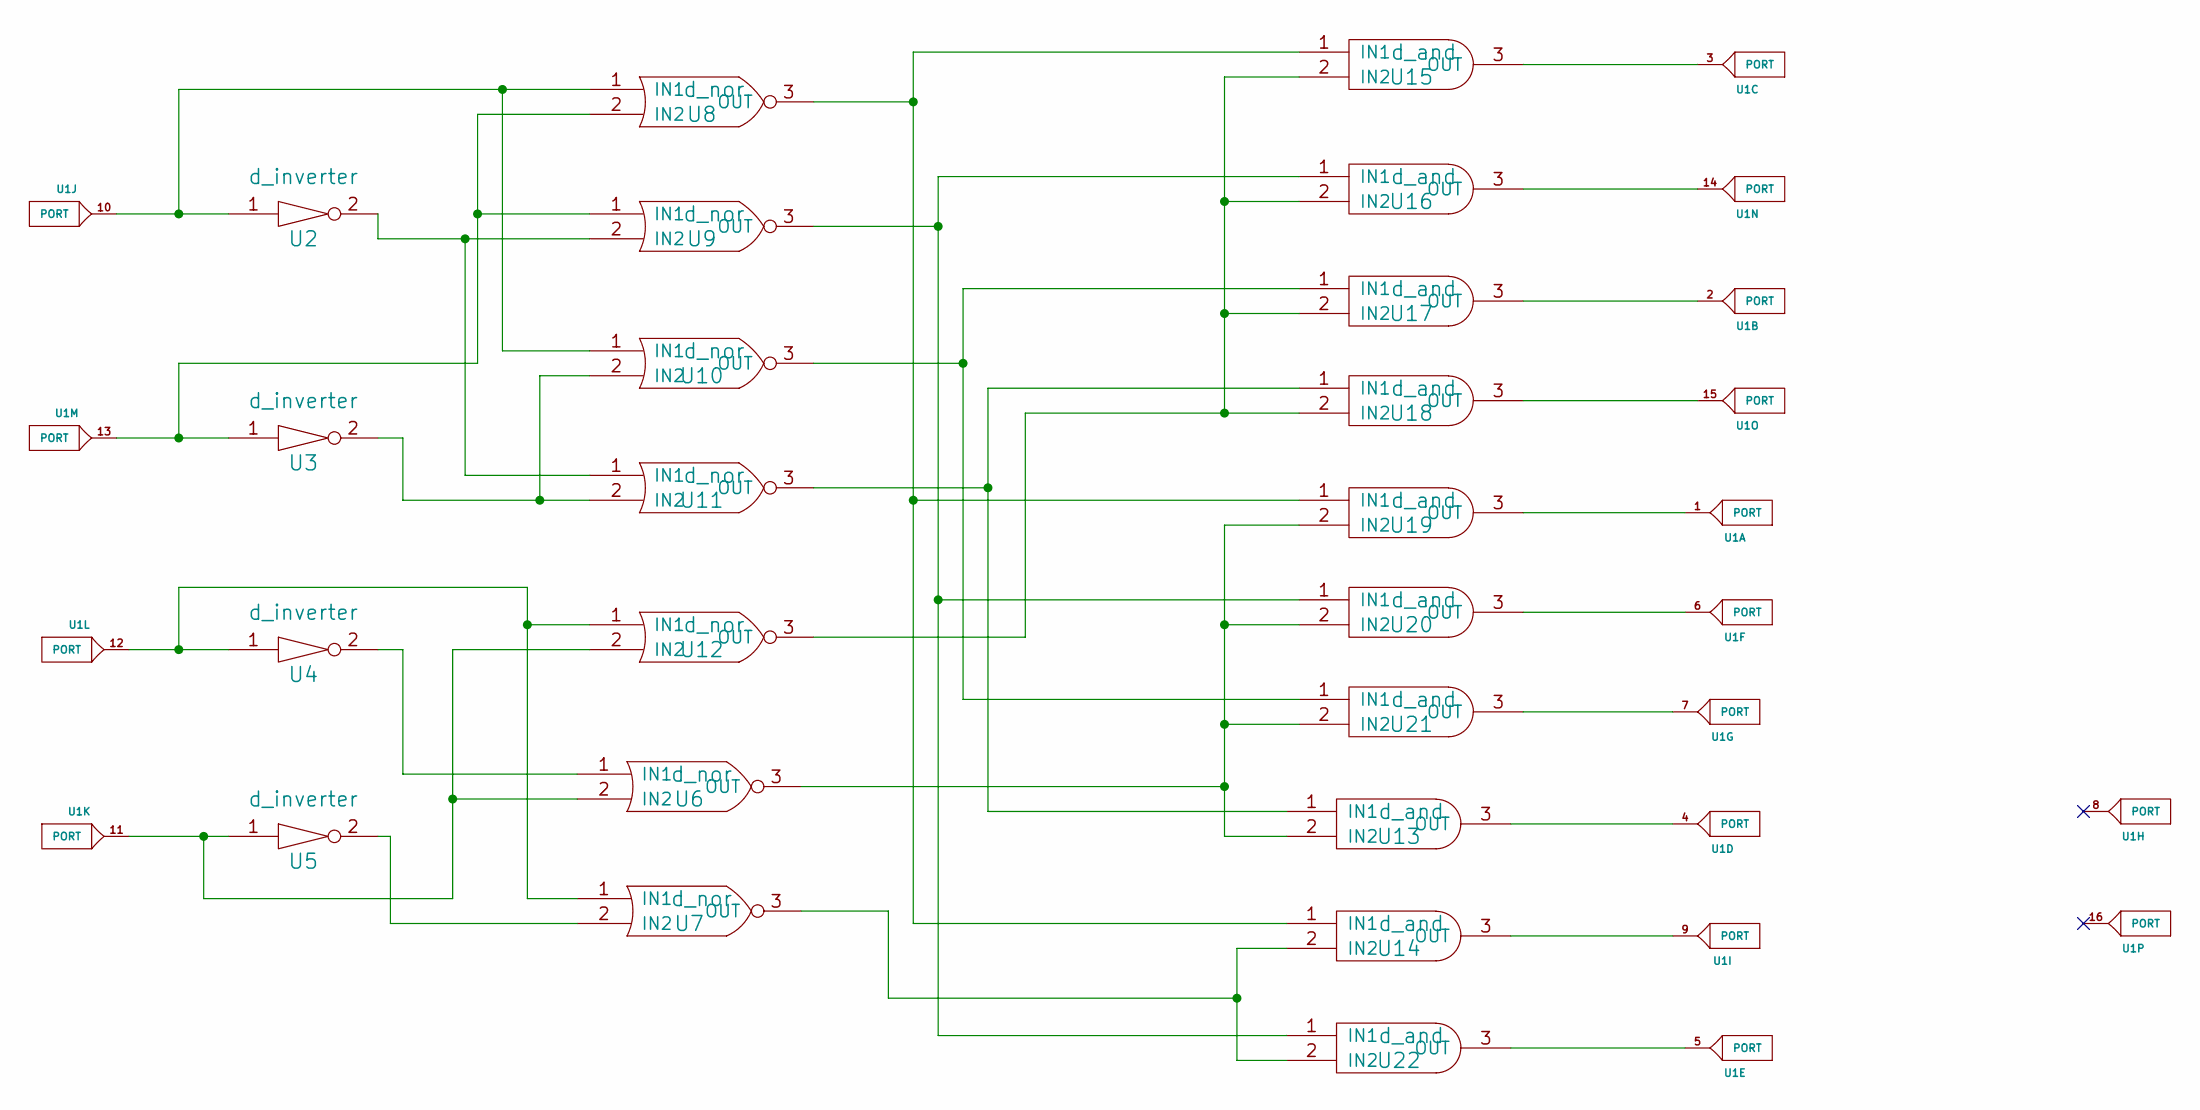
[picture p54: schematic 4028.sch]

Parts:
U1: PORT
U2, U3, U4, U5: d_inverter
U6, U7, U8, U9, U10, U11, U12: d_nor
U13, U14, U15, U16, U17, U18, U19, U20, U21, U22: d_and

Connections:
unnamed: U1.1, U19.3 (OUT)
unnamed: U1.2, U17.3 (OUT)
unnamed: U1.3, U15.3 (OUT)
unnamed: U1.4, U13.3 (OUT)
unnamed: U1.5, U22.3 (OUT)
unnamed: U1.6, U20.3 (OUT)
unnamed: U1.7, U21.3 (OUT)
unnamed: U1.9, U14.3 (OUT)
unnamed: U1.10, U2.1, U8.1 (IN1), U10.1 (IN1)
unnamed: U1.11, U5.1, U6.2 (IN2), U12.2 (IN2)
unnamed: U1.12, U4.1, U7.1 (IN1), U12.1 (IN1)
unnamed: U1.13, U3.1, U8.2 (IN2), U9.1 (IN1)
unnamed: U1.14, U16.3 (OUT)
unnamed: U1.15, U18.3 (OUT)
unnamed: U4.2, U6.1 (IN1)
unnamed: U5.2, U7.2 (IN2)
unnamed: U3.2, U10.2 (IN2), U11.2 (IN2)
unnamed: U10.3 (OUT), U17.1 (IN1), U21.1 (IN1)
unnamed: U2.2, U9.2 (IN2), U11.1 (IN1)
unnamed: U11.3 (OUT), U13.1 (IN1), U18.1 (IN1)
unnamed: U12.3 (OUT), U15.2 (IN2), U16.2 (IN2), U17.2 (IN2), U18.2 (IN2)
unnamed: U6.3 (OUT), U13.2 (IN2), U19.2 (IN2), U20.2 (IN2), U21.2 (IN2)
unnamed: U8.3 (OUT), U14.1 (IN1), U15.1 (IN1), U19.1 (IN1)
unnamed: U7.3 (OUT), U14.2 (IN2), U22.2 (IN2)
unnamed: U9.3 (OUT), U16.1 (IN1), U20.1 (IN1), U22.1 (IN1)
