FOSSEE/eSim/Examples/Analysis_Of_Digital_IC/BCDToDecimalDecoder/BCDToDecimalDecoder.sch

## KiCad design Examples/Analysis_Of_Digital_IC/BCDToDecimalDecoder/BCDToDecimalDecoder.sch (2020-03-18)

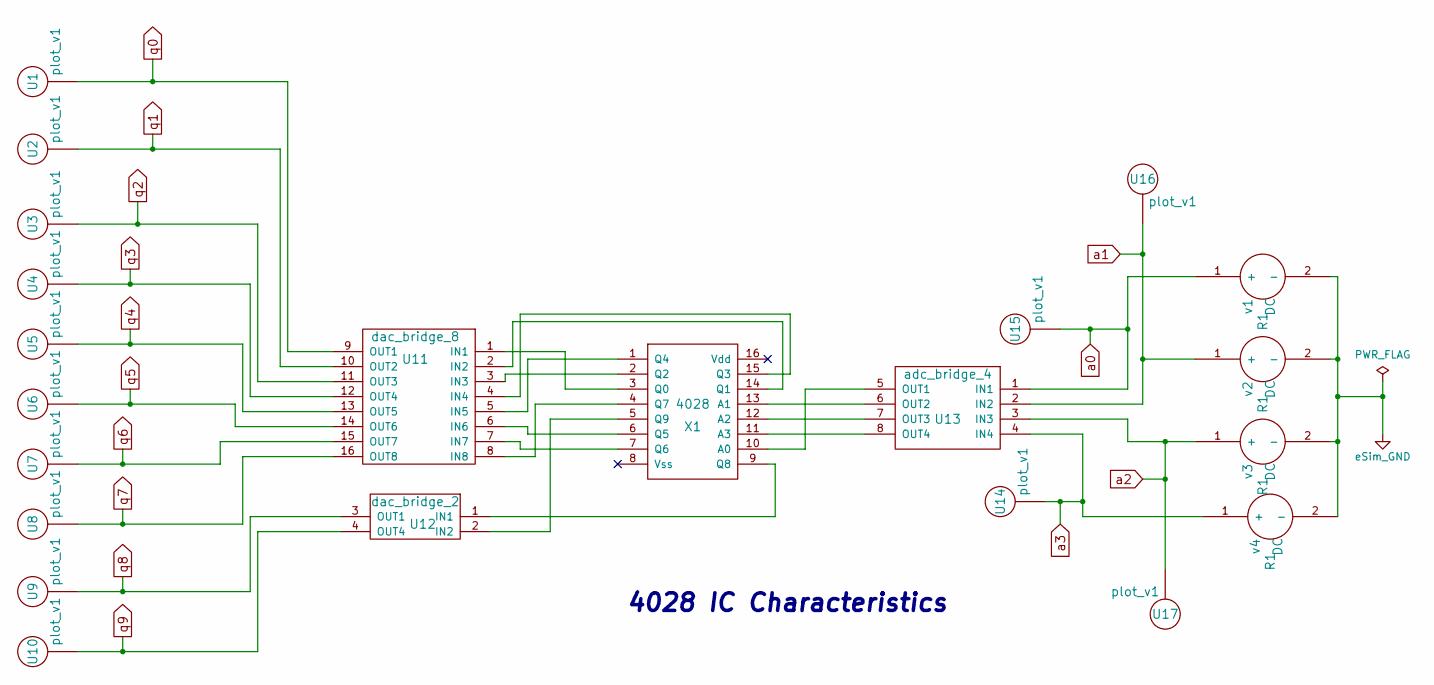
[picture p55: schematic BCDToDecimalDecoder.sch]

Parts:
U1, U2, U3, U4, U5, U6, U7, U8, U9, U10, U14, U15, U16, U17: plot_v1
U11: dac_bridge_8
U12: dac_bridge_2
U13: adc_bridge_4
X1: 4028
v1, v2, v3, v4: DC; R1

Connections:
unnamed: U11.1 (IN1), X1.3 (Q0)
unnamed: U11.2 (IN2), X1.14 (Q1)
unnamed: U11.3 (IN3), X1.2 (Q2)
unnamed: U11.4 (IN4), X1.15 (Q3)
unnamed: U11.5 (IN5), X1.1 (Q4)
unnamed: U11.6 (IN6), X1.6 (Q5)
unnamed: U11.7 (IN7), X1.7 (Q6)
unnamed: U11.8 (IN8), X1.4 (Q7)
unnamed: U12.1 (IN1), X1.9 (Q8)
unnamed: U12.2 (IN2), X1.5 (Q9)
unnamed: U13.5 (OUT1), X1.10 (A0)
unnamed: U13.6 (OUT2), X1.13 (A1)
unnamed: U13.7 (OUT3), X1.12 (A2)
unnamed: U13.8 (OUT4), X1.11 (A3)
a0: U13.1 (IN1), U15.~, v1.1 (+)
a1: U13.2 (IN2), U16.~, v2.1 (+)
a2: U13.3 (IN3), U17.~, v3.1 (+)
a3: U13.4 (IN4), U14.~, v4.1 (+)
eSim_GND: v1.2 (-), v2.2 (-), v3.2 (-), v4.2 (-)
q0: U1.~, U11.9 (OUT1)
q1: U2.~, U11.10 (OUT2)
q2: U3.~, U11.11 (OUT3)
q3: U4.~, U11.12 (OUT4)
q4: U5.~, U11.13 (OUT5)
q5: U6.~, U11.14 (OUT6)
q6: U7.~, U11.15 (OUT7)
q7: U8.~, U11.16 (OUT8)
q8: U9.~, U12.3 (OUT1)
q9: U10.~, U12.4 (OUT4)

Notes on the sheet:
4028 IC Characteristics
