FOSSEE/eSim/Examples/Mixed_Signal/Cmosinverter/Cmosinverter.sch

## KiCad design Examples/Mixed_Signal/Cmosinverter/Cmosinverter.sch (2020-03-04)

Schematic: Cmosinverter.sch

Parts:
U1: inverter
U2, U3, U4, U5, U6, U7, U8: plot_v1
U9: adc_bridge_1
U10: dac_bridge_1
X1, X2, X3, X4, X5, X6: INVCMOS
