FOSSEE/eSim/Examples/Mixed_Signal/PWM_Decremental/PWM_Decremental.sch

## KiCad design Examples/Mixed_Signal/PWM_Decremental/PWM_Decremental.sch (2020-03-04)

Schematic: PWM_Decremental.sch

Parts:
C1: 1u
R1: 1k
U1, U3, U6, U7, U9: plot_v1
U2: pwmdecrement
U4, U5: adc_bridge_1
U8: dac_bridge_1
X1: lm_741
v1: 3; R1
v2: 9v; R1
v3: -9v; R1
v4: pulse; R1
