FOSSEE/eSim/Examples/Mixed_Signal/custom_mixed_signal/custom_mixed_signal.sch

## KiCad design Examples/Mixed_Signal/custom_mixed_signal/custom_mixed_signal.sch (2020-03-17)

Schematic: custom_mixed_signal.sch

Parts:
C1: 47u
C2: 100u
R1: 100
R3: 1k
U1, U3, U4, U7, U9, U10: plot_v1
U2: customblock
U5, U6: adc_bridge_1
U8: dac_bridge_1
X1: lm_741
v1: pwl; R1
v2: 9v; R1
v3: -9v; R1
v5: pulse; R1
