FOSSEE/eSim/src/converter/schematic_converters/eSim_PSpice_to_KiCad_Python_Parser.sch

## KiCad design src/converter/schematic_converters/eSim_PSpice_to_KiCad_Python_Parser.sch (2024-09-12)

Schematic: eSim_PSpice_to_KiCad_Python_Parser.sch

Parts:
C1, C2: 3.183u
C3: 6.366u
R1, R2: 10K
R4: 25k
R5: 15k
R6, R7, R8: 10k
R9, R11, R12: r
R10: 5k
R13: 0.5k
U2, U3, U4, U5, U6: OPAMP
V1, V2: 10V
nodeMarker: nodeMarker
titleblk: titleblk
